AndreiBertescu/FPGA_Cosmic_Radiation_Sensor/Thesis latex project/Anexe/Prima pagina.docx

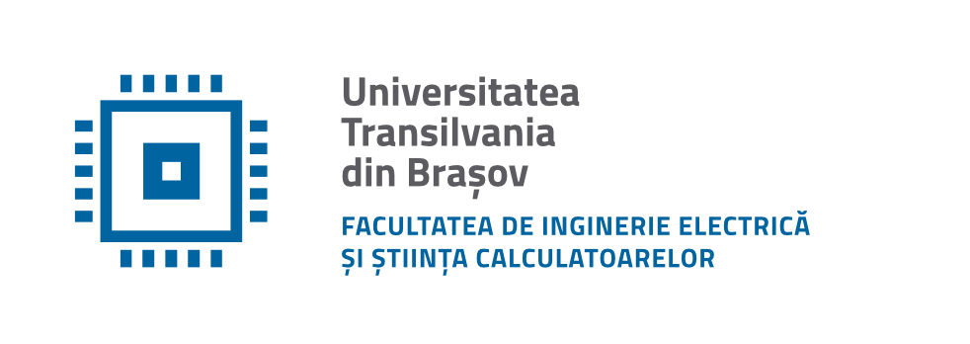
[picture p34: figure]

PROIECT DE DIPLOMĂ

Conducători științifici:

Prof. dr. ing. IVANOVICI Mihail Laurențiu

Șef lucr. dr. ing. POPA Ștefan

Absolvent:

BERTESCU Andrei

BRAȘOV, 2026

Departamentul: Electronică și Calculatoare

Programul de studii: Calculatoare

BERTESCU Andrei

Senzor inteligent de detecție a radiației cosmice, bazat pe FPGA, destinat nanosateliților

Conducători științifici:

Prof. dr. ing. IVANOVICI Mihail Laurențiu

Șef lucr. dr. ing. POPA Ștefan

Brașov, 2026
