AndreiBertescu/FPGA_Cosmic_Radiation_Sensor/Kicad PCB projects/Rev_3.2/PCB_photos/JLCPCB_photos/JLC_price.png

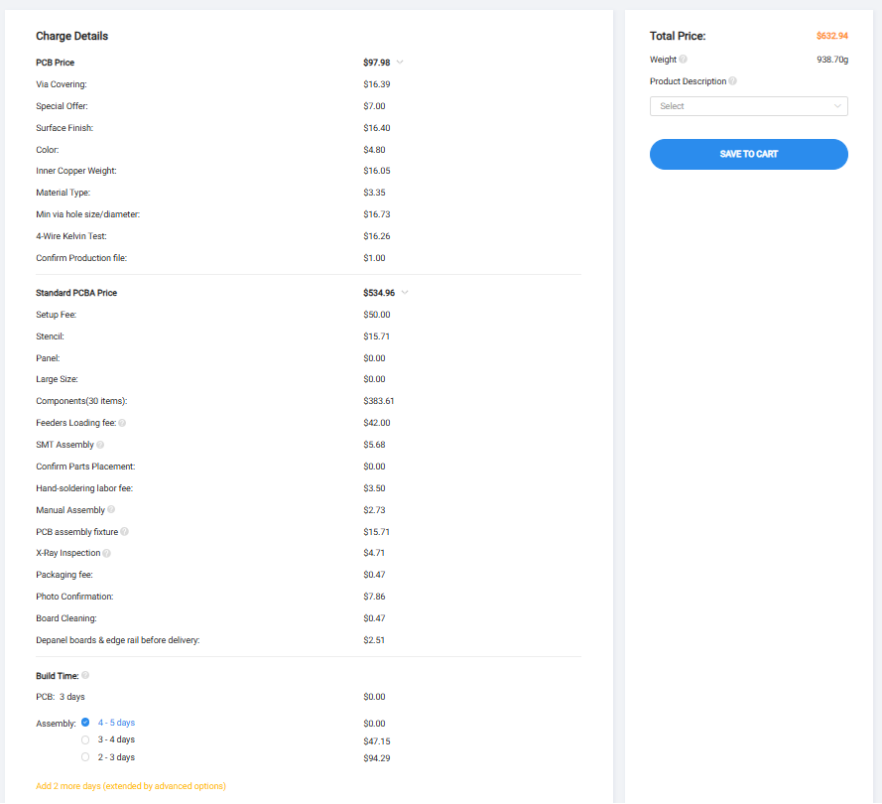
Kicad PCB projects/Rev_3.2/PCB_photos/JLCPCB_photos/JLC_price.png
