AndreiBertescu/FPGA_Cosmic_Radiation_Sensor/Kicad PCB projects/Rev_3.2/PCB_photos/JLCPCB_photos/Real_bottom.jpg

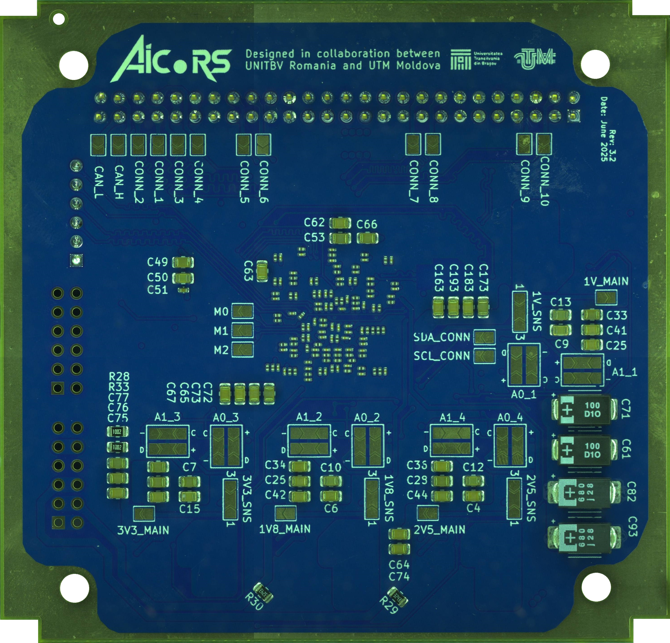
Kicad PCB projects/Rev_3.2/PCB_photos/JLCPCB_photos/Real_bottom.jpg
