AndreiBertescu/FPGA_Cosmic_Radiation_Sensor/Kicad PCB projects/Rev_3.2/PCB_photos/JLCPCB_photos/Render_bottom.png

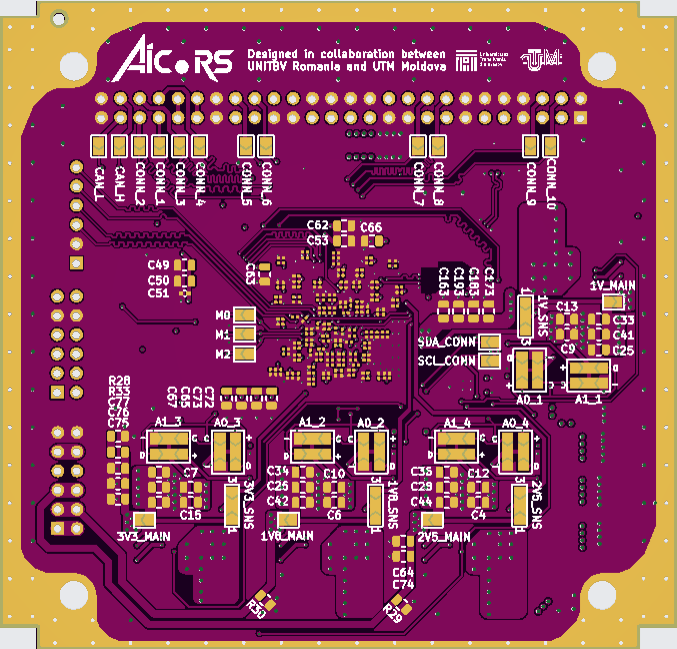
Kicad PCB projects/Rev_3.2/PCB_photos/JLCPCB_photos/Render_bottom.png
