AndreiBertescu/FPGA_Cosmic_Radiation_Sensor/Kicad PCB projects/Rev_3.2/PCB_photos/JLCPCB_photos/Render_top.png

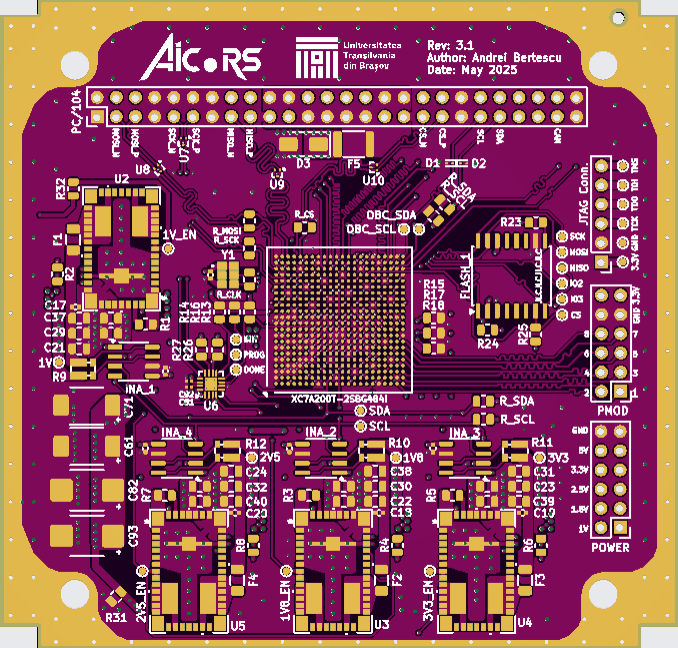
Kicad PCB projects/Rev_3.2/PCB_photos/JLCPCB_photos/Render_top.png
