AndreiBertescu/FPGA_Cosmic_Radiation_Sensor/Kicad PCB projects/Rev_3.2/PCB_photos/JLCPCB_photos/Xray_1.jpg

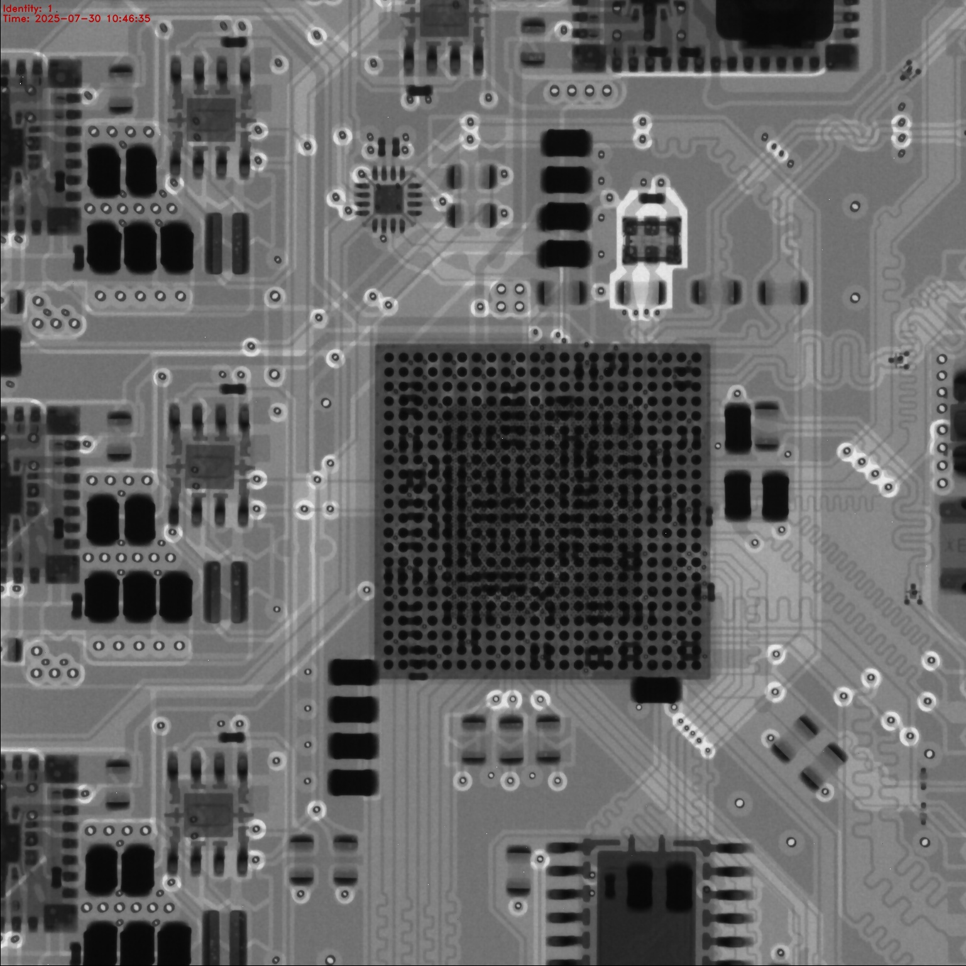
Kicad PCB projects/Rev_3.2/PCB_photos/JLCPCB_photos/Xray_1.jpg
