AndreiBertescu/FPGA_Cosmic_Radiation_Sensor/Kicad PCB projects/Rev_3.2/PCB_photos/KiCad_photos/3D_BOTTOM.png

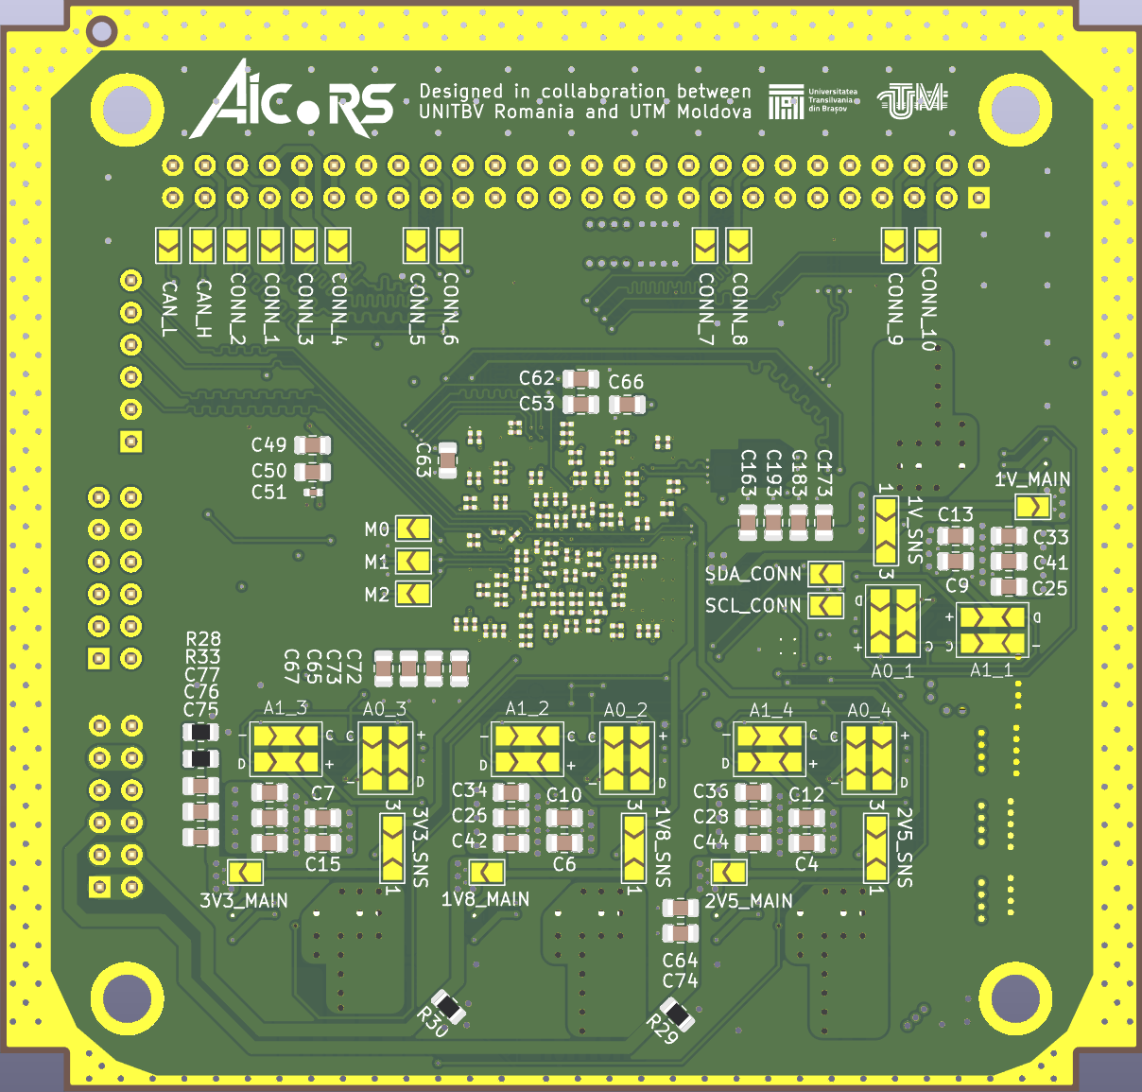
Kicad PCB projects/Rev_3.2/PCB_photos/KiCad_photos/3D_BOTTOM.png
