AndreiBertescu/FPGA_Cosmic_Radiation_Sensor/Kicad PCB projects/Rev_3.2/PCB_photos/KiCad_photos/hw_layout_bottom.png

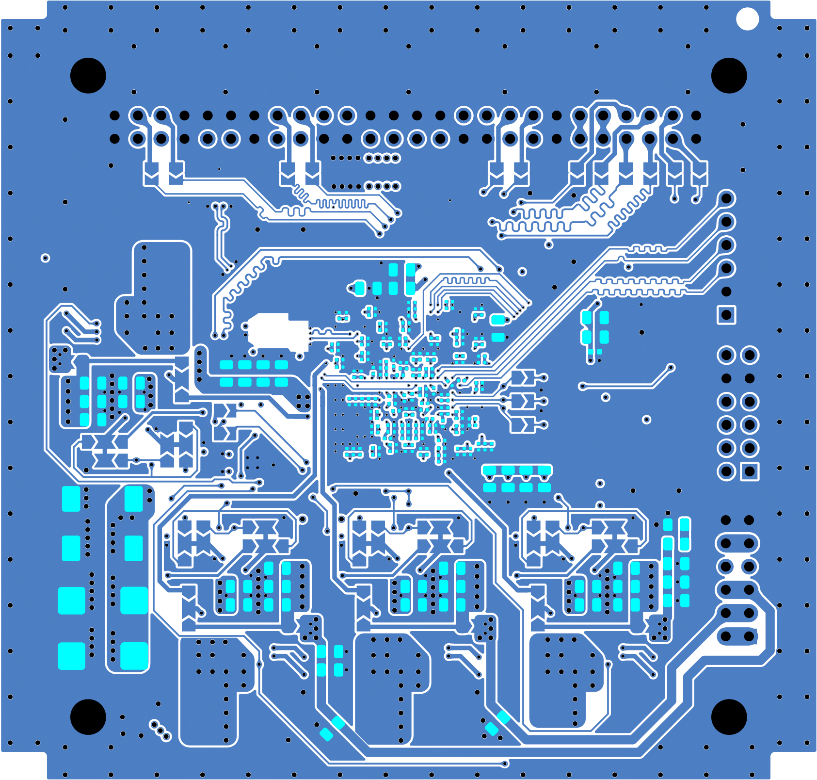
Kicad PCB projects/Rev_3.2/PCB_photos/KiCad_photos/hw_layout_bottom.png
