AndreiBertescu/FPGA_Cosmic_Radiation_Sensor/Kicad PCB projects/Rev_3.2/PCB_photos/KiCad_photos/hw_layout_top.png

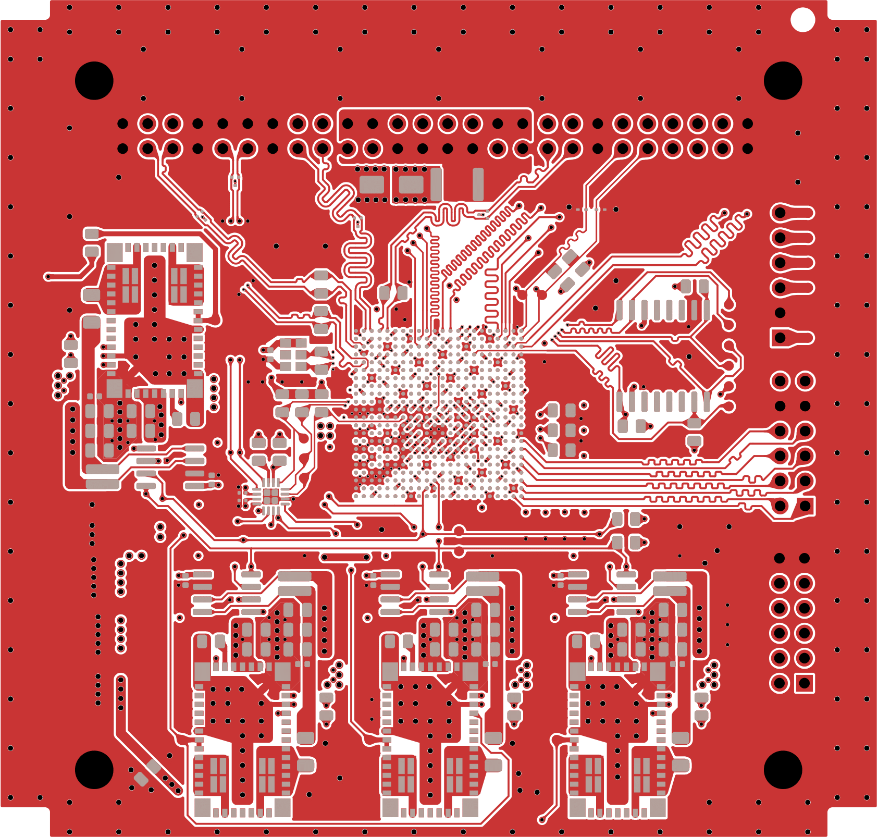
Kicad PCB projects/Rev_3.2/PCB_photos/KiCad_photos/hw_layout_top.png
