AndreiBertescu/FPGA_Cosmic_Radiation_Sensor/Thesis latex project/Images/eye_diagram.png

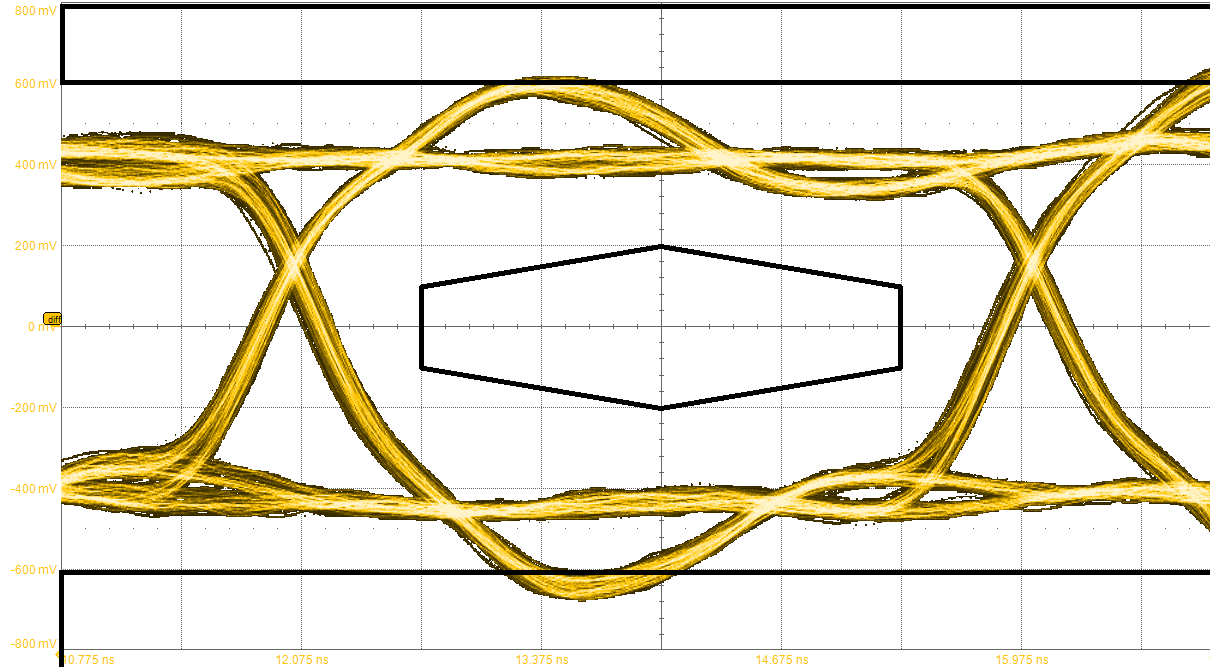
Thesis latex project/Images/eye_diagram.png
