AndreiBertescu/FPGA_Cosmic_Radiation_Sensor/Thesis latex project/Images/ferrite_bead_interference_3.png

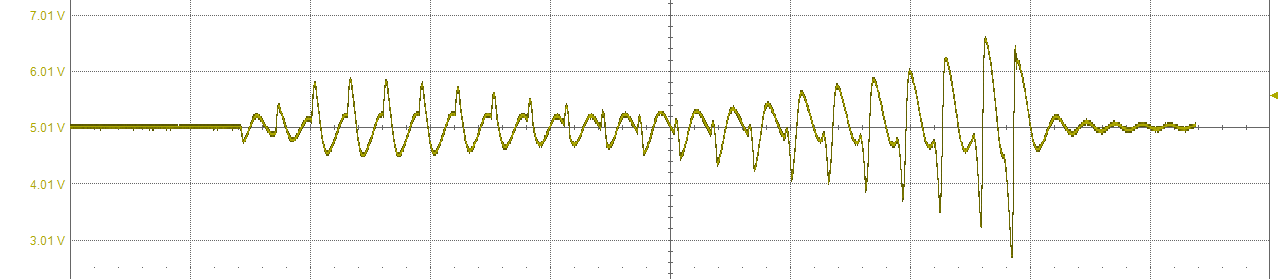
Thesis latex project/Images/ferrite_bead_interference_3.png
