AndreiBertescu/FPGA_Cosmic_Radiation_Sensor/Thesis latex project/Images/Main_sim.png

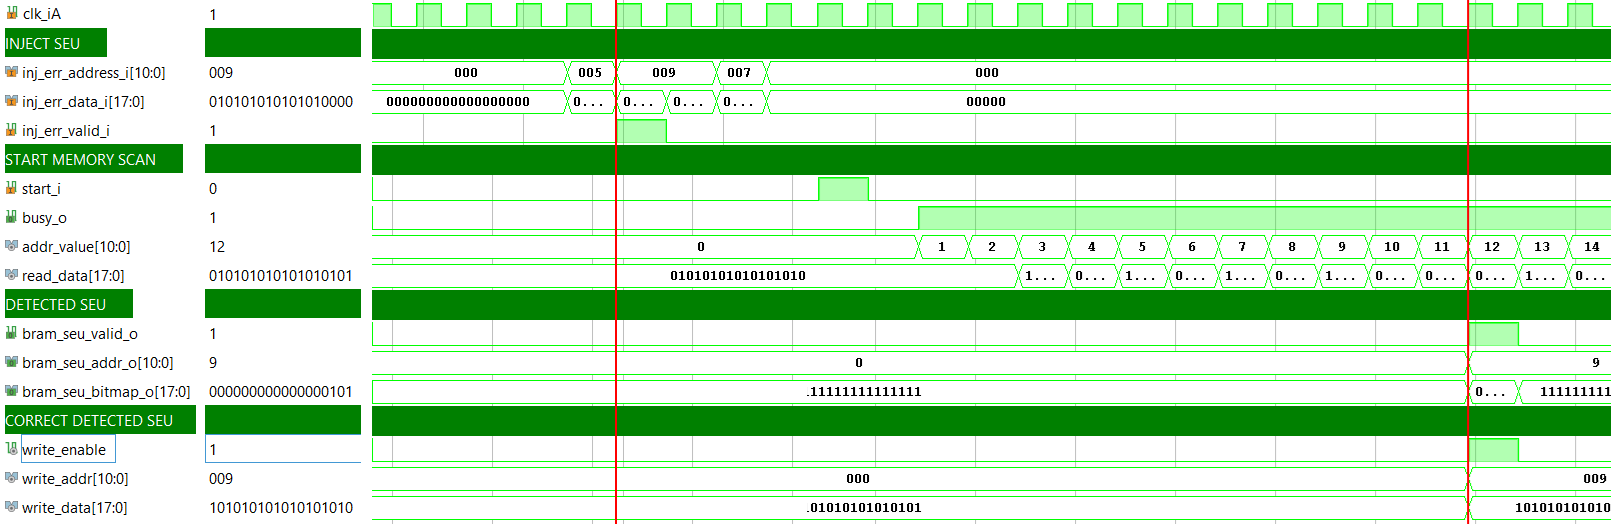
Thesis latex project/Images/Main_sim.png
