AndreiBertescu/FPGA_Cosmic_Radiation_Sensor/Thesis latex project/Images/power_spike.png

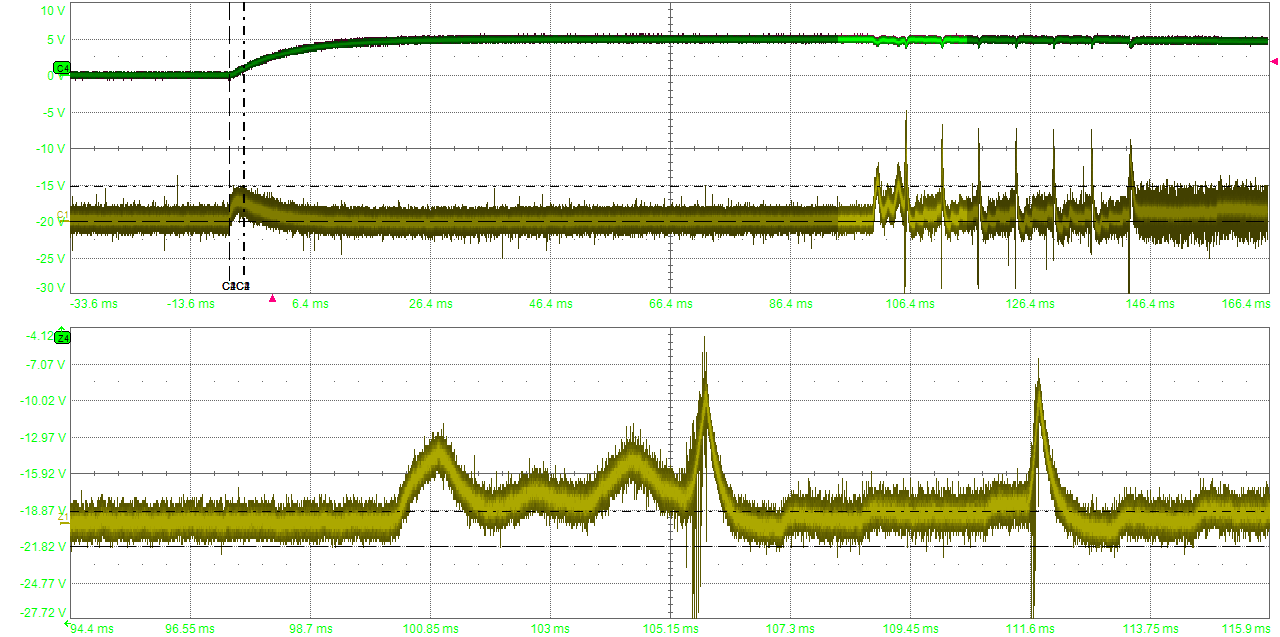
Thesis latex project/Images/power_spike.png
