AndreiBertescu/FPGA_Cosmic_Radiation_Sensor/Arduino Test projects/Arduino_SPI_slave/SPI_Frame_0.png

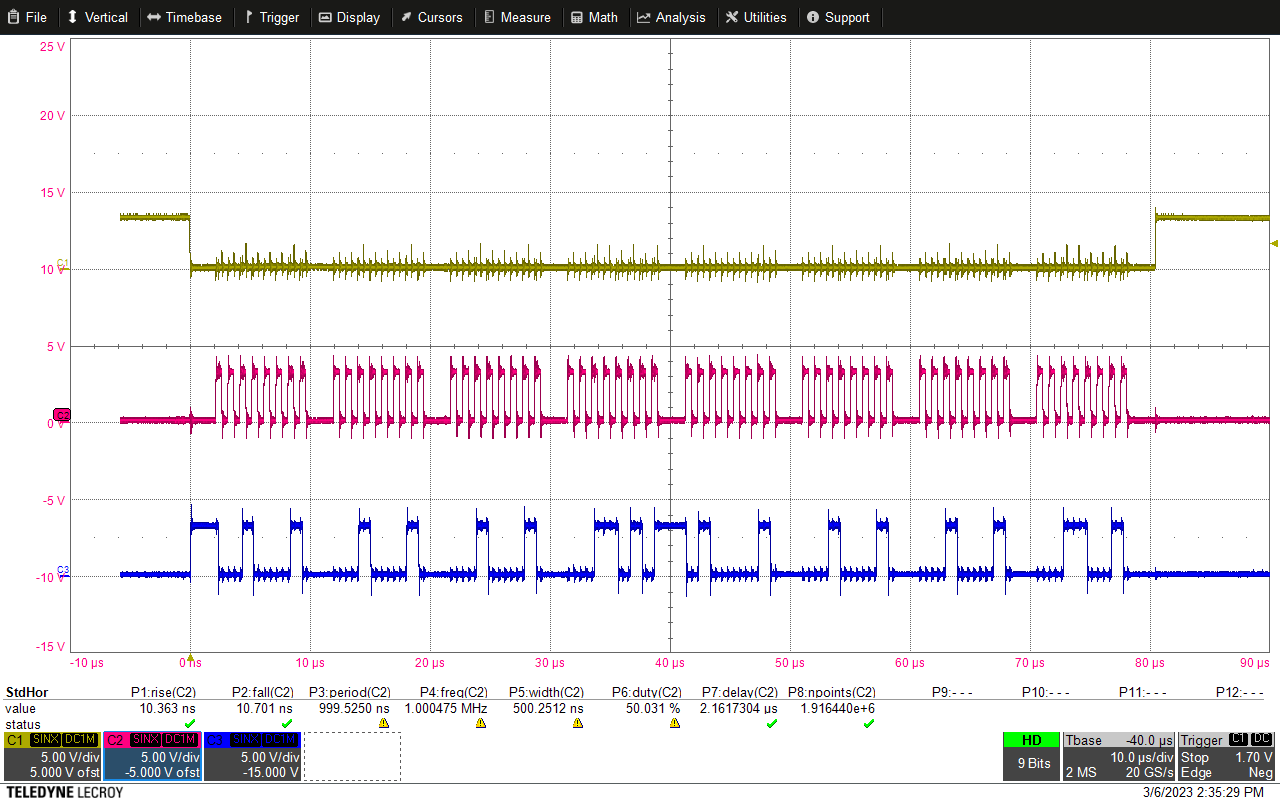
Arduino Test projects/Arduino_SPI_slave/SPI_Frame_0.png
