AndreiBertescu/FPGA_Cosmic_Radiation_Sensor/Kicad PCB projects/Test_photos/Rev_3/100MHz_clock_jitter_kit.png

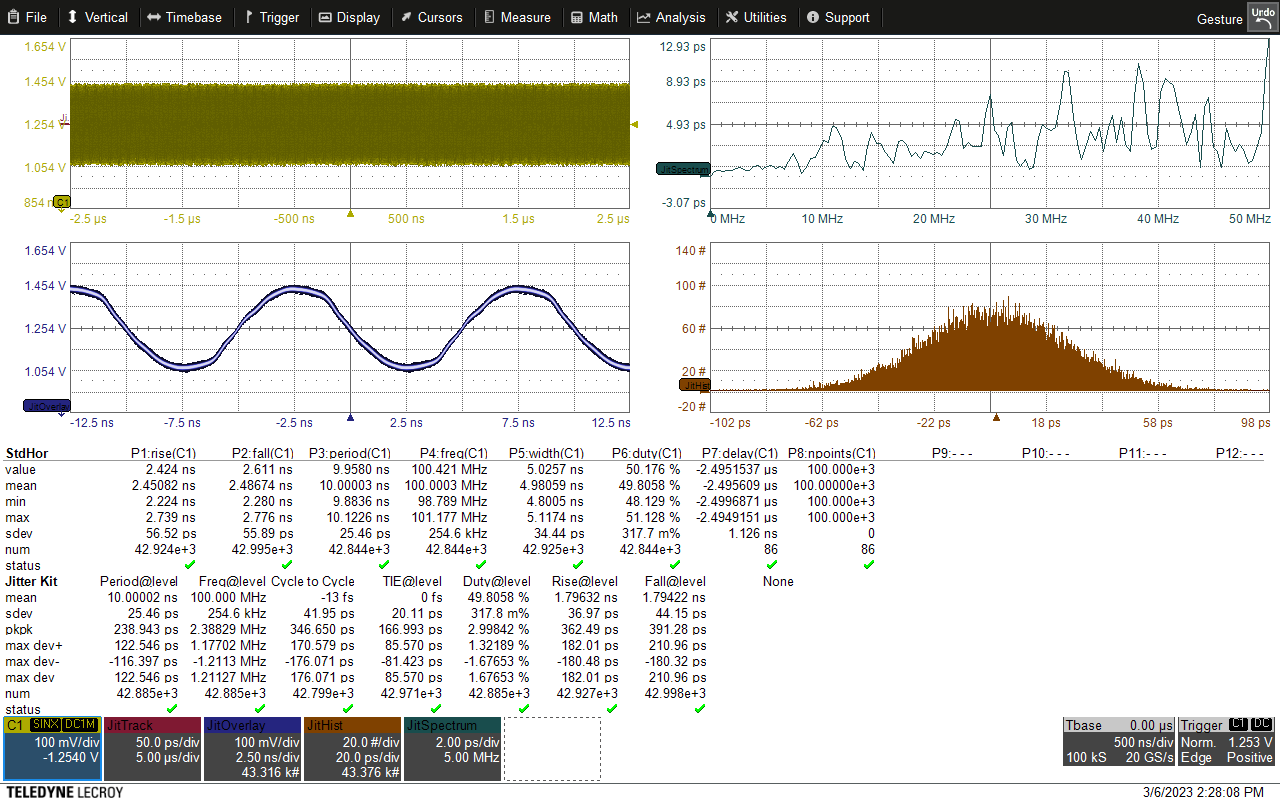
Kicad PCB projects/Test_photos/Rev_3/100MHz_clock_jitter_kit.png
