AndreiBertescu/FPGA_Cosmic_Radiation_Sensor/Kicad PCB projects/Test_photos/Rev_3/Eye_conn_10_250MHz.png

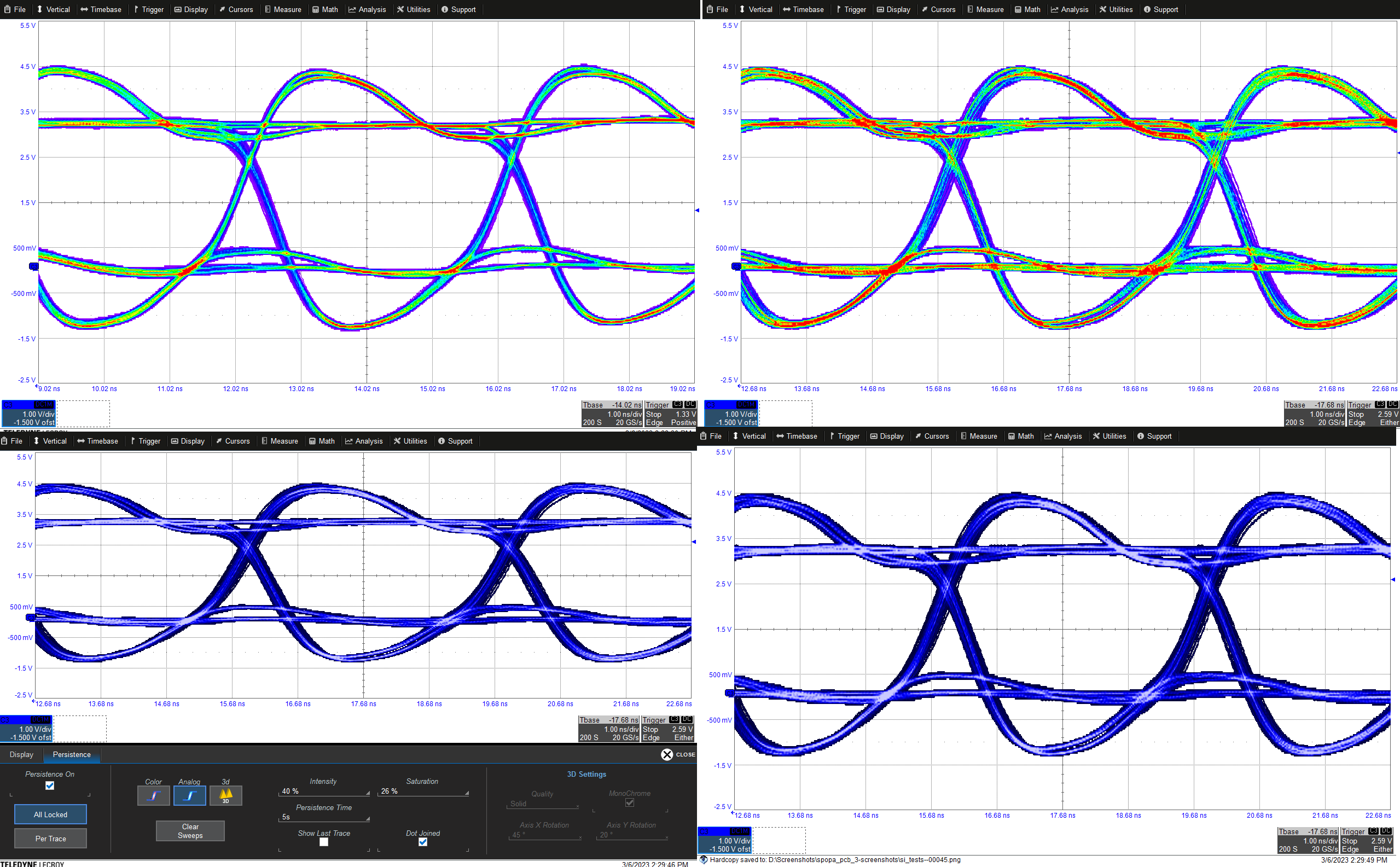
Kicad PCB projects/Test_photos/Rev_3/Eye_conn_10_250MHz.png
