AndreiBertescu/FPGA_Cosmic_Radiation_Sensor/Kicad PCB projects/Test_photos/Rev_3/Eye_sck_p_LVDS_sck_100MHz.png

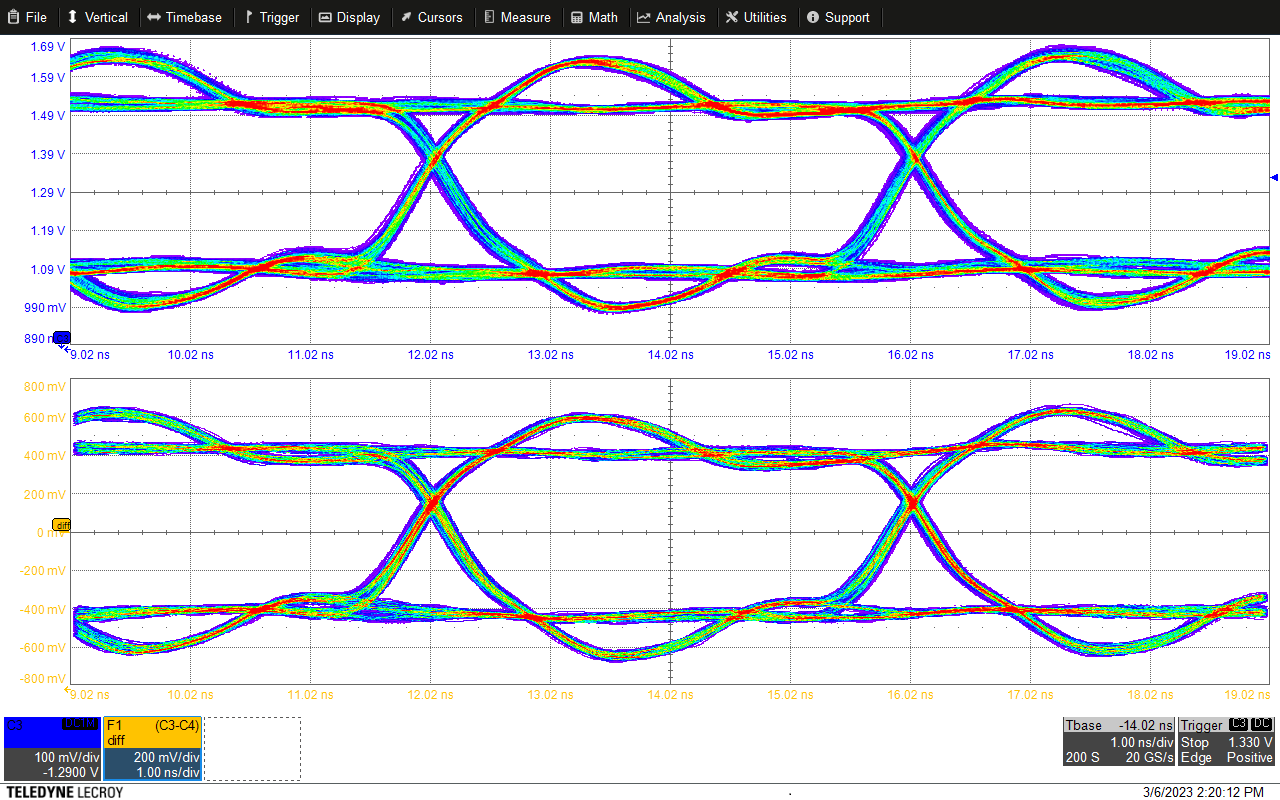
Kicad PCB projects/Test_photos/Rev_3/Eye_sck_p_LVDS_sck_100MHz.png
