AndreiBertescu/FPGA_Cosmic_Radiation_Sensor/Kicad PCB projects/Test_photos/Rev_3/JitterKit_clk_p_100MHz.png

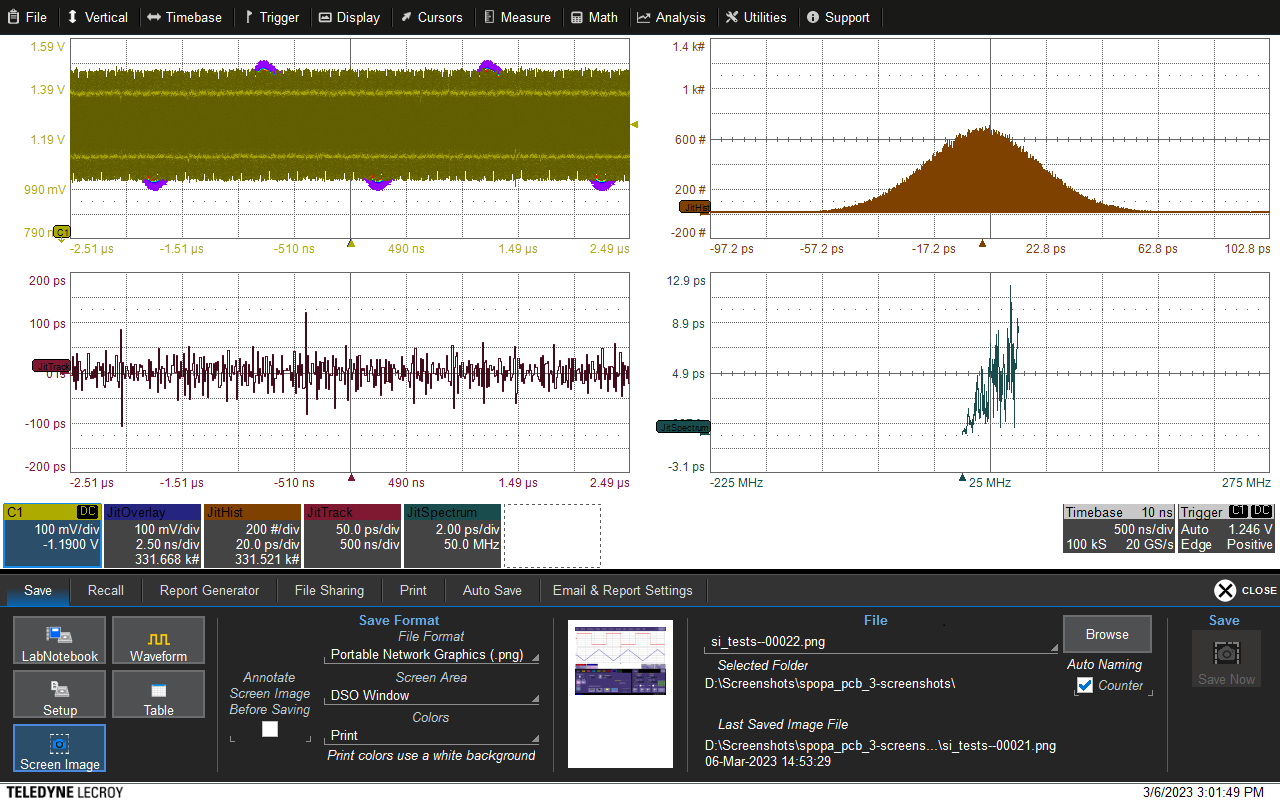
Kicad PCB projects/Test_photos/Rev_3/JitterKit_clk_p_100MHz.png
