AndreiBertescu/FPGA_Cosmic_Radiation_Sensor/Kicad PCB projects/Test_photos/Rev_3/JitterKit_sck_250MHz.png

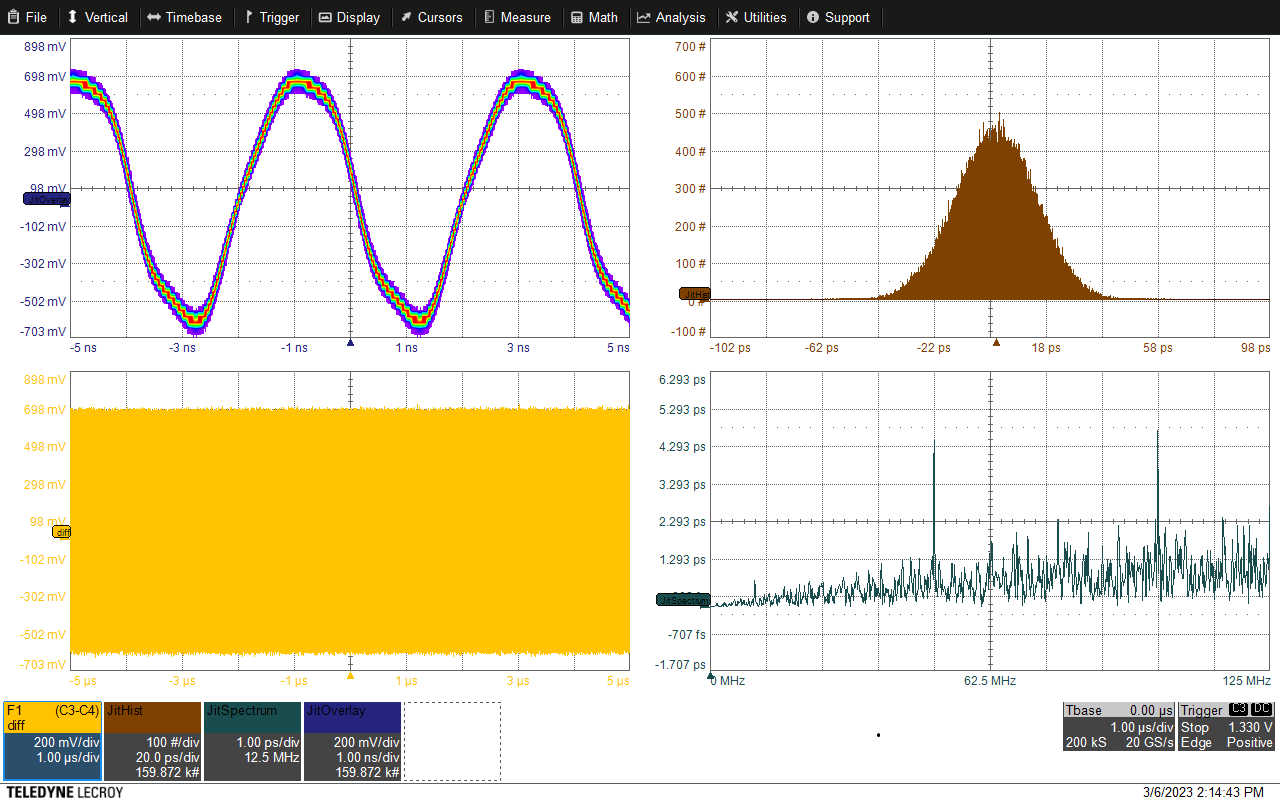
Kicad PCB projects/Test_photos/Rev_3/JitterKit_sck_250MHz.png
