AndreiBertescu/FPGA_Cosmic_Radiation_Sensor/Kicad PCB projects/Test_photos/Rev_3/Logic_analyzer_esp_spi.png

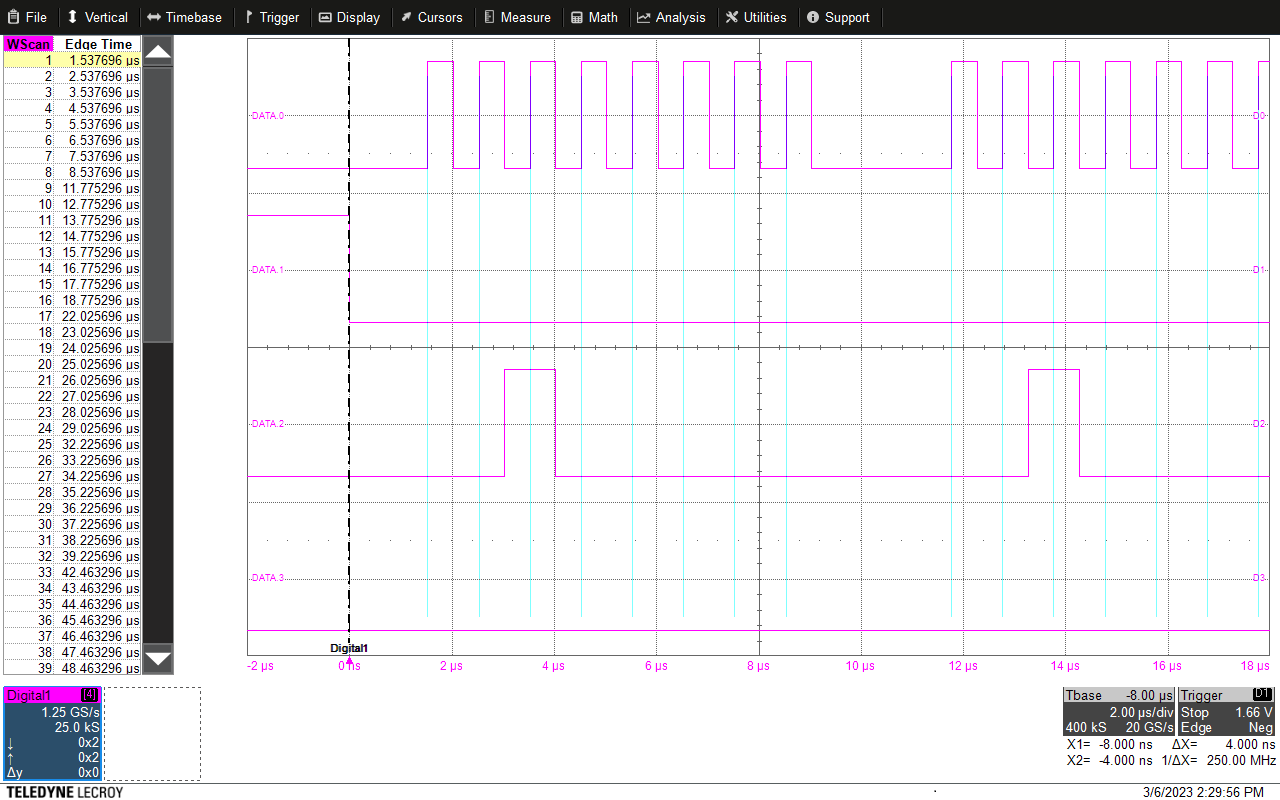
Kicad PCB projects/Test_photos/Rev_3/Logic_analyzer_esp_spi.png
