AndreiBertescu/FPGA_Cosmic_Radiation_Sensor/Kicad PCB projects/Test_photos/Rev_3/LVDS_sck_10MHz.png

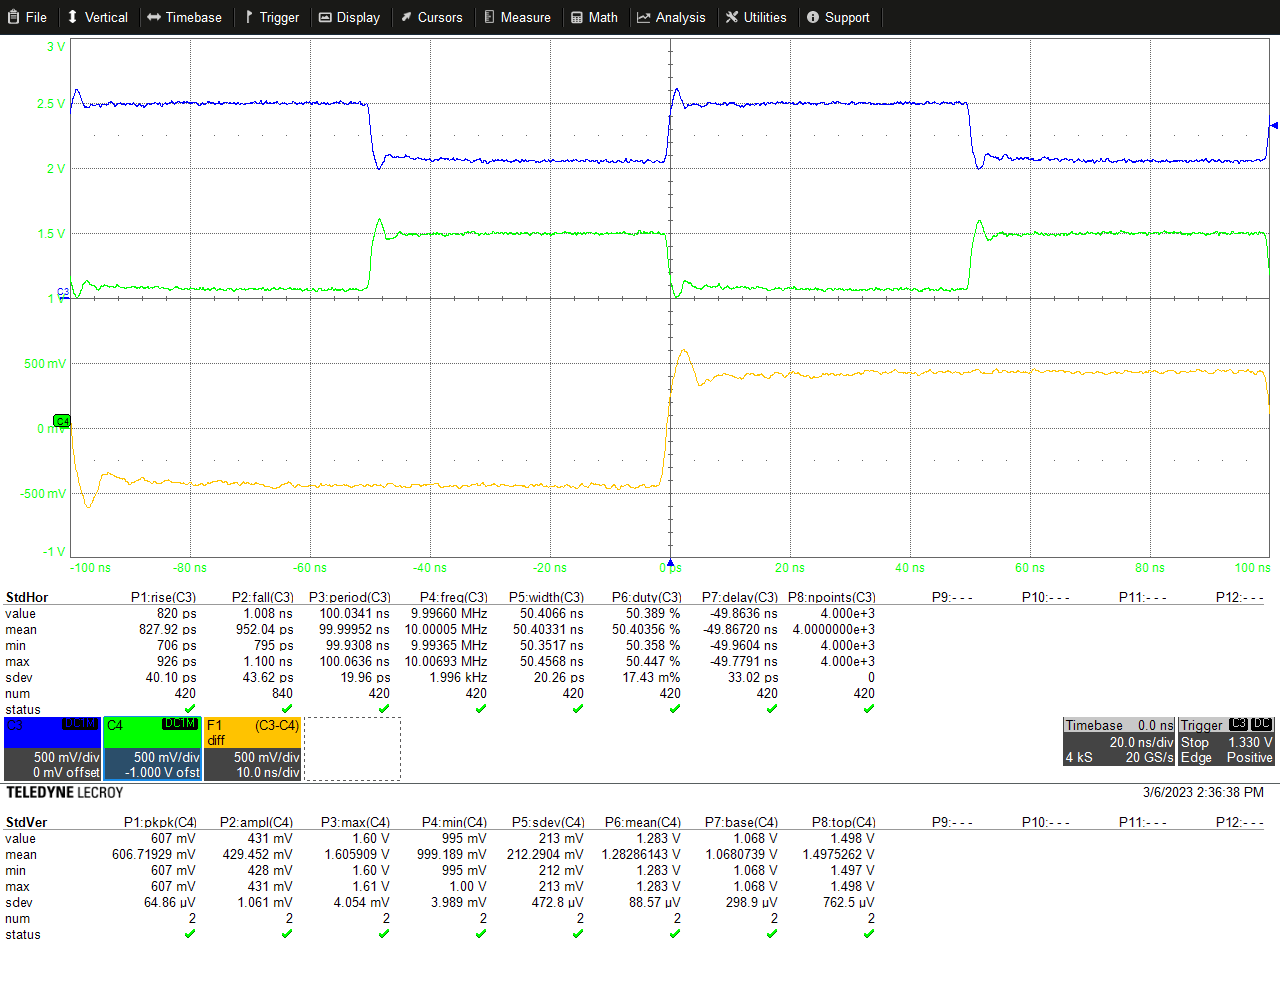
Kicad PCB projects/Test_photos/Rev_3/LVDS_sck_10MHz.png
