AndreiBertescu/FPGA_Cosmic_Radiation_Sensor/Kicad PCB projects/Test_photos/Rev_3/LVDS_sck_100MHz.png

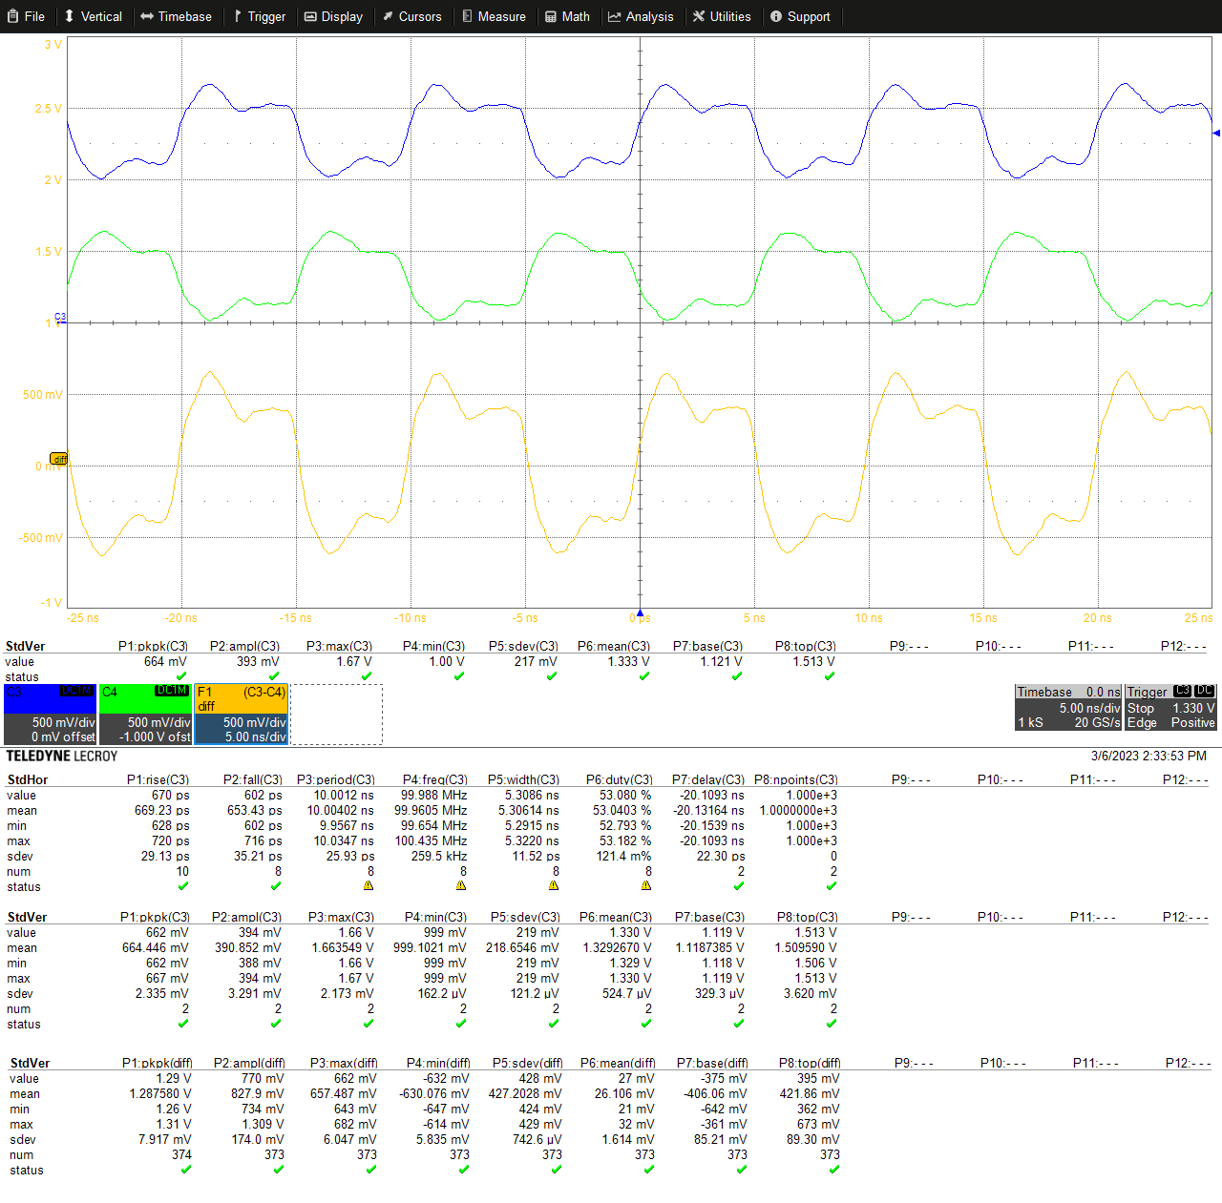
Kicad PCB projects/Test_photos/Rev_3/LVDS_sck_100MHz.png
