AndreiBertescu/FPGA_Cosmic_Radiation_Sensor/Kicad PCB projects/Test_photos/Rev_3/Overshoot_gpio_6_10MHz.png

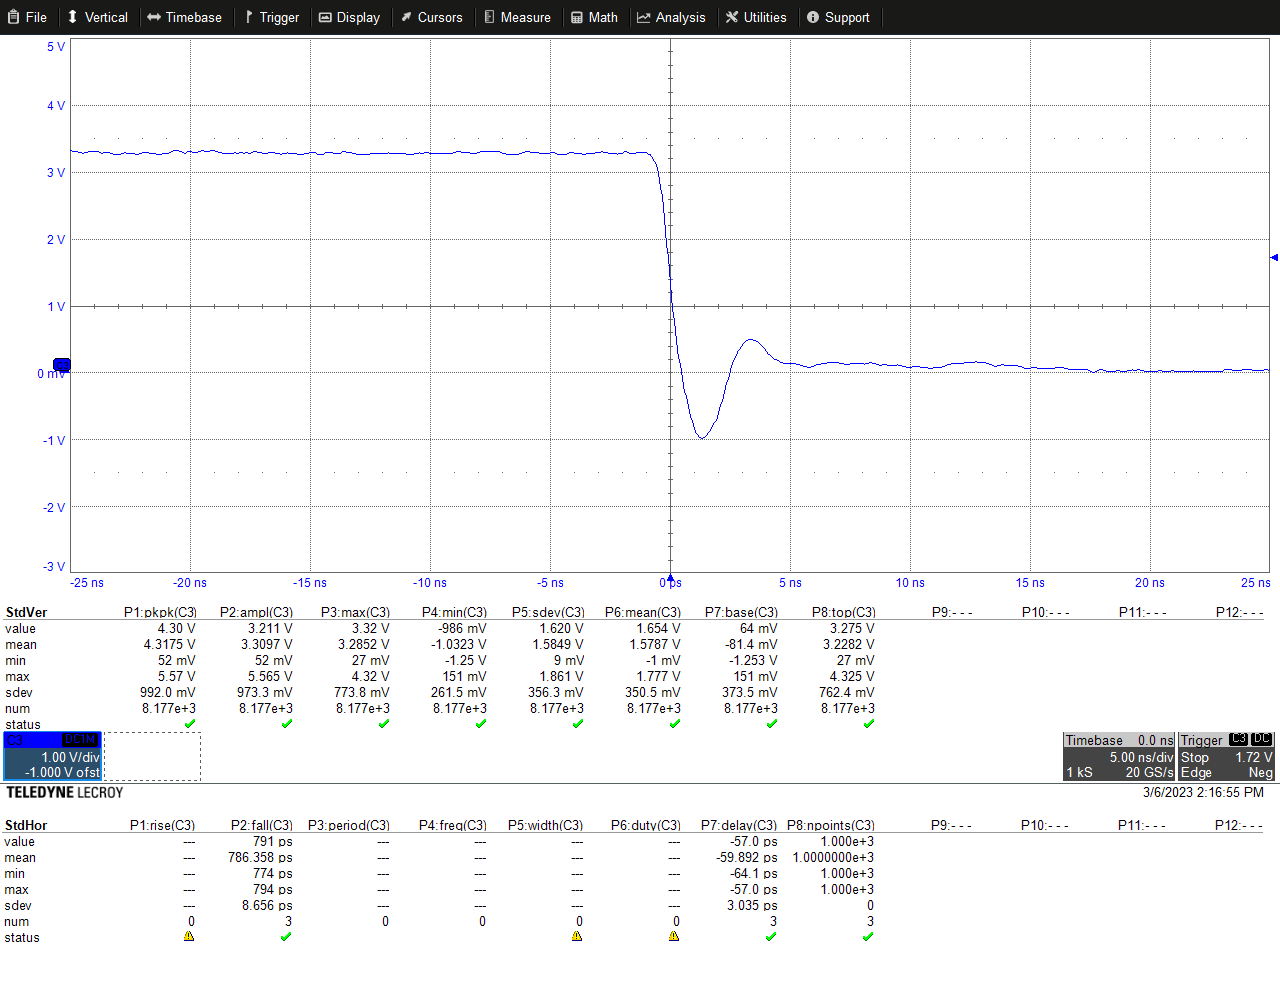
Kicad PCB projects/Test_photos/Rev_3/Overshoot_gpio_6_10MHz.png
