AndreiBertescu/FPGA_Cosmic_Radiation_Sensor/Kicad PCB projects/Test_photos/Rev_3/power_spike--00007.png

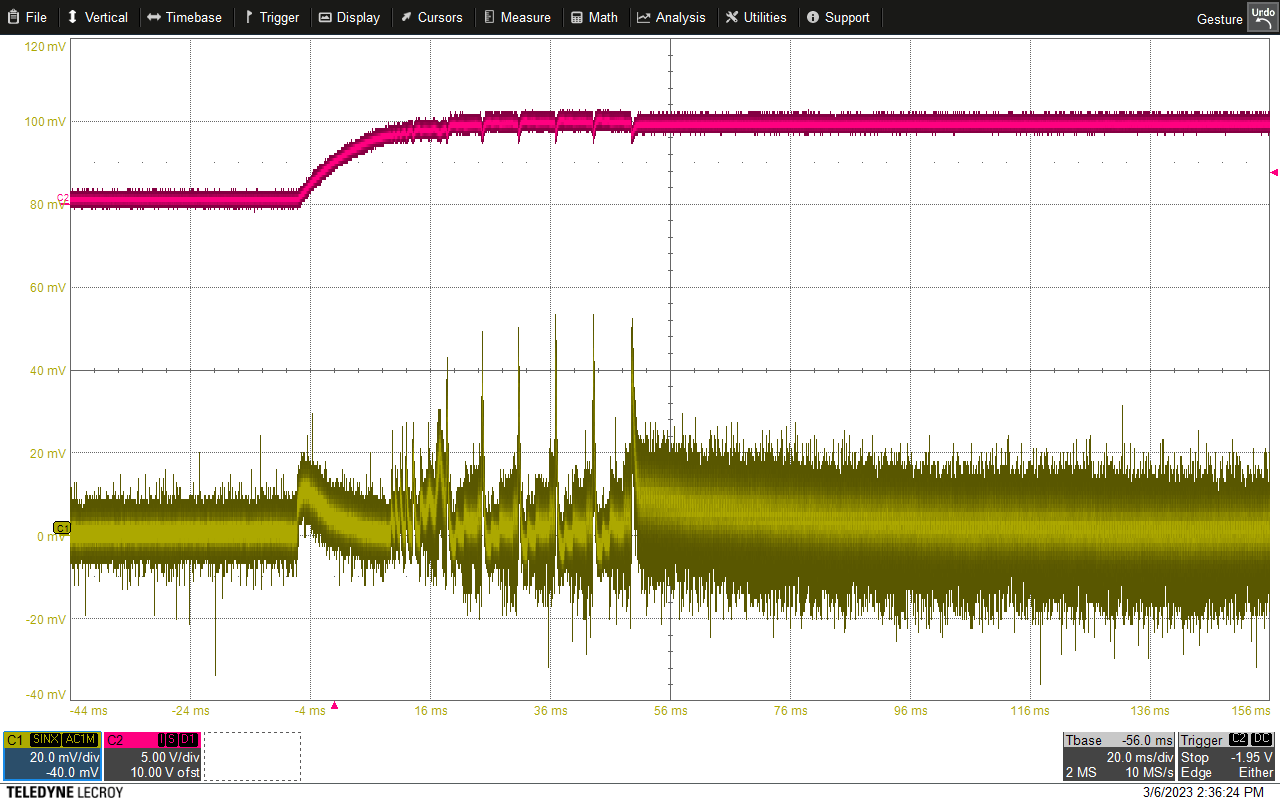
Kicad PCB projects/Test_photos/Rev_3/power_spike--00007.png
