AndreiBertescu/FPGA_Cosmic_Radiation_Sensor/Kicad PCB projects/Test_photos/Rev_3/power_spike--00012.png

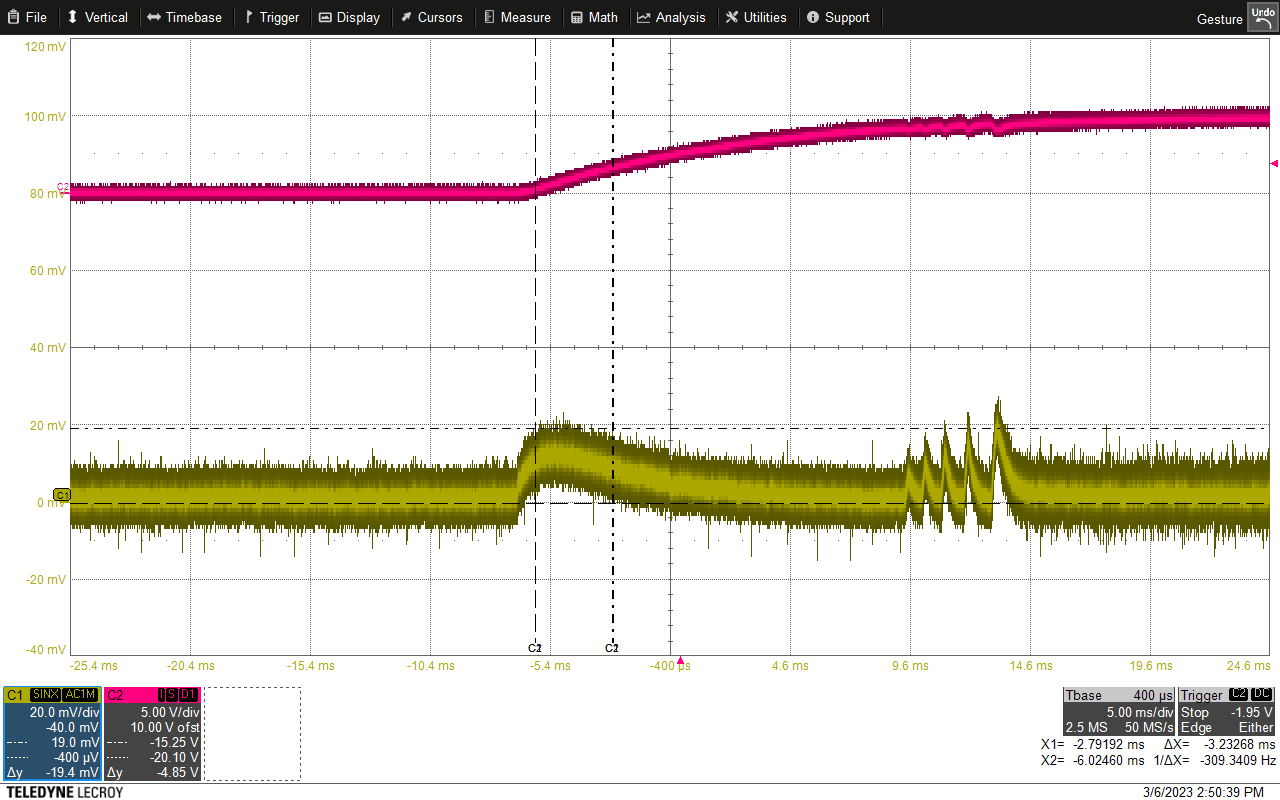
Kicad PCB projects/Test_photos/Rev_3/power_spike--00012.png
