AndreiBertescu/FPGA_Cosmic_Radiation_Sensor/Kicad PCB projects/Test_photos/Rev_3/power_spike--00016.png

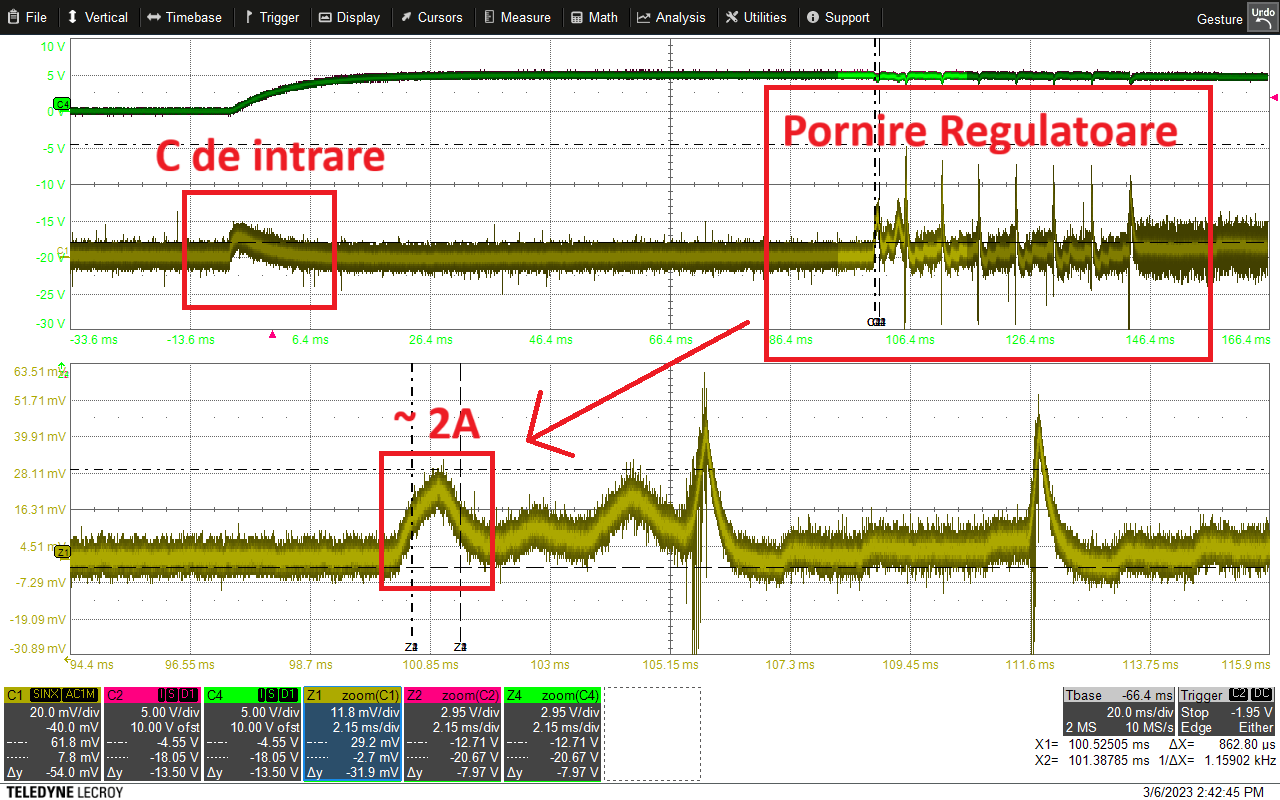
Kicad PCB projects/Test_photos/Rev_3/power_spike--00016.png
