AndreiBertescu/FPGA_Cosmic_Radiation_Sensor/Kicad PCB projects/Test_photos/Rev_3/PwrUp_Sequence.png

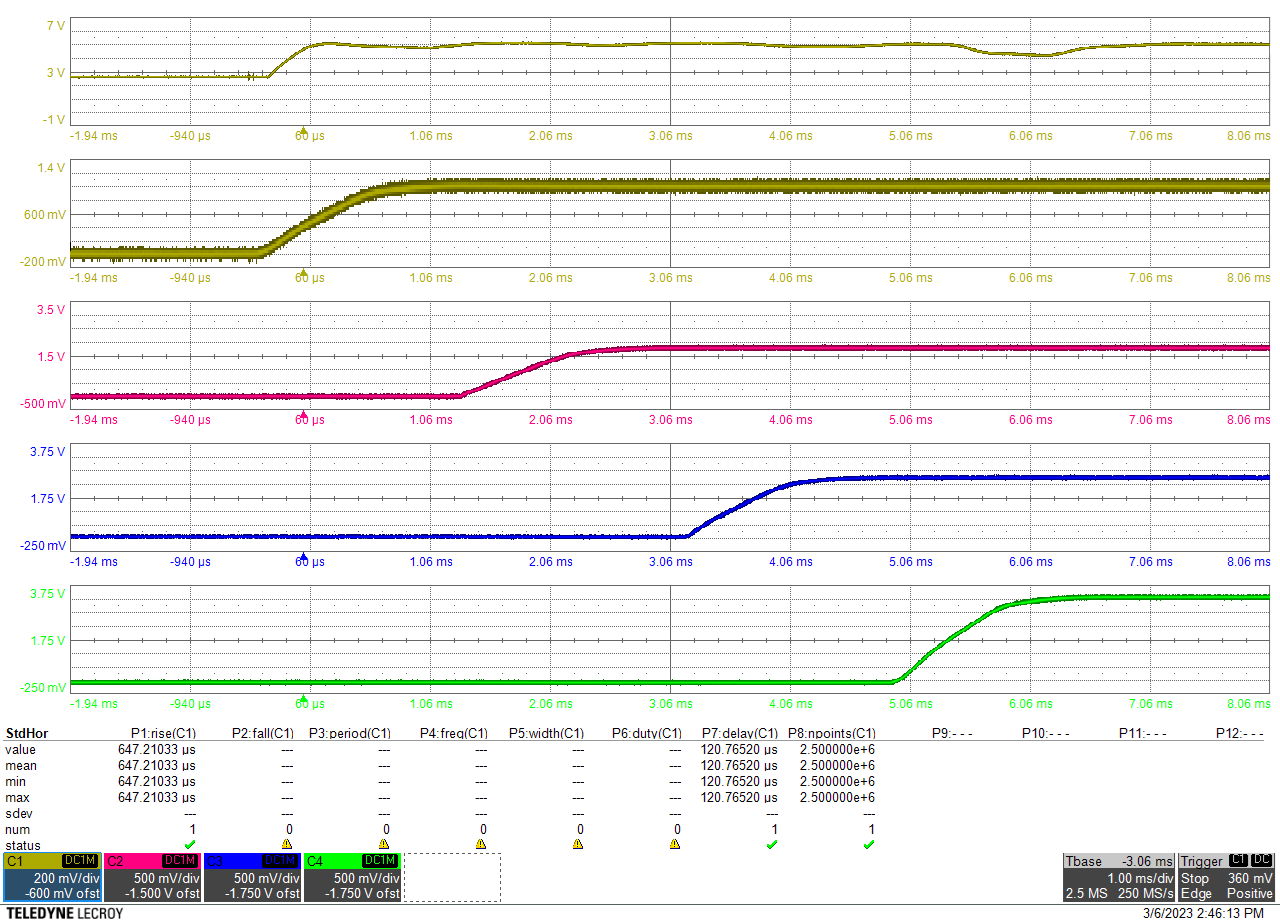
Kicad PCB projects/Test_photos/Rev_3/PwrUp_Sequence.png
