AndreiBertescu/FPGA_Cosmic_Radiation_Sensor/Kicad PCB projects/Test_photos/Rev_3/RiseTime_scl_1KHz.png

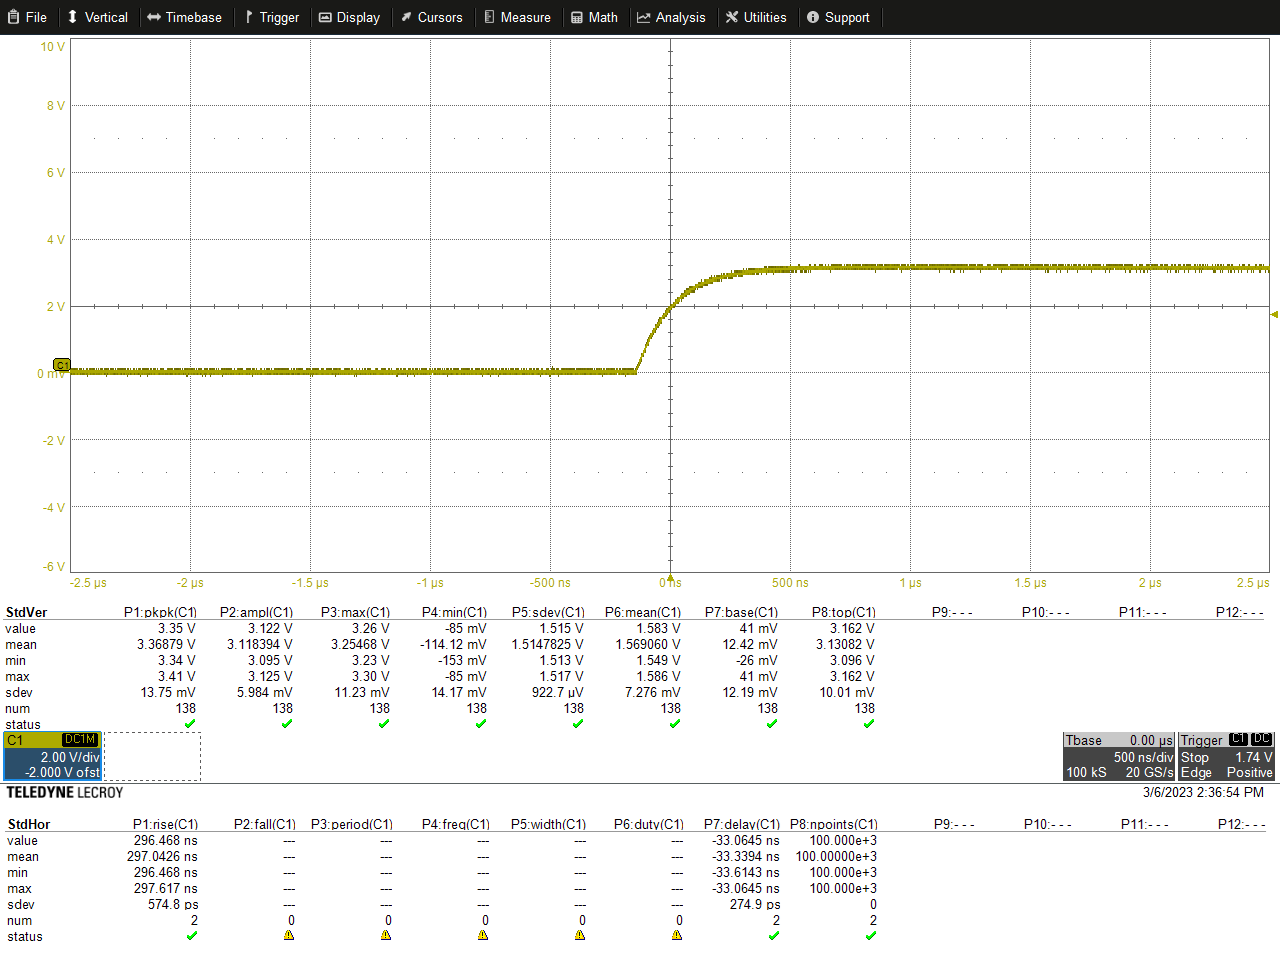
Kicad PCB projects/Test_photos/Rev_3/RiseTime_scl_1KHz.png
