AndreiBertescu/FPGA_Cosmic_Radiation_Sensor/Kicad PCB projects/Test_photos/Rev_3/Skew_conn_10_1_10MHz.png.png

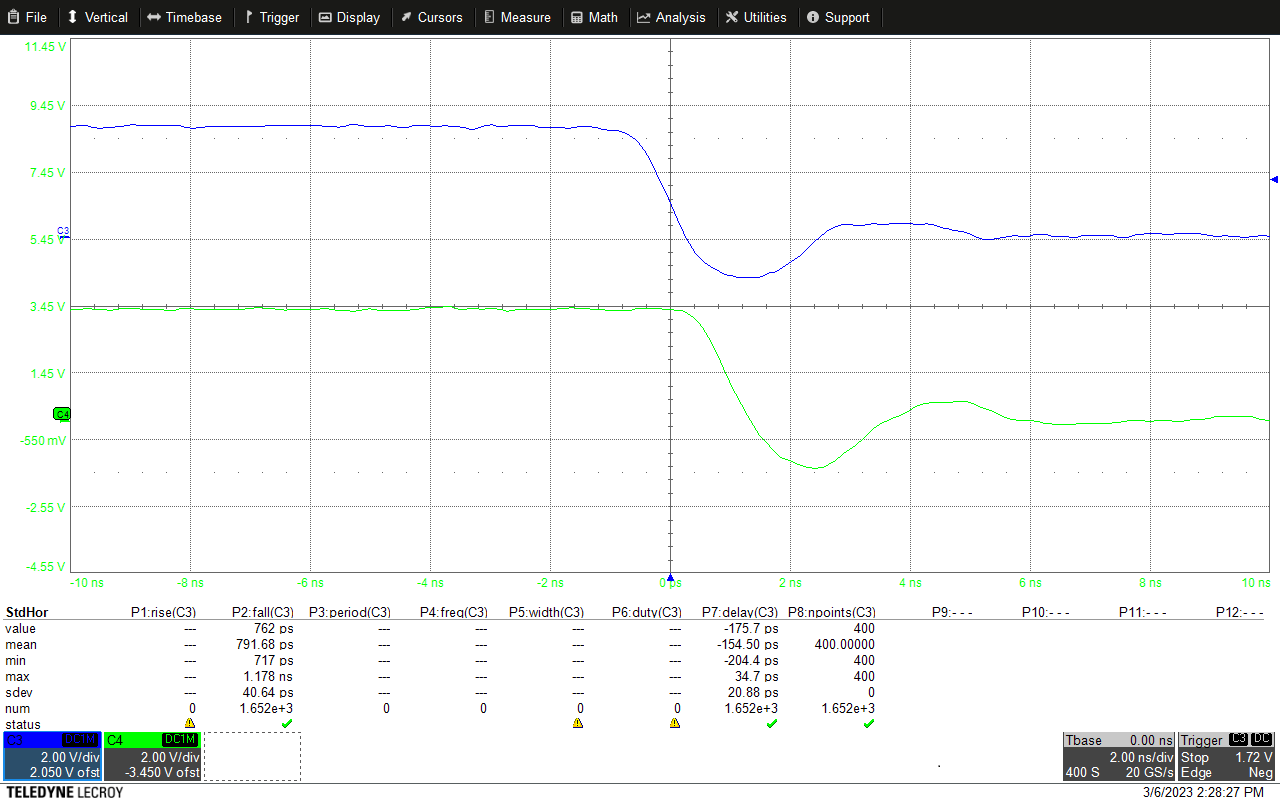
Kicad PCB projects/Test_photos/Rev_3/Skew_conn_10_1_10MHz.png.png
