AndreiBertescu/FPGA_Cosmic_Radiation_Sensor/Kicad PCB projects/Test_photos/Rev_3/Skew_conn_10_gpio_8_10MHz.png

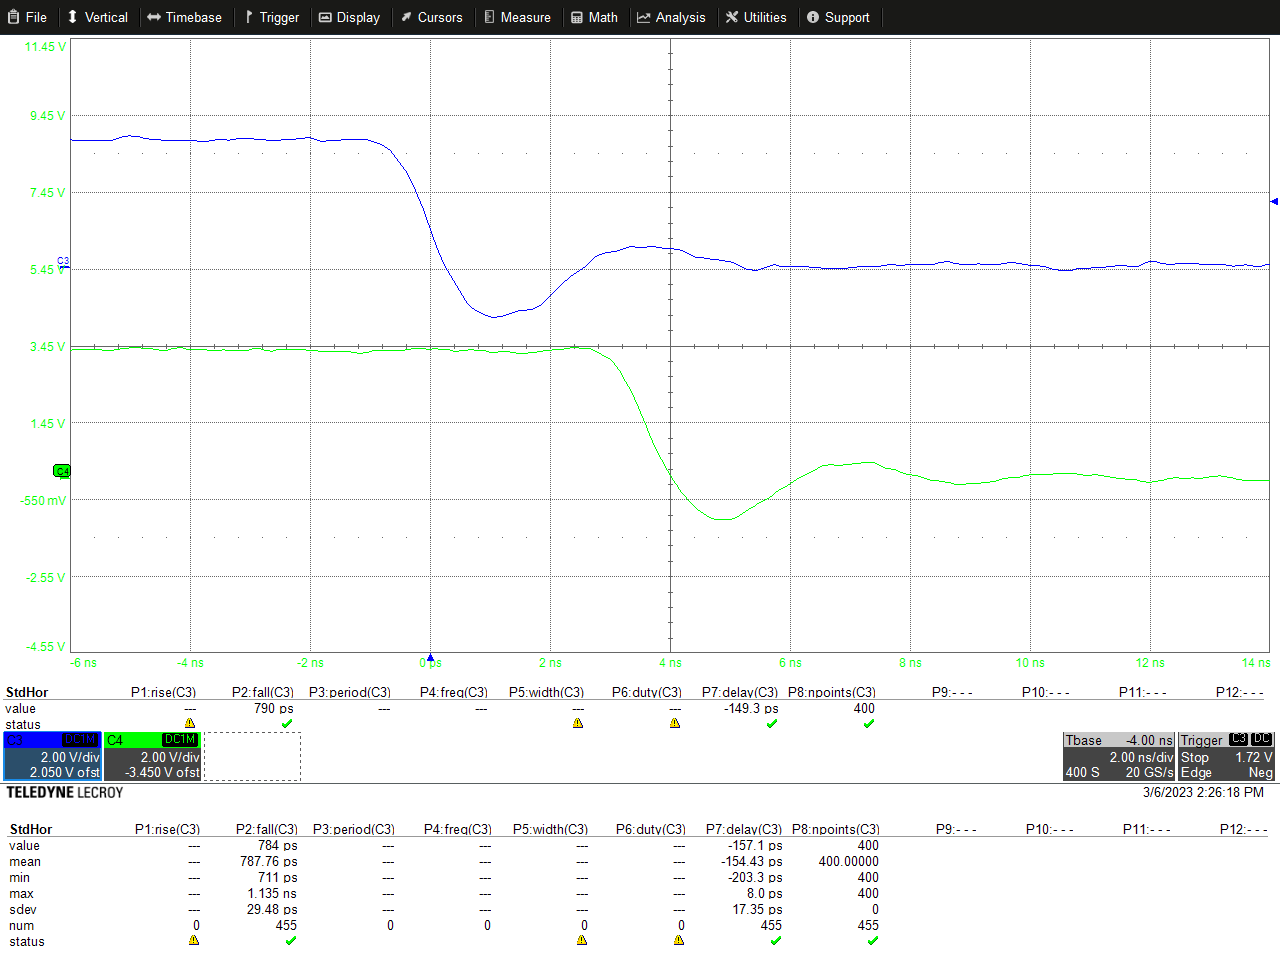
Kicad PCB projects/Test_photos/Rev_3/Skew_conn_10_gpio_8_10MHz.png
