AndreiBertescu/FPGA_Cosmic_Radiation_Sensor/Kicad PCB projects/Test_photos/Rev_3/SPI_Frame_0.png

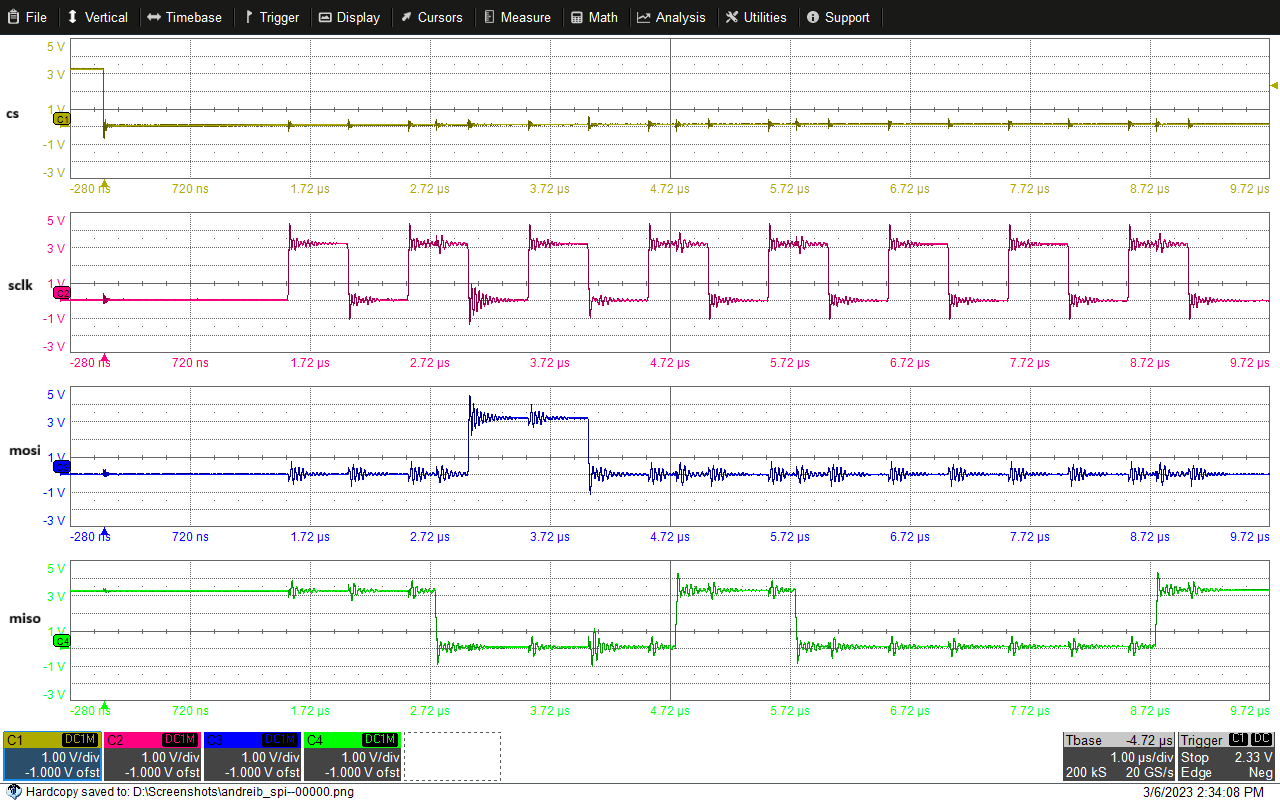
Kicad PCB projects/Test_photos/Rev_3/SPI_Frame_0.png
