AndreiBertescu/FPGA_Cosmic_Radiation_Sensor/Kicad PCB projects/Test_photos/Rev_3/Xtalk_conn10_9_1KHz.png

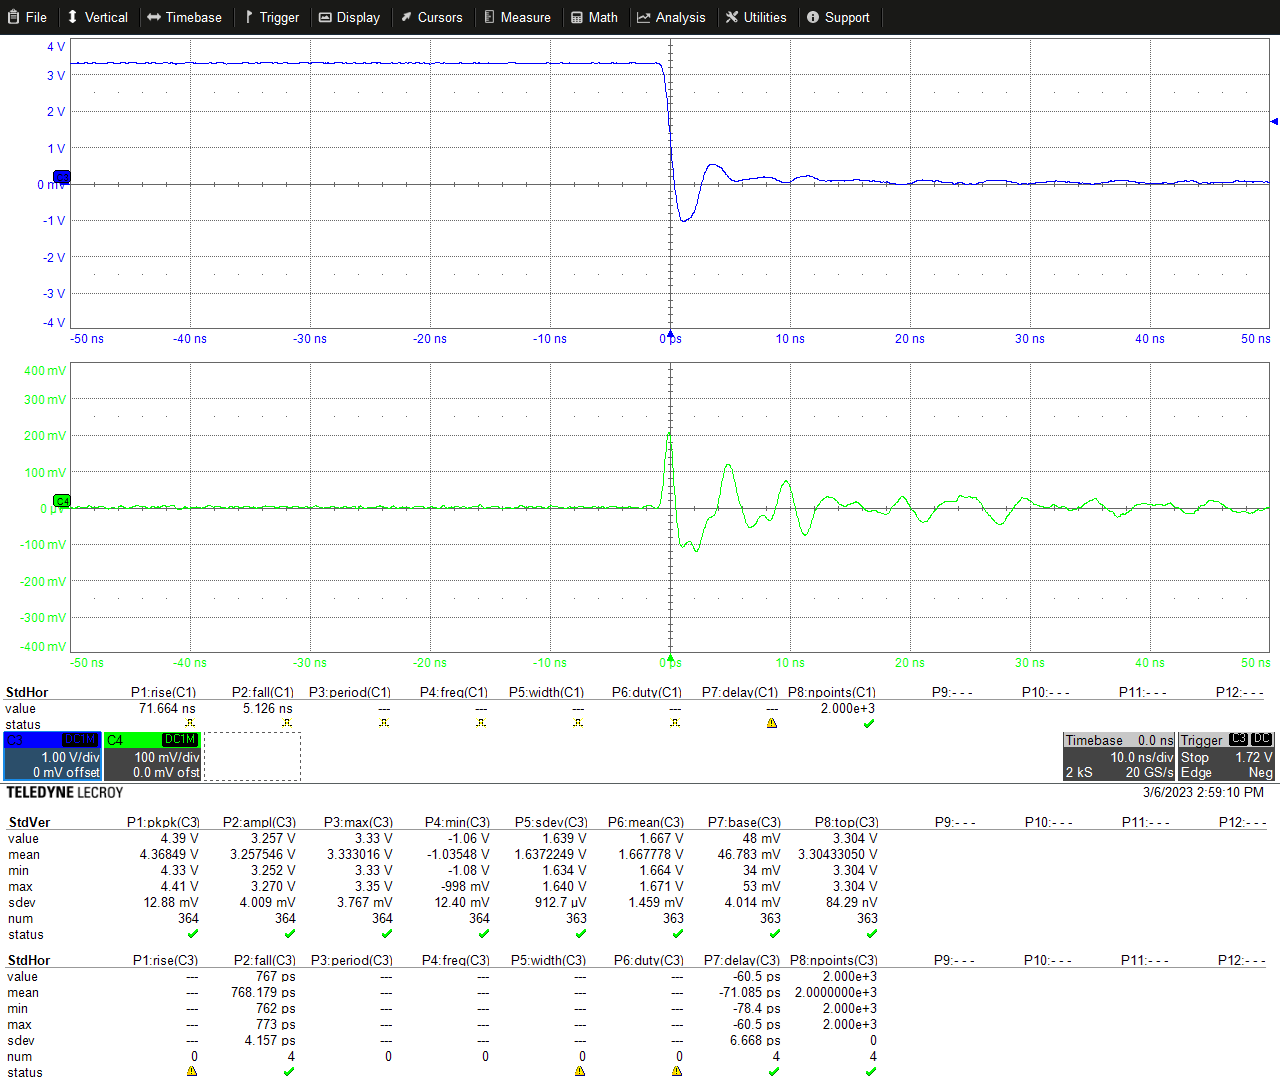
Kicad PCB projects/Test_photos/Rev_3/Xtalk_conn10_9_1KHz.png
