AndreiBertescu/FPGA_Cosmic_Radiation_Sensor/Kicad PCB projects/Test_photos/Rev_3/Xtalk_conn10_9_10MHz.png

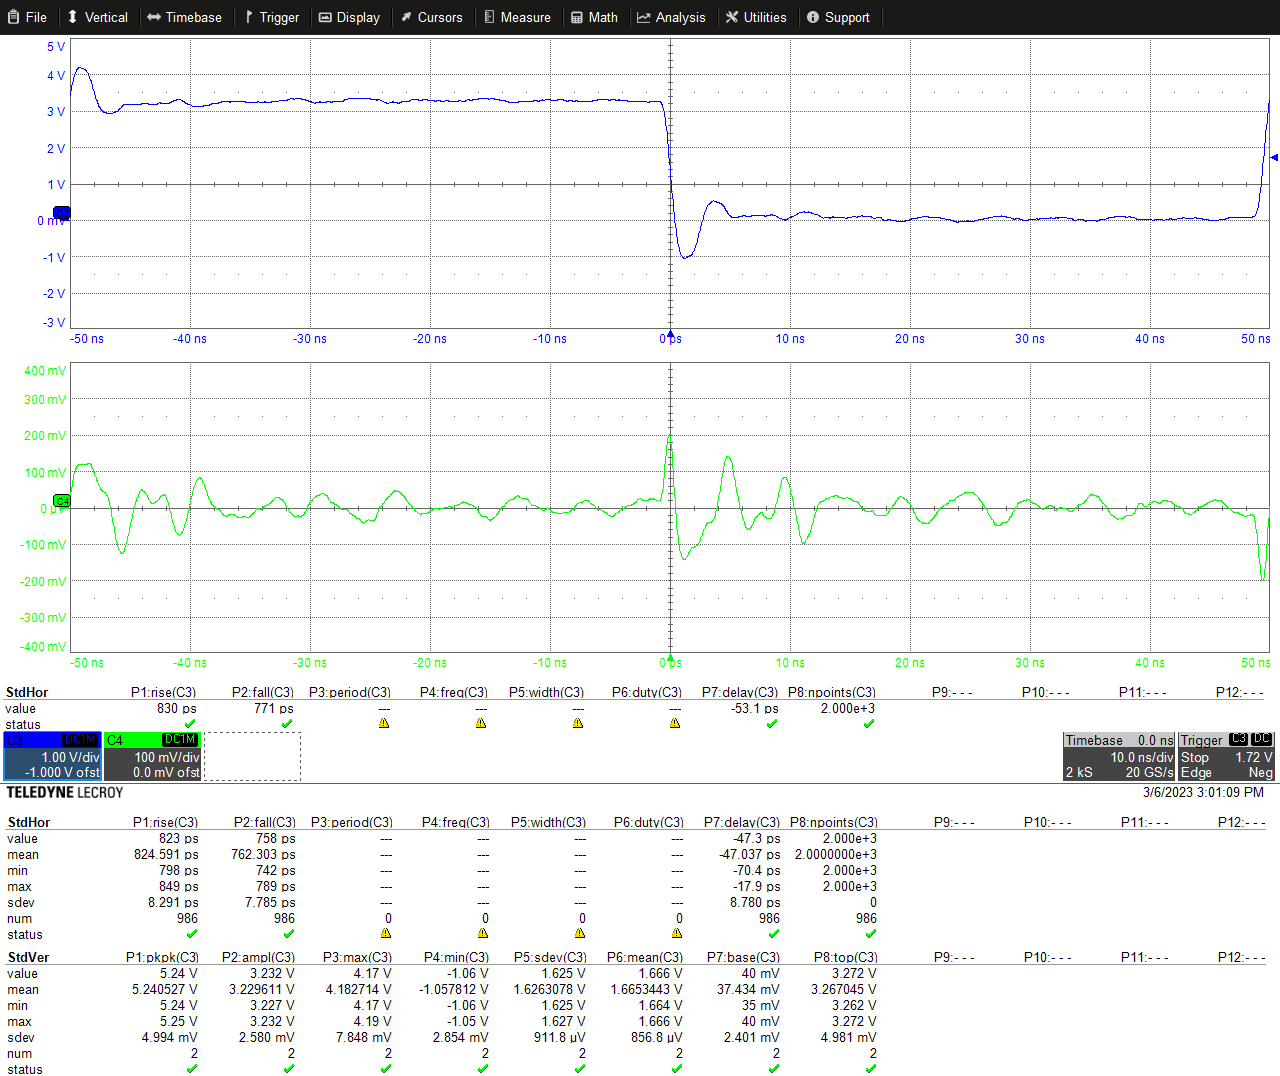
Kicad PCB projects/Test_photos/Rev_3/Xtalk_conn10_9_10MHz.png
