AndreiBertescu/FPGA_Cosmic_Radiation_Sensor/Kicad PCB projects/Rev_3.2/AICORS_PCB.kicad_sch

## KiCad design Kicad PCB projects/Rev_3.2/AICORS_PCB.kicad_sch (2026-03-10)

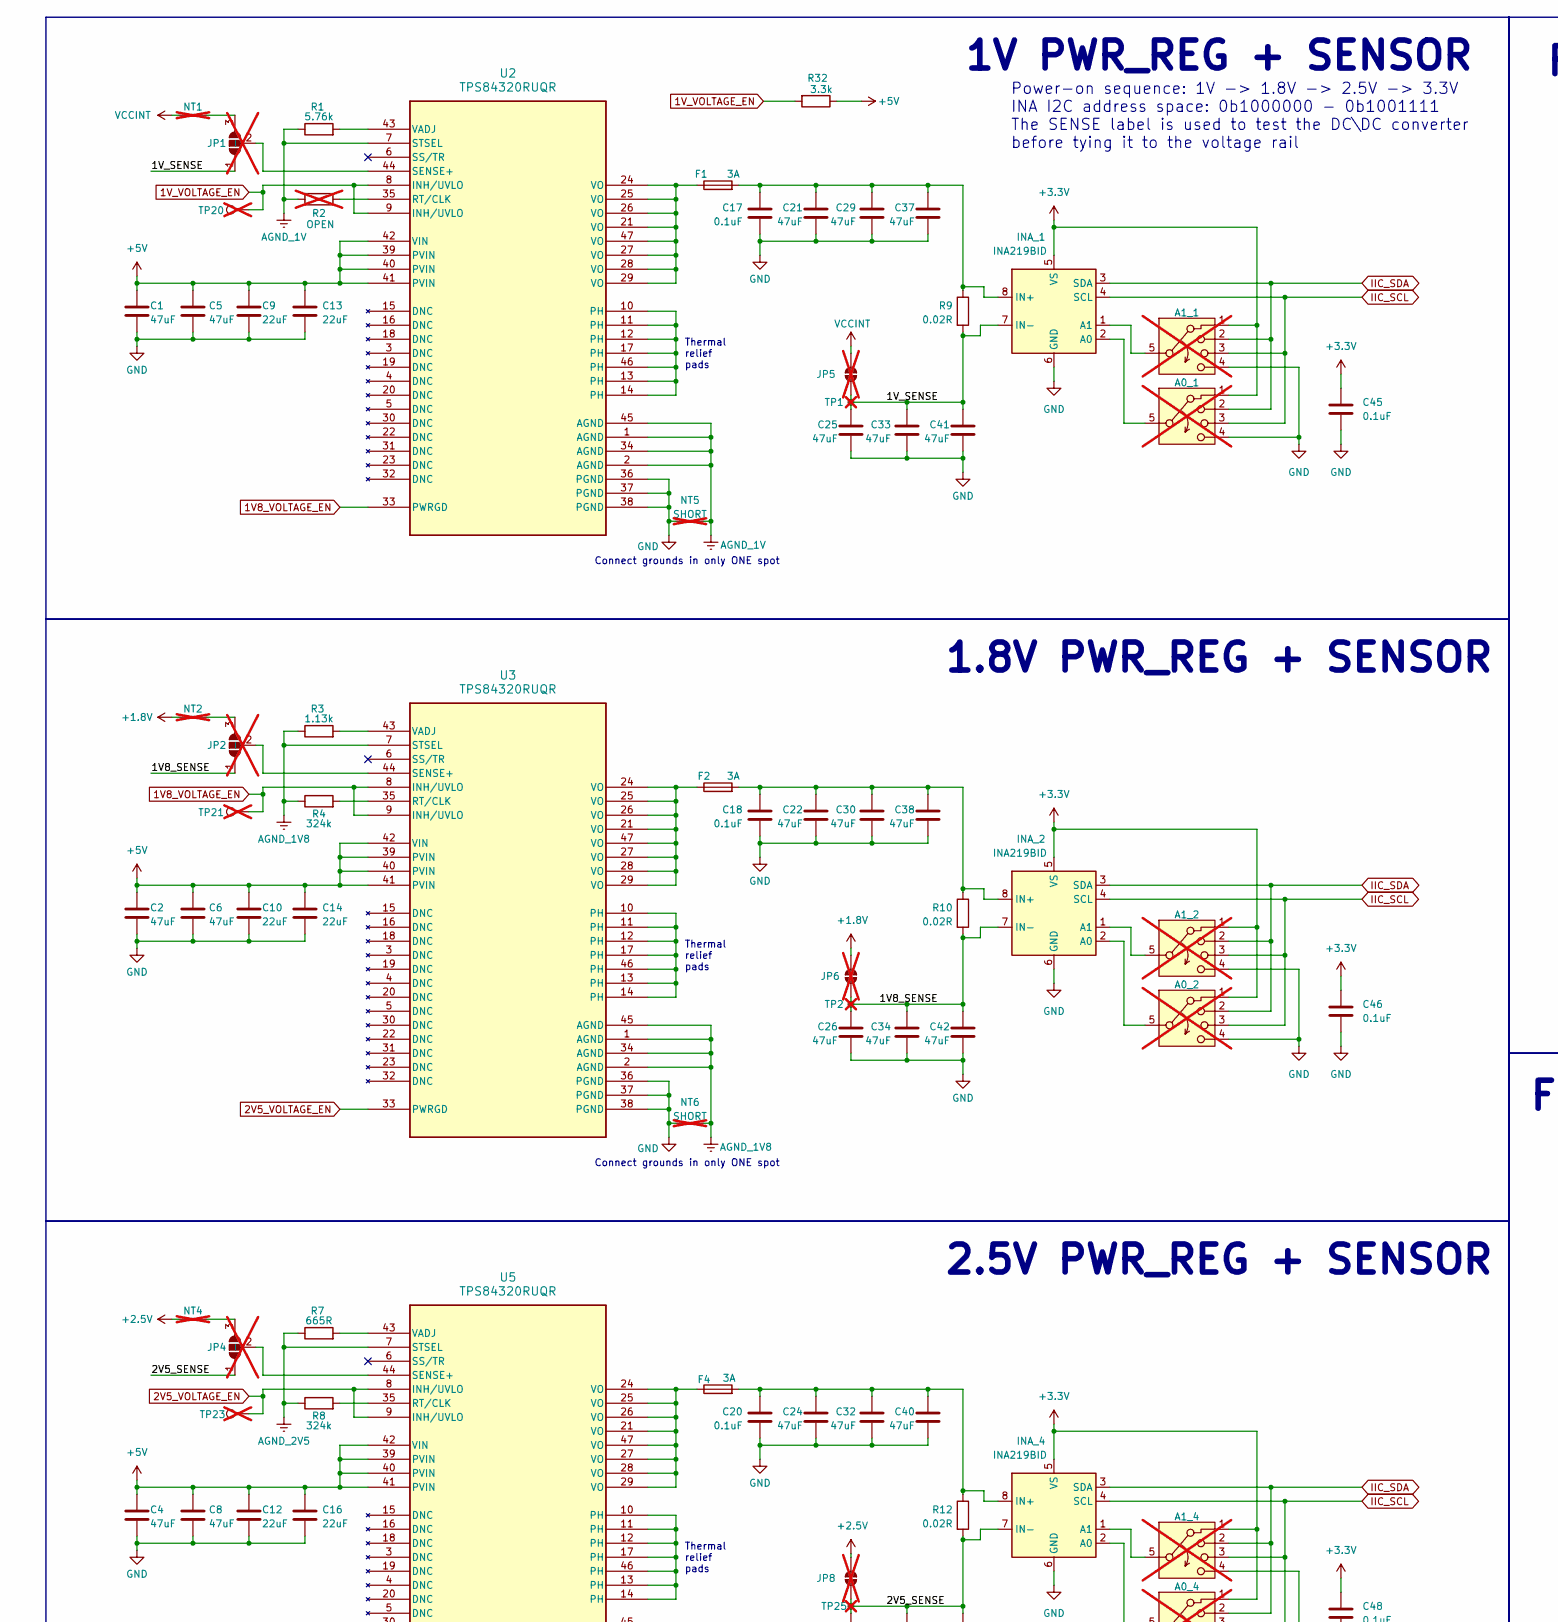
[picture p105: schematic AICORS_PCB.kicad_sch, part in row 1, column 1]

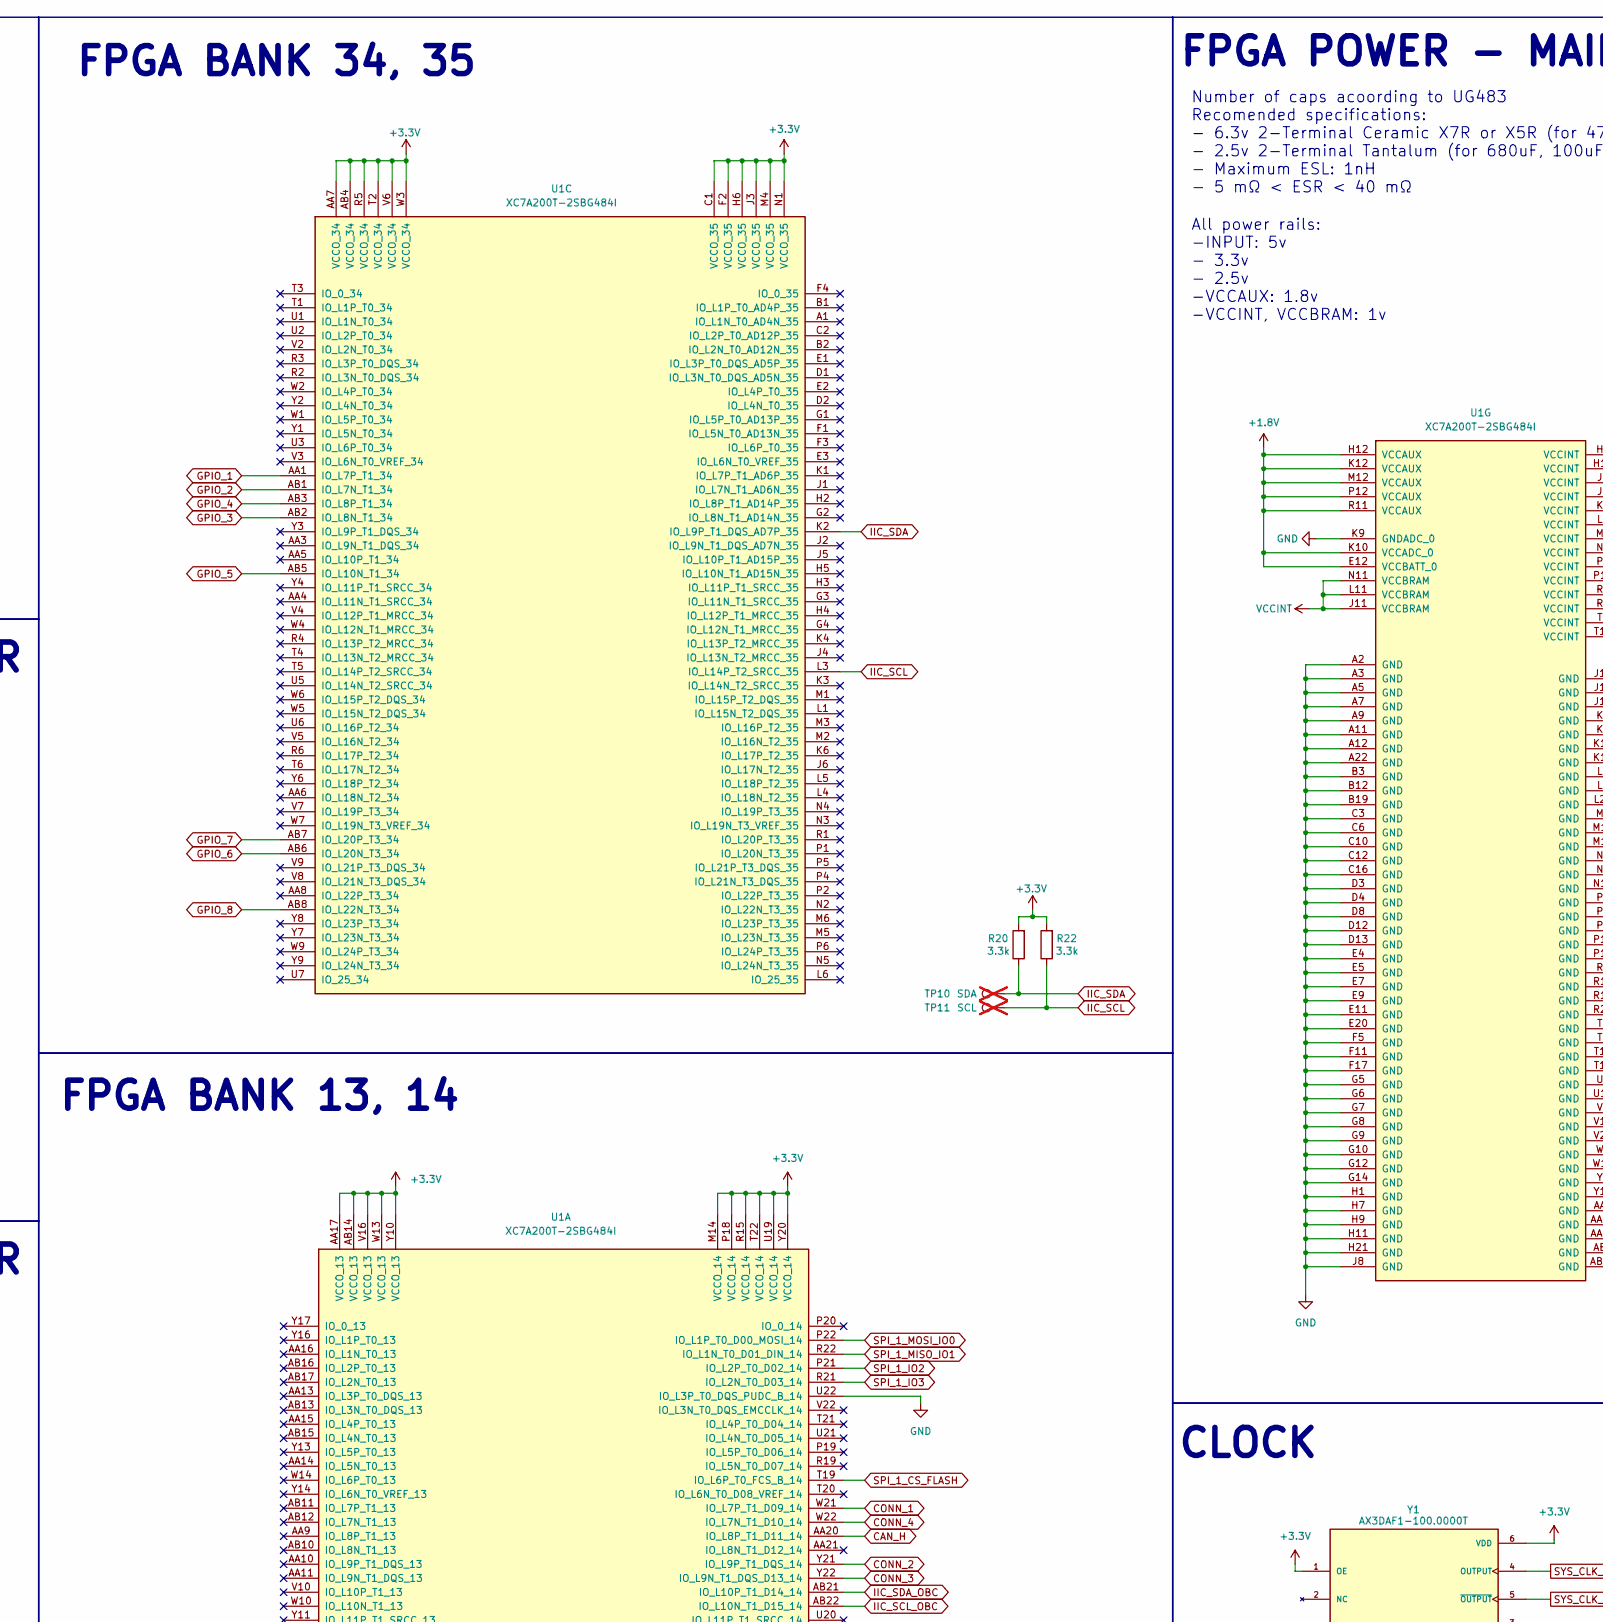
[picture p106: schematic AICORS_PCB.kicad_sch, part in row 1, column 2]

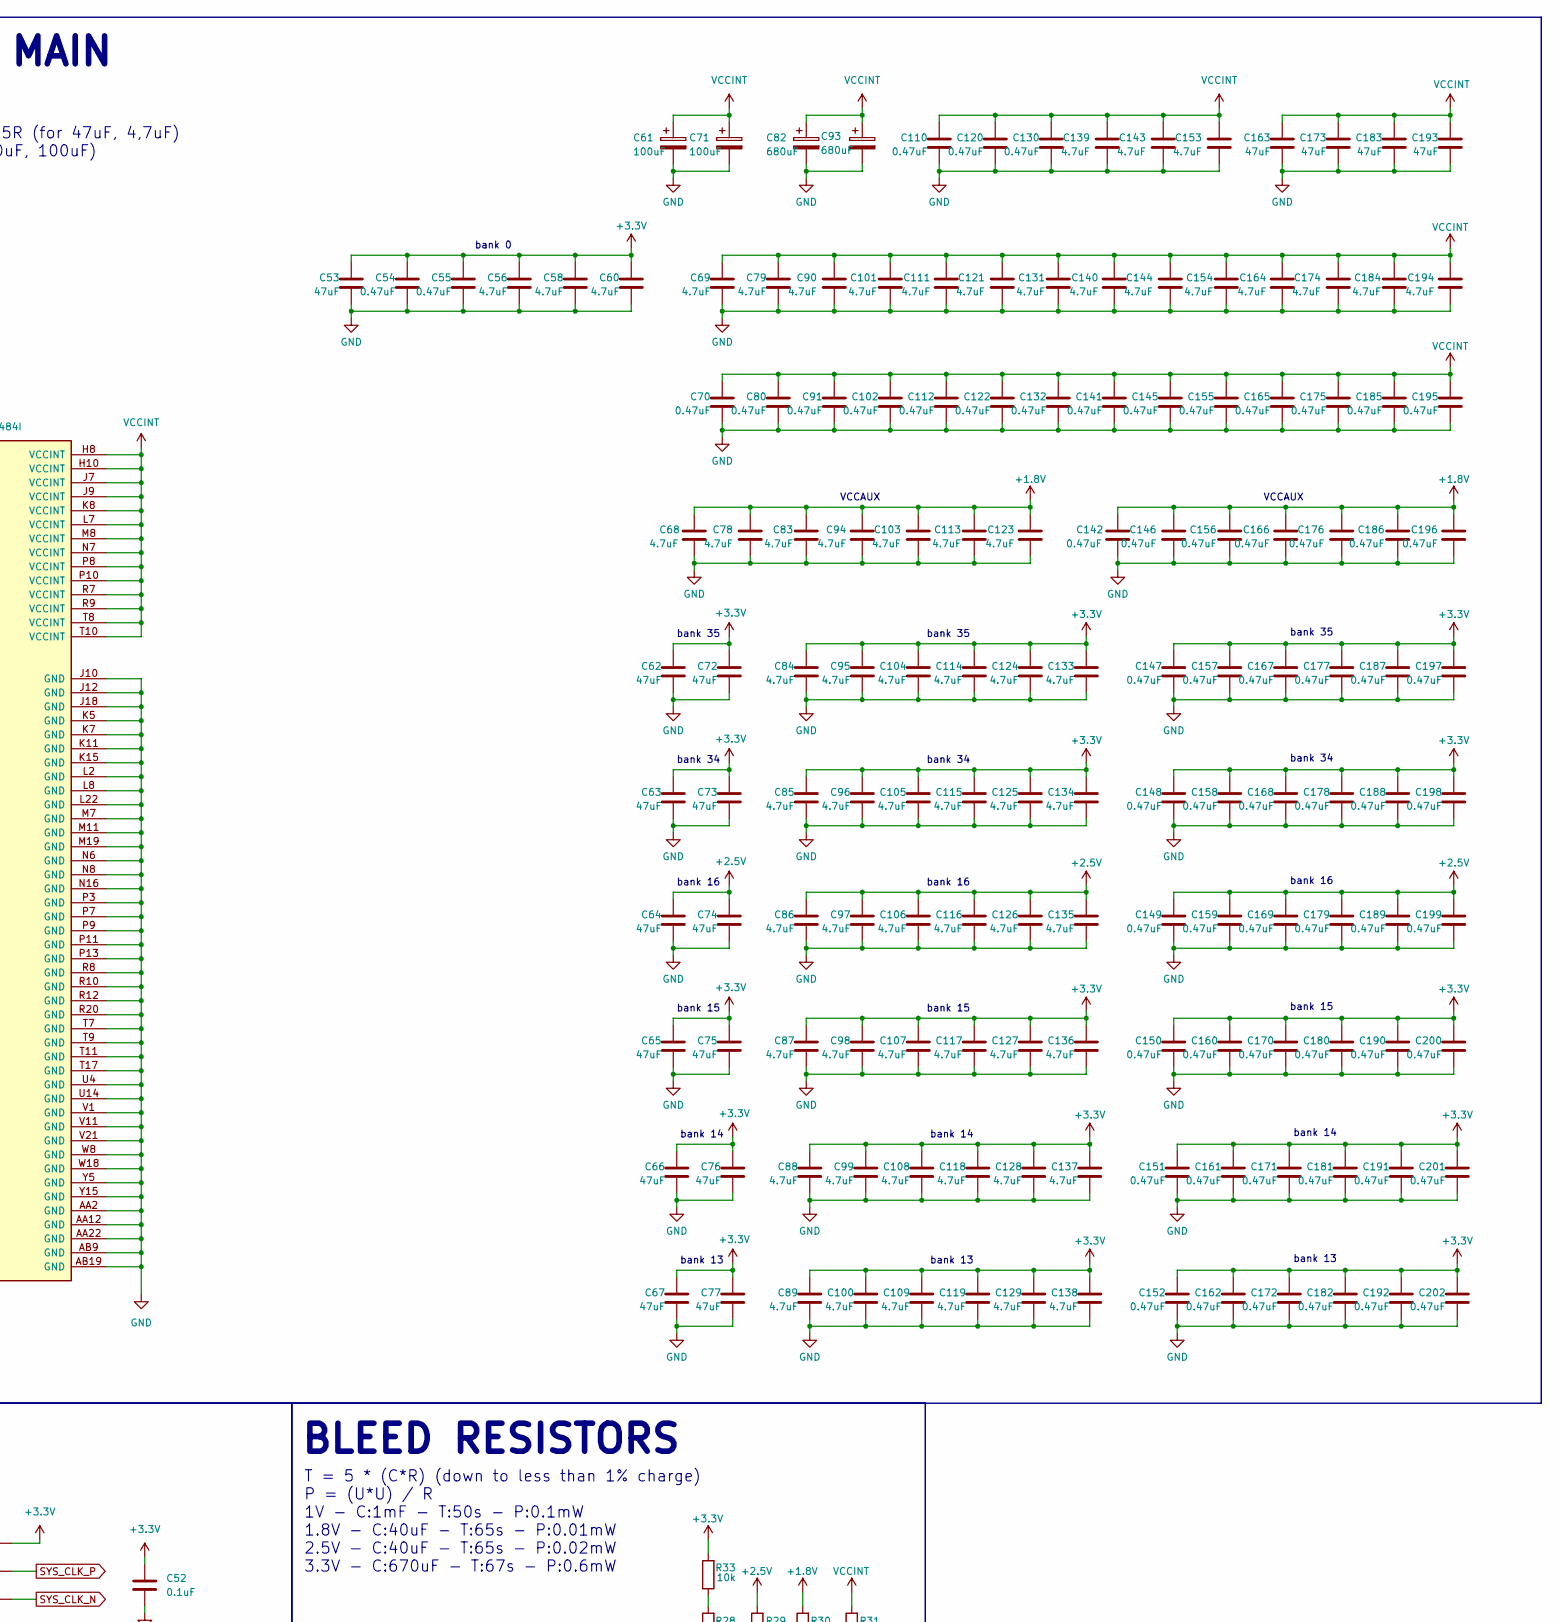
[picture p107: schematic AICORS_PCB.kicad_sch, part in row 1, column 3]

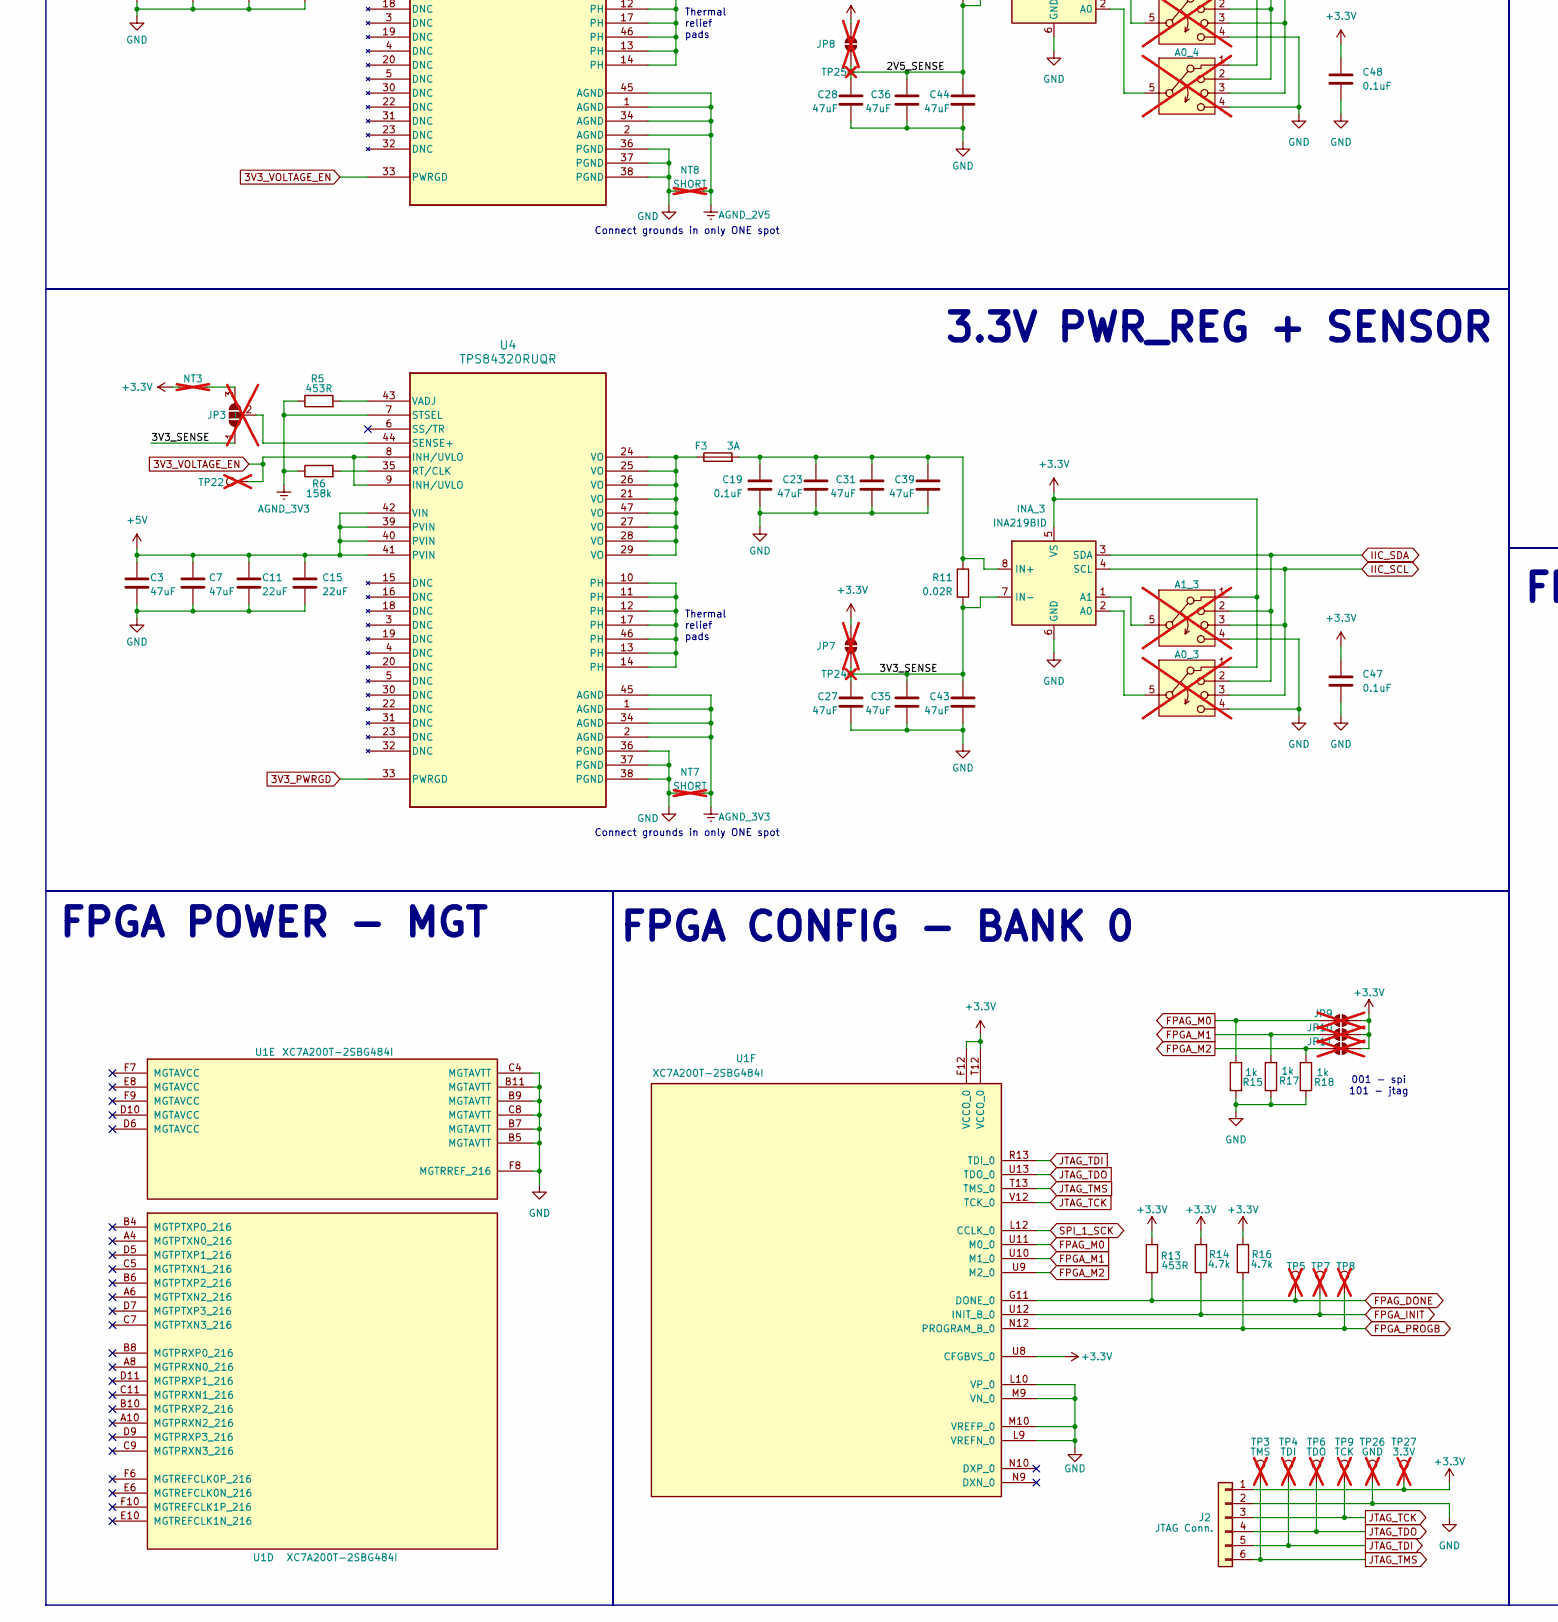
[picture p108: schematic AICORS_PCB.kicad_sch, part in row 2, column 1]

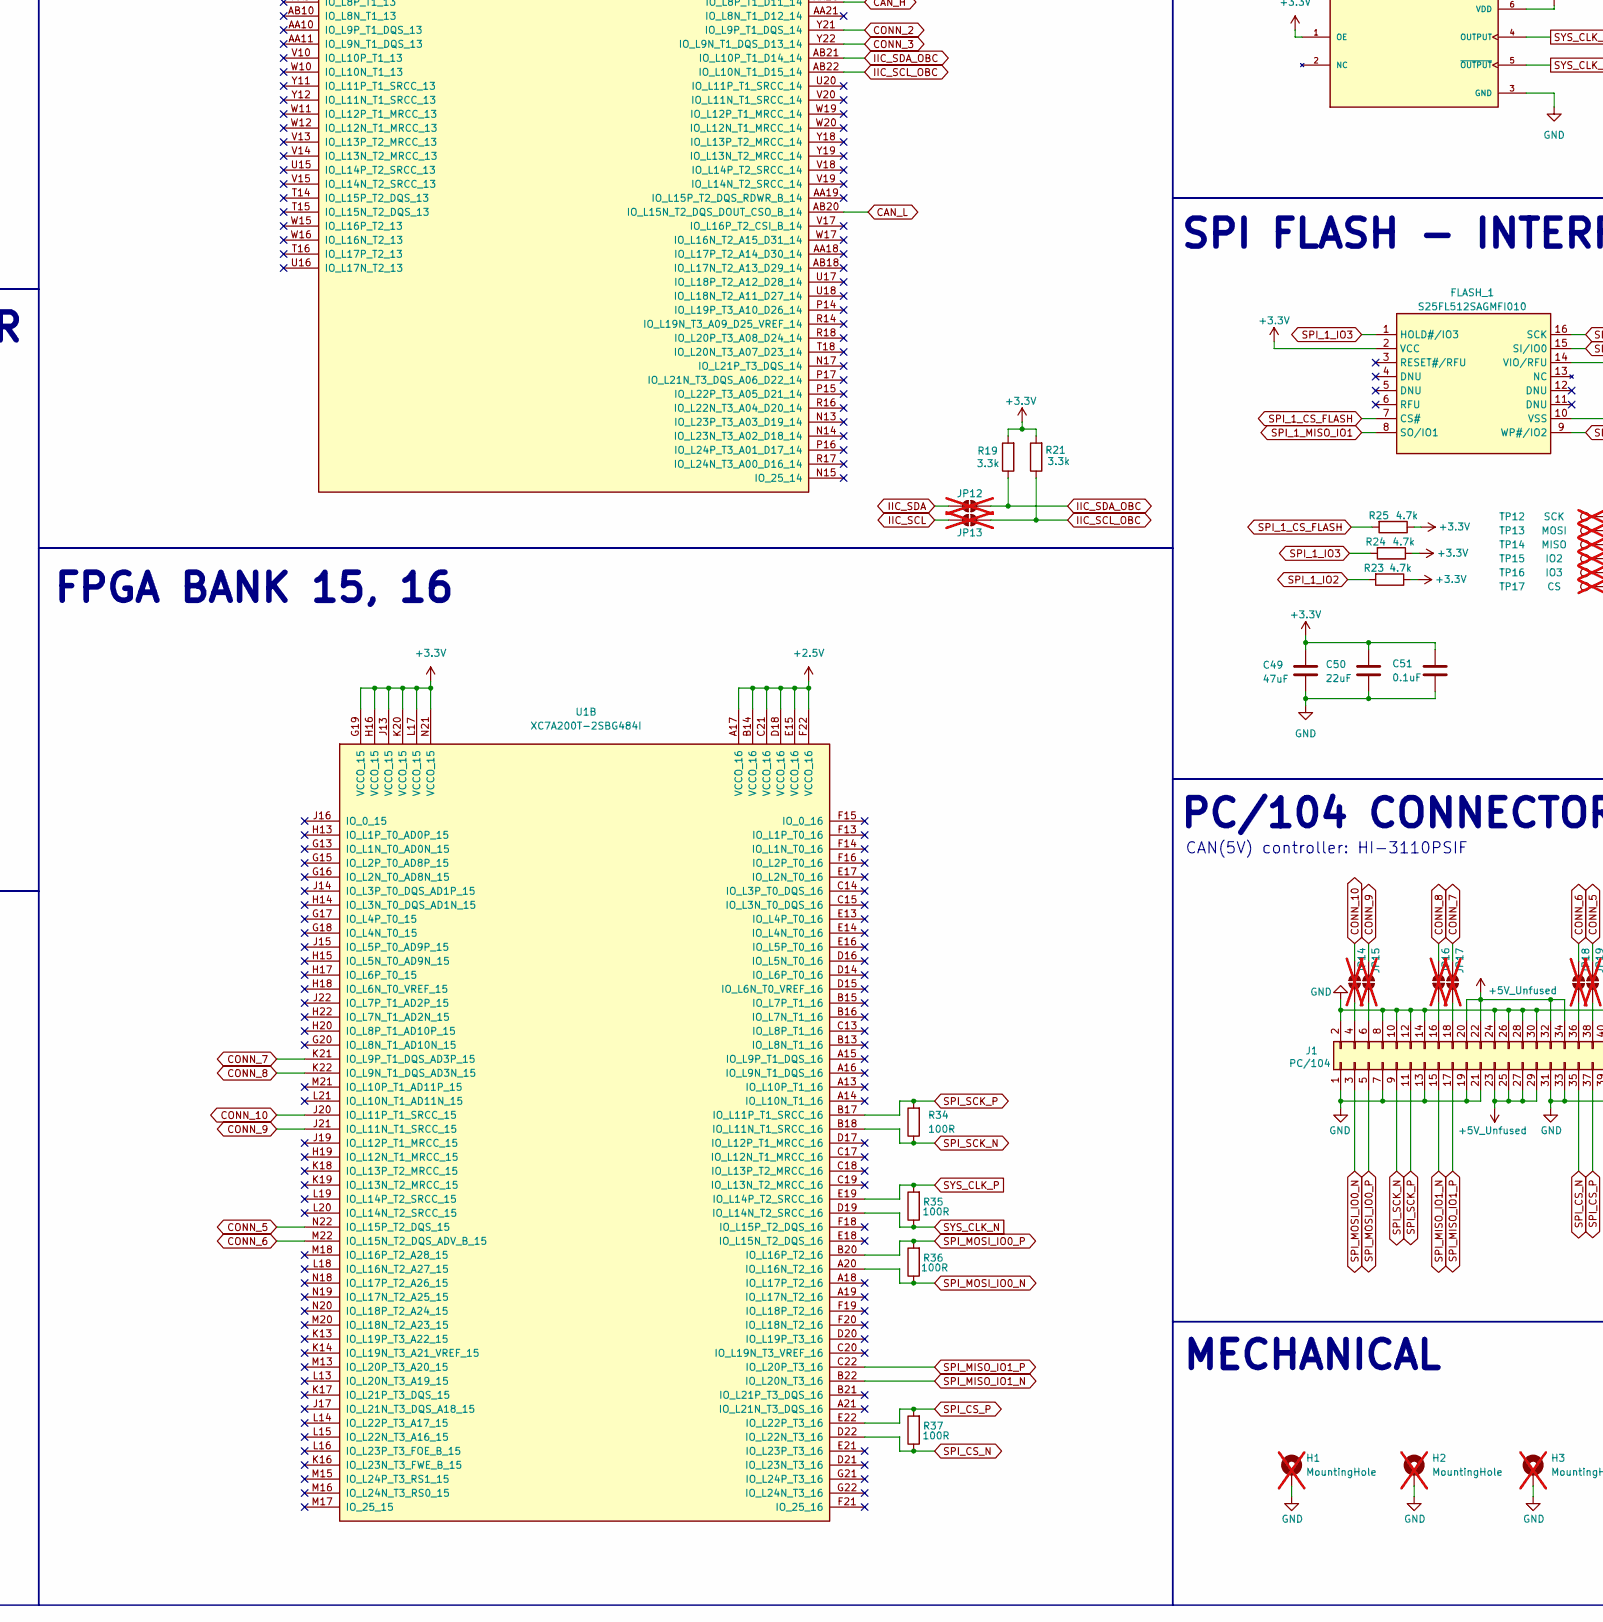
[picture p109: schematic AICORS_PCB.kicad_sch, part in row 2, column 2]

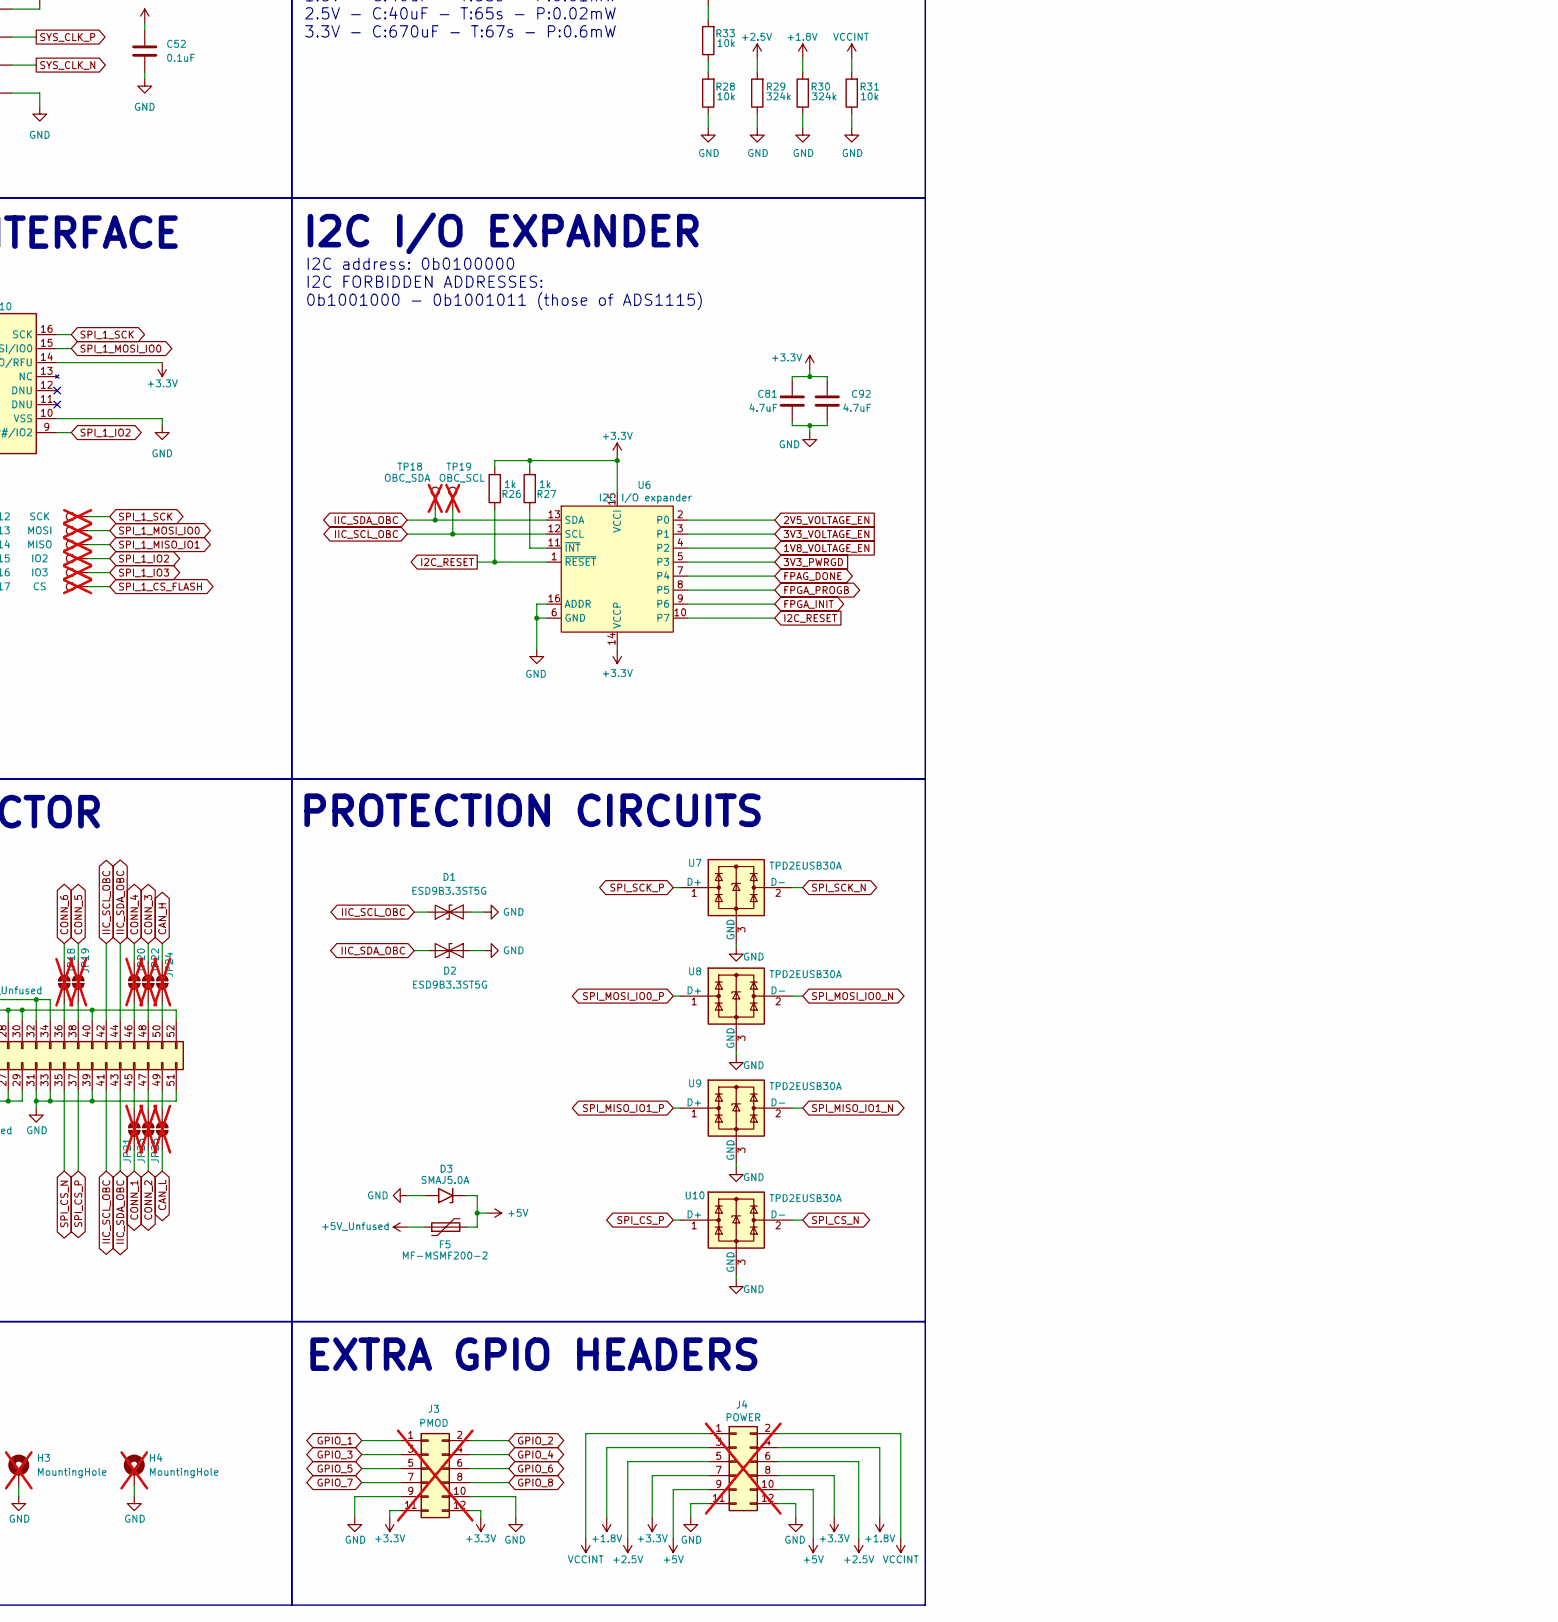
[picture p110: schematic AICORS_PCB.kicad_sch, part in row 2, column 3]

Parts:
A0_1, A0_2, A0_3, A0_4, A1_1, A1_2, A1_3, A1_4: SW_Rotary_1x4_MP; 4_Way_SolderJumper; not fitted
C1, C2, C3, C4, C5, C6, C7, C8, C21, C22, C23, C24, C25, C26, C27, C28, C29, C30, C31, C32, C33, C34, C35, C36, C37, C38, C39, C40, C41, C42, C43, C44, C49, C53, C62, C63, C64, C65, C66, C67, C72, C73, C74, C75, C76, C77, C163, C173, C183, C193: 47uF; C_0805_2012Metric; LCSC Part # C124129
C9, C10, C11, C12, C13, C14, C15, C16, C50: 22uF; C_0805_2012Metric; LCSC Part # C77074
C17, C18, C19, C20, C45, C46, C47, C48, C51, C52: 0.1uF; C_0402_1005Metric; LCSC Part # C71629
C54, C55, C70, C80, C91, C102, C110, C112, C120, C122, C130, C132, C141, C142, C145, C146, C147, C148, C149, C150, C151, C152, C155, C156, C157, C158, C159, C160, C161, C162, C165, C166, C167, C168, C169, C170, C171, C172, C175, C176, C177, C178, C179, C180, C181, C182, C185, C186, C187, C188, C189, C190, C191, C192, C195, C196, C197, C198, C199, C200, C201, C202: 0.47uF; C_0201_0603Metric; LCSC Part # C88915
C56, C58, C60, C68, C69, C78, C79, C81, C83, C84, C85, C86, C87, C88, C89, C90, C92, C94, C95, C96, C97, C98, C99, C100, C101, C103, C104, C105, C106, C107, C108, C109, C111, C113, C114, C115, C116, C117, C118, C119, C121, C123, C124, C125, C126, C127, C128, C129, C131, C133, C134, C135, C136, C137, C138, C139, C140, C143, C144, C153, C154, C164, C174, C184, C194: 4.7uF; C_0201_0603Metric; LCSC Part # C3863497
C61, C71: 100uF; Panasonic_D2 Tantalum Capacitor; LCSC Part # C139578
C82, C93: 680uF; Panasonic_D4 Tantalum Capacitor; LCSC Part # C79115
D1, D2: ESD9B3.3ST5G; D_SOD-923; LCSC Part # C96512
D3: SMAJ5.0A; D_SMA; LCSC Part # C83329
F1, F2, F3, F4: 3A; Fuse_1206_3216Metric; LCSC Part # C14165
F5: MF-MSMF200-2; Fuse_1812_4532Metric; LCSC Part # C210837
FLASH_1: S25FL512SAGMFI010; SOIC-16W_7.5x10.3mm_P1.27mm; LCSC Part # C269283
H1, H2, H3, H4: MountingHole; MountingHole_3.8mm_1mmPad; not fitted
INA_1, INA_2, INA_3, INA_4: INA219BID; SOIC-8_3.9x4.9mm_P1.27mm; LCSC Part # C2155799
J1: ESQ-126-39-G-D; 52-PinHeader_SlimDensity; LCSC Part # C7466599
J2: TSW-106-07-L-S; PinHeader_1x06_P2.54mm_Vertical; LCSC Part # C3328125
J3, J4: Conn_02x04_Odd_Even; PinHeader_2x06_P2.54mm_Vertical; not fitted
JP1: 1V_SNS; SolderJumper-3_P2.0mm_Open_TrianglePad1.0x1.5mm_NumberLabels; not fitted
JP2: 1V8_SNS; SolderJumper-3_P2.0mm_Open_TrianglePad1.0x1.5mm_NumberLabels; not fitted
JP3: 3V3_SNS; SolderJumper-3_P2.0mm_Open_TrianglePad1.0x1.5mm_NumberLabels; not fitted
JP4: 2V5_SNS; SolderJumper-3_P2.0mm_Open_TrianglePad1.0x1.5mm_NumberLabels; not fitted
JP5: 1V_MAIN; SolderJumper-2_P1.3mm_Open_TrianglePad1.0x1.5mm; not fitted
JP6: 1V8_MAIN; SolderJumper-2_P1.3mm_Open_TrianglePad1.0x1.5mm; not fitted
JP7: 3V3_MAIN; SolderJumper-2_P1.3mm_Open_TrianglePad1.0x1.5mm; not fitted
JP8: 2V5_MAIN; SolderJumper-2_P1.3mm_Open_TrianglePad1.0x1.5mm; not fitted
JP9: M0; SolderJumper-2_P1.3mm_Open_TrianglePad1.0x1.5mm; not fitted
JP10: M1; SolderJumper-2_P1.3mm_Open_TrianglePad1.0x1.5mm; not fitted
JP11: M2; SolderJumper-2_P1.3mm_Open_TrianglePad1.0x1.5mm; not fitted
JP12: SDA_CONN; SolderJumper-2_P1.3mm_Open_TrianglePad1.0x1.5mm; not fitted
JP13: SCL_CONN; SolderJumper-2_P1.3mm_Open_TrianglePad1.0x1.5mm; not fitted
JP14: CONN_10; SolderJumper-2_P1.3mm_Open_TrianglePad1.0x1.5mm; not fitted
JP15: CONN_9; SolderJumper-2_P1.3mm_Open_TrianglePad1.0x1.5mm; not fitted
JP16: CONN_8; SolderJumper-2_P1.3mm_Open_TrianglePad1.0x1.5mm; not fitted
JP17: CONN_7; SolderJumper-2_P1.3mm_Open_TrianglePad1.0x1.5mm; not fitted
JP18: CONN_6; SolderJumper-2_P1.3mm_Open_TrianglePad1.0x1.5mm; not fitted
JP19: CONN_5; SolderJumper-2_P1.3mm_Open_TrianglePad1.0x1.5mm; not fitted
JP20: CONN_4; SolderJumper-2_P1.3mm_Open_TrianglePad1.0x1.5mm; not fitted
JP21: CONN_1; SolderJumper-2_P1.3mm_Open_TrianglePad1.0x1.5mm; not fitted
JP22: CONN_3; SolderJumper-2_P1.3mm_Open_TrianglePad1.0x1.5mm; not fitted
JP23: CONN_2; SolderJumper-2_P1.3mm_Open_TrianglePad1.0x1.5mm; not fitted
JP24: CAN_H; SolderJumper-2_P1.3mm_Open_TrianglePad1.0x1.5mm; not fitted
JP25: CAN_L; SolderJumper-2_P1.3mm_Open_TrianglePad1.0x1.5mm; not fitted
NT1, NT2, NT3, NT4: SHORT; NetTie-2_SMD_Pad0.5mm; not fitted
NT5, NT6, NT7, NT8: SHORT; Net_tie_1mm; not fitted
R1: 5.76k; R_0805_2012Metric; LCSC Part # C204215
R2: OPEN; R_0805_2012Metric; not fitted
R3: 1.13k; R_0805_2012Metric; LCSC Part # C273876
R4, R8, R29, R30: 324k; R_0805_2012Metric; LCSC Part # C865403
R5, R13: 453R; R_0805_2012Metric; LCSC Part # C483161
R6: 158k; R_0805_2012Metric; LCSC Part # C203773
R7: 665R; R_0805_2012Metric; LCSC Part # C273828
R9, R10, R11, R12: 0.02R; R_0612_1632Metric; LCSC Part # C21261106
R14, R16, R23, R24, R25: 4.7k; R_0805_2012Metric; LCSC Part # C60816
R15, R17, R18, R26, R27: 1k; R_0805_2012Metric; LCSC Part # C95781
R19, R20, R21, R22, R32: 3.3k; R_0805_2012Metric; LCSC Part # C114531
R28, R31, R33: 10k; R_0805_2012Metric; LCSC Part # C84376
R34, R35, R36, R37: 100R; R_0805_2012Metric; LCSC Part # C105577
TP1: 1V; TestPoint_Pad_D1.0mm; not fitted
TP2: 1V8; TestPoint_Pad_D1.0mm; not fitted
TP3: TMS; TestPoint_Pad_D1.0mm; not fitted
TP4: TDI; TestPoint_Pad_D1.0mm; not fitted
TP5: DONE; TestPoint_Pad_D1.0mm; not fitted
TP6: TDO; TestPoint_Pad_D1.0mm; not fitted
TP7: INIT; TestPoint_Pad_D1.0mm; not fitted
TP8: PROG; TestPoint_Pad_D1.0mm; not fitted
TP9: TCK; TestPoint_Pad_D1.0mm; not fitted
TP10: SDA; TestPoint_Pad_D1.0mm; not fitted
TP11: SCL; TestPoint_Pad_D1.0mm; not fitted
TP12: SCK; TestPoint_Pad_D1.0mm; not fitted
TP13: MOSI; TestPoint_Pad_D1.0mm; not fitted
TP14: MISO; TestPoint_Pad_D1.0mm; not fitted
TP15: IO2; TestPoint_Pad_D1.0mm; not fitted
TP16: IO3; TestPoint_Pad_D1.0mm; not fitted
TP17: CS; TestPoint_Pad_D1.0mm; not fitted
TP18: OBC_SDA; TestPoint_Pad_D1.0mm; not fitted
TP19: OBC_SCL; TestPoint_Pad_D1.0mm; not fitted
TP20: 1V_EN; TestPoint_Pad_D1.0mm; not fitted
TP21: 1V8_EN; TestPoint_Pad_D1.0mm; not fitted
TP22: 3V3_EN; TestPoint_Pad_D1.0mm; not fitted
TP23: 2V5_EN; TestPoint_Pad_D1.0mm; not fitted
TP24: 3V3; TestPoint_Pad_D1.0mm; not fitted
TP25: 2V5; TestPoint_Pad_D1.0mm; not fitted
TP26: GND; TestPoint_Pad_D1.0mm; not fitted
TP27: 3.3V; TestPoint_Pad_D1.0mm; not fitted
U1: XC7A200T-2SBG484I; Xilinx_SBG484; LCSC Part # C1521826
U2, U3, U4, U5: TPS84320RUQR; TPS84320; LCSC Part # C181319
U6: TCA6408ARGTR; VQFN-16-1EP_3x3mm_P0.5mm_EP1.6x1.6mm_ThermalVias; LCSC Part # C181499
U7, U8, U9, U10: TPD2EUSB30A; Texas_DRT-3; LCSC Part # C94934
Y1: AX3DAF1-100.0000T; XTAL_AX3DAF1-100.0000T; PARTREV 02-08-22; LCSC Part # C2002827

Connections:
1V8_SENSE: C26.1, C34.1, C42.1, INA_2.7 (IN-), JP2.1 (A), JP6.1 (A), R10.2, TP2.1
1V8_VOLTAGE_EN: TP21.1, U2.33 (PWRGD), U3.8 (INH/UVLO), U3.9 (INH/UVLO), U6.4 (P2)
1V_SENSE: C25.1, C33.1, C41.1, INA_1.7 (IN-), JP1.1 (A), JP5.1 (A), R9.2, TP1.1
1V_VOLTAGE_EN: R32.2, TP20.1, U2.8 (INH/UVLO), U2.9 (INH/UVLO)
2V5_SENSE: C28.1, C36.1, C44.1, INA_4.7 (IN-), JP4.1 (A), JP8.1 (A), R12.2, TP25.1
2V5_VOLTAGE_EN: TP23.1, U3.33 (PWRGD), U5.8 (INH/UVLO), U5.9 (INH/UVLO), U6.2 (P0)
3V3_PWRGD: U4.33 (PWRGD), U6.5 (P3)
3V3_SENSE: C27.1, C35.1, C43.1, INA_3.7 (IN-), JP3.1 (A), JP7.1 (A), R11.2, TP24.1
3V3_VOLTAGE_EN: TP22.1, U4.8 (INH/UVLO), U4.9 (INH/UVLO), U5.33 (PWRGD), U6.3 (P1)
+1.8V: C68.1, C78.1, C83.1, C94.1, C103.1, C113.1, C123.1, C142.1, C146.1, C156.1, C166.1, C176.1, C186.1, C196.1, J4.3, J4.4, JP6.2 (B), NT2.2, R30.2, U1.E12 (VCCBATT_0), U1.H12 (VCCAUX), U1.K10 (VCCADC_0), U1.K12 (VCCAUX), U1.M12 (VCCAUX), U1.P12 (VCCAUX), U1.R11 (VCCAUX)
+2.5V: C64.1, C74.1, C86.1, C97.1, C106.1, C116.1, C126.1, C135.1, C149.1, C159.1, C169.1, C179.1, C189.1, C199.1, J4.5, J4.6, JP8.2 (B), NT4.2, R29.2, U1.A17 (VCCO_16), U1.B14 (VCCO_16), U1.C21 (VCCO_16), U1.D18 (VCCO_16), U1.E15 (VCCO_16), U1.F22 (VCCO_16)
+3.3V: A0_1.1, A0_2.1, A0_3.1, A0_4.1, A1_1.1, A1_2.1, A1_3.1, A1_4.1, C45.1, C46.1, C47.1, C48.1, C49.1, C50.1, C51.1, C52.1, C53.1, C54.1, C55.1, C56.1, C58.1, C60.1, C62.1, C63.1, C65.1, C66.1, C67.1, C72.1, C73.1, C75.1, C76.1, C77.1, C81.1, C84.1, C85.1, C87.1, C88.1, C89.1, C92.1, C95.1, C96.1, C98.1, C99.1, C100.1, C104.1, C105.1, C107.1, C108.1, C109.1, C114.1, C115.1, C117.1, C118.1, C119.1, C124.1, C125.1, C127.1, C128.1, C129.1, C133.1, C134.1, C136.1, C137.1, C138.1, C147.1, C148.1, C150.1, C151.1, C152.1, C157.1, C158.1, C160.1, C161.1, C162.1, C167.1, C168.1, C170.1, C171.1, C172.1, C177.1, C178.1, C180.1, C181.1, C182.1, C187.1, C188.1, C190.1, C191.1, C192.1, C197.1, C198.1, C200.1, C201.1, C202.1, FLASH_1.2 (VCC), FLASH_1.14 (VIO/RFU), INA_1.5 (VS), INA_2.5 (VS), INA_3.5 (VS), INA_4.5 (VS), J2.1, J3.11, J3.12, J4.7, J4.8, JP7.2 (B), JP9.2 (B), JP10.2 (B), JP11.2 (B), NT3.2, R13.1, R14.1, R16.1, R19.2, R20.2, R21.2, R22.2, R23.1, R24.1, R25.1, R26.2, R27.2, R33.2, TP27.1, U1.AA7 (VCCO_34), U1.AA17 (VCCO_13), U1.AB4 (VCCO_34), U1.AB14 (VCCO_13), U1.C1 (VCCO_35), U1.F2 (VCCO_35), U1.F12 (VCCO_0), U1.G19 (VCCO_15), U1.H6 (VCCO_35), U1.H16 (VCCO_15), U1.J3 (VCCO_35), U1.J13 (VCCO_15), U1.K20 (VCCO_15), U1.L17 (VCCO_15), U1.M4 (VCCO_35), U1.M14 (VCCO_14), U1.N1 (VCCO_35), U1.N21 (VCCO_15), U1.P18 (VCCO_14), U1.R5 (VCCO_34), U1.R15 (VCCO_14), U1.T2 (VCCO_34), U1.T12 (VCCO_0), U1.T22 (VCCO_14), U1.U8 (CFGBVS_0), U1.U19 (VCCO_14), U1.V6 (VCCO_34), U1.V16 (VCCO_13), U1.W3 (VCCO_34), U1.W13 (VCCO_13), U1.Y10 (VCCO_13), U1.Y20 (VCCO_14), U6.14 (VCCP), U6.15 (VCCI), Y1.1 (OE), Y1.6 (VDD)
+5V: C1.1, C2.1, C3.1, C4.1, C5.1, C6.1, C7.1, C8.1, C9.1, C10.1, C11.1, C12.1, C13.1, C14.1, C15.1, C16.1, D3.1 (A1), F5.2, J4.9, J4.10, R32.1, U2.39 (PVIN), U2.40 (PVIN), U2.41 (PVIN), U2.42 (VIN), U3.39 (PVIN), U3.40 (PVIN), U3.41 (PVIN), U3.42 (VIN), U4.39 (PVIN), U4.40 (PVIN), U4.41 (PVIN), U4.42 (VIN), U5.39 (PVIN), U5.40 (PVIN), U5.41 (PVIN), U5.42 (VIN)
+5V_Unfused: F5.1, J1.20, J1.22, J1.23, J1.25, J1.27, J1.29, J1.32, J1.34
AGND_1V: NT5.2, R1.1, R2.1, U2.1 (AGND), U2.2 (AGND), U2.7 (STSEL), U2.34 (AGND), U2.45 (AGND)
AGND_1V8: NT6.2, R3.1, R4.1, U3.1 (AGND), U3.2 (AGND), U3.7 (STSEL), U3.34 (AGND), U3.45 (AGND)
AGND_2V5: NT8.2, R7.1, R8.1, U5.1 (AGND), U5.2 (AGND), U5.7 (STSEL), U5.34 (AGND), U5.45 (AGND)
AGND_3V3: NT7.2, R5.1, R6.1, U4.1 (AGND), U4.2 (AGND), U4.7 (STSEL), U4.34 (AGND), U4.45 (AGND)
CAN_H: JP24.2 (B), U1.AA20 (IO_L8P_T1_D11_14)
CAN_L: JP25.2 (B), U1.AB20 (IO_L15N_T2_DQS_DOUT_CSO_B_14)
CONN_1: JP21.2 (B), U1.W21 (IO_L7P_T1_D09_14)
CONN_2: JP23.2 (B), U1.Y21 (IO_L9P_T1_DQS_14)
CONN_3: JP22.2 (B), U1.Y22 (IO_L9N_T1_DQS_D13_14)
CONN_4: JP20.2 (B), U1.W22 (IO_L7N_T1_D10_14)
CONN_5: JP19.2 (B), U1.N22 (IO_L15P_T2_DQS_15)
CONN_6: JP18.2 (B), U1.M22 (IO_L15N_T2_DQS_ADV_B_15)
CONN_7: JP17.2 (B), U1.K21 (IO_L9P_T1_DQS_AD3P_15)
CONN_8: JP16.2 (B), U1.K22 (IO_L9N_T1_DQS_AD3N_15)
CONN_9: JP15.2 (B), U1.J21 (IO_L11N_T1_SRCC_15)
CONN_10: JP14.2 (B), U1.J20 (IO_L11P_T1_SRCC_15)
FPAG_DONE: R13.2, TP5.1, U1.G11 (DONE_0), U6.7 (P4)
FPAG_M0: JP9.1 (A), R15.2, U1.U11 (M0_0)
FPGA_INIT: R14.2, TP7.1, U1.U12 (INIT_B_0), U6.9 (P6)
FPGA_M1: JP10.1 (A), R17.2, U1.U10 (M1_0)
FPGA_M2: JP11.1 (A), R18.2, U1.U9 (M2_0)
FPGA_PROGB: R16.2, TP8.1, U1.N12 (PROGRAM_B_0), U6.8 (P5)
GND: A0_1.4, A0_2.4, A0_3.4, A0_4.4, A1_1.4, A1_2.4, A1_3.4, A1_4.4, C1.2, C2.2, C3.2, C4.2, C5.2, C6.2, C7.2, C8.2, C9.2, C10.2, C11.2, C12.2, C13.2, C14.2, C15.2, C16.2, C17.2, C18.2, C19.2, C20.2, C21.2, C22.2, C23.2, C24.2, C25.2, C26.2, C27.2, C28.2, C29.2, C30.2, C31.2, C32.2, C33.2, C34.2, C35.2, C36.2, C37.2, C38.2, C39.2, C40.2, C41.2, C42.2, C43.2, C44.2, C45.2, C46.2, C47.2, C48.2, C49.2, C50.2, C51.2, C52.2, C53.2, C54.2, C55.2, C56.2, C58.2, C60.2, C61.2, C62.2, C63.2, C64.2, C65.2, C66.2, C67.2, C68.2, C69.2, C70.2, C71.2, C72.2, C73.2, C74.2, C75.2, C76.2, C77.2, C78.2, C79.2, C80.2, C81.2, C82.2, C83.2, C84.2, C85.2, C86.2, C87.2, C88.2, C89.2, C90.2, C91.2, C92.2, C93.2, C94.2, C95.2, C96.2, C97.2, C98.2, C99.2, C100.2, C101.2, C102.2, C103.2, C104.2, C105.2, C106.2, C107.2, C108.2, C109.2, C110.2, C111.2, C112.2, C113.2, C114.2, C115.2, C116.2, C117.2, C118.2, C119.2, C120.2, C121.2, C122.2, C123.2, C124.2, C125.2, C126.2, C127.2, C128.2, C129.2, C130.2, C131.2, C132.2, C133.2, C134.2, C135.2, C136.2, C137.2, C138.2, C139.2, C140.2, C141.2, C142.2, C143.2, C144.2, C145.2, C146.2, C147.2, C148.2, C149.2, C150.2, C151.2, C152.2, C153.2, C154.2, C155.2, C156.2, C157.2, C158.2, C159.2, C160.2, C161.2, C162.2, C163.2, C164.2, C165.2, C166.2, C167.2, C168.2, C169.2, C170.2, C171.2, C172.2, C173.2, C174.2, C175.2, C176.2, C177.2, C178.2, C179.2, C180.2, C181.2, C182.2, C183.2, C184.2, C185.2, C186.2, C187.2, C188.2, C189.2, C190.2, C191.2, C192.2, C193.2, C194.2, C195.2, C196.2, C197.2, C198.2, C199.2, C200.2, C201.2, C202.2, D1.2 (A2), D2.2 (A2), D3.2 (A2), FLASH_1.10 (VSS), H1.1, H2.1, H3.1, H4.1, INA_1.6 (GND), INA_2.6 (GND), INA_3.6 (GND), INA_4.6 (GND), J1.1, J1.2, J1.7, J1.8, J1.10, J1.12, J1.13, J1.14, J1.19, J1.21, J1.24, J1.26, J1.28, J1.30, J1.31, J1.33, J1.39, J1.40, J1.51, J1.52, J2.2, J3.9, J3.10, J4.11, J4.12, NT5.1, NT6.1, NT7.1, NT8.1, R15.1, R17.1, R18.1, R28.1, R29.1, R30.1, R31.1, TP26.1, U1.A2 (GND), U1.A3 (GND), U1.A5 (GND), U1.A7 (GND), U1.A9 (GND), U1.A11 (GND), U1.A12 (GND), U1.A22 (GND), U1.AA2 (GND), U1.AA12 (GND), U1.AA22 (GND), U1.AB9 (GND), U1.AB19 (GND), U1.B3 (GND), U1.B5 (MGTAVTT), U1.B7 (MGTAVTT), U1.B9 (MGTAVTT), U1.B11 (MGTAVTT), U1.B12 (GND), U1.B19 (GND), U1.C3 (GND), U1.C4 (MGTAVTT), U1.C6 (GND), U1.C8 (MGTAVTT), U1.C10 (GND), U1.C12 (GND), U1.C16 (GND), U1.D3 (GND), U1.D4 (GND), U1.D8 (GND), U1.D12 (GND), U1.D13 (GND), U1.E4 (GND), U1.E5 (GND), U1.E7 (GND), U1.E9 (GND), U1.E11 (GND), U1.E20 (GND), U1.F5 (GND), U1.F8 (MGTRREF_216), U1.F11 (GND), U1.F17 (GND), U1.G5 (GND), U1.G6 (GND), U1.G7 (GND), U1.G8 (GND), U1.G9 (GND), U1.G10 (GND), U1.G12 (GND), U1.G14 (GND), U1.H1 (GND), U1.H7 (GND), U1.H9 (GND), U1.H11 (GND), U1.H21 (GND), U1.J8 (GND), U1.J10 (GND), U1.J12 (GND), U1.J18 (GND), U1.K5 (GND), U1.K7 (GND), U1.K9 (GNDADC_0), U1.K11 (GND), U1.K15 (GND), U1.L2 (GND), U1.L8 (GND), U1.L9 (VREFN_0), U1.L10 (VP_0), U1.L22 (GND), U1.M7 (GND), U1.M9 (VN_0), U1.M10 (VREFP_0), U1.M11 (GND), U1.M19 (GND), U1.N6 (GND), U1.N8 (GND), U1.N16 (GND), U1.P3 (GND), U1.P7 (GND), U1.P9 (GND), U1.P11 (GND), U1.P13 (GND), U1.R8 (GND), U1.R10 (GND), U1.R12 (GND), U1.R20 (GND), U1.T7 (GND), U1.T9 (GND), U1.T11 (GND), U1.T17 (GND), U1.U4 (GND), U1.U14 (GND), U1.U22 (IO_L3P_T0_DQS_PUDC_B_14), U1.V1 (GND), U1.V11 (GND), U1.V21 (GND), U1.W8 (GND), U1.W18 (GND), U1.Y5 (GND), U1.Y15 (GND), U2.36 (PGND), U2.37 (PGND), U2.38 (PGND), U3.36 (PGND), U3.37 (PGND), U3.38 (PGND), U4.36 (PGND), U4.37 (PGND), U4.38 (PGND), U5.36 (PGND), U5.37 (PGND), U5.38 (PGND), U6.6 (GND), U6.16 (ADDR), U6.17 (GND), U7.3 (GND), U8.3 (GND), U9.3 (GND), U10.3 (GND), Y1.3 (GND)
GPIO_1: J3.1, U1.AA1 (IO_L7P_T1_34)
GPIO_2: J3.2, U1.AB1 (IO_L7N_T1_34)
GPIO_3: J3.3, U1.AB2 (IO_L8N_T1_34)
GPIO_4: J3.4, U1.AB3 (IO_L8P_T1_34)
GPIO_5: J3.5, U1.AB5 (IO_L10N_T1_34)
GPIO_6: J3.6, U1.AB6 (IO_L20N_T3_34)
GPIO_7: J3.7, U1.AB7 (IO_L20P_T3_34)
GPIO_8: J3.8, U1.AB8 (IO_L22N_T3_34)
I2C_RESET: R26.1, U6.1 (~RESET), U6.10 (P7)
IIC_SCL: A0_1.3, A0_2.3, A0_3.3, A0_4.3, A1_1.3, A1_2.3, A1_3.3, A1_4.3, INA_1.4 (SCL), INA_2.4 (SCL), INA_3.4 (SCL), INA_4.4 (SCL), JP13.2 (B), R22.1, TP11.1, U1.L3 (IO_L14P_T2_SRCC_35)
IIC_SCL_OBC: D1.1 (A1), J1.41, J1.42, JP13.1 (A), R21.1, TP19.1, U1.AB22 (IO_L10N_T1_D15_14), U6.12 (SCL)
IIC_SDA: A0_1.2, A0_2.2, A0_3.2, A0_4.2, A1_1.2, A1_2.2, A1_3.2, A1_4.2, INA_1.3 (SDA), INA_2.3 (SDA), INA_3.3 (SDA), INA_4.3 (SDA), JP12.2 (B), R20.1, TP10.1, U1.K2 (IO_L9P_T1_DQS_AD7P_35)
IIC_SDA_OBC: D2.1 (A1), J1.43, J1.44, JP12.1 (A), R19.1, TP18.1, U1.AB21 (IO_L10P_T1_D14_14), U6.13 (SDA)
JTAG_TCK: J2.3, TP9.1, U1.V12 (TCK_0)
JTAG_TDI: J2.5, TP4.1, U1.R13 (TDI_0)
JTAG_TDO: J2.4, TP6.1, U1.U13 (TDO_0)
JTAG_TMS: J2.6, TP3.1, U1.T13 (TMS_0)
unnamed: A0_1.5, INA_1.2 (A0)
unnamed: A0_2.5, INA_2.2 (A0)
unnamed: A0_3.5, INA_3.2 (A0)
unnamed: A0_4.5, INA_4.2 (A0)
unnamed: A1_1.5, INA_1.1 (A1)
unnamed: A1_2.5, INA_2.1 (A1)
unnamed: A1_3.5, INA_3.1 (A1)
unnamed: A1_4.5, INA_4.1 (A1)
unnamed: C17.1, C21.1, C29.1, C37.1, F1.2, INA_1.8 (IN+), R9.1
unnamed: C18.1, C22.1, C30.1, C38.1, F2.2, INA_2.8 (IN+), R10.1
unnamed: C19.1, C23.1, C31.1, C39.1, F3.2, INA_3.8 (IN+), R11.1
unnamed: C20.1, C24.1, C32.1, C40.1, F4.2, INA_4.8 (IN+), R12.1
unnamed: F1.1, U2.21 (VO), U2.24 (VO), U2.25 (VO), U2.26 (VO), U2.27 (VO), U2.28 (VO), U2.29 (VO), U2.47 (VO)
unnamed: F2.1, U3.21 (VO), U3.24 (VO), U3.25 (VO), U3.26 (VO), U3.27 (VO), U3.28 (VO), U3.29 (VO), U3.47 (VO)
unnamed: F3.1, U4.21 (VO), U4.24 (VO), U4.25 (VO), U4.26 (VO), U4.27 (VO), U4.28 (VO), U4.29 (VO), U4.47 (VO)
unnamed: F4.1, U5.21 (VO), U5.24 (VO), U5.25 (VO), U5.26 (VO), U5.27 (VO), U5.28 (VO), U5.29 (VO), U5.47 (VO)
unnamed: J1.4, JP14.1 (A)
unnamed: J1.6, JP15.1 (A)
unnamed: J1.16, JP16.1 (A)
unnamed: J1.18, JP17.1 (A)
unnamed: J1.36, JP18.1 (A)
unnamed: J1.38, JP19.1 (A)
unnamed: J1.45, JP21.1 (A)
unnamed: J1.46, JP20.1 (A)
unnamed: J1.47, JP23.1 (A)
unnamed: J1.48, JP22.1 (A)
unnamed: J1.49, JP25.1 (A)
unnamed: J1.50, JP24.1 (A)
unnamed: JP1.2 (C), U2.44 (SENSE+)
unnamed: JP1.3 (B), NT1.1
unnamed: JP2.2 (C), U3.44 (SENSE+)
unnamed: JP2.3 (B), NT2.1
unnamed: JP3.2 (C), U4.44 (SENSE+)
unnamed: JP3.3 (B), NT3.1
unnamed: JP4.2 (C), U5.44 (SENSE+)
unnamed: JP4.3 (B), NT4.1
unnamed: R1.2, U2.43 (VADJ)
unnamed: R2.2, U2.35 (RT/CLK)
unnamed: R3.2, U3.43 (VADJ)
unnamed: R4.2, U3.35 (RT/CLK)
unnamed: R5.2, U4.43 (VADJ)
unnamed: R6.2, U4.35 (RT/CLK)
unnamed: R7.2, U5.43 (VADJ)
unnamed: R8.2, U5.35 (RT/CLK)
unnamed: R27.1, U6.11 (~INT)
unnamed: R28.2, R33.1
unnamed: U2.10 (PH), U2.11 (PH), U2.12 (PH), U2.13 (PH), U2.14 (PH), U2.17 (PH), U2.46 (PH)
unnamed: U3.10 (PH), U3.11 (PH), U3.12 (PH), U3.13 (PH), U3.14 (PH), U3.17 (PH), U3.46 (PH)
unnamed: U4.10 (PH), U4.11 (PH), U4.12 (PH), U4.13 (PH), U4.14 (PH), U4.17 (PH), U4.46 (PH)
unnamed: U5.10 (PH), U5.11 (PH), U5.12 (PH), U5.13 (PH), U5.14 (PH), U5.17 (PH), U5.46 (PH)
SPI_1_CS_FLASH: FLASH_1.7 (CS#), R25.2, TP17.1, U1.T19 (IO_L6P_T0_FCS_B_14)
SPI_1_IO2: FLASH_1.9 (WP#/IO2), R23.2, TP15.1, U1.P21 (IO_L2P_T0_D02_14)
SPI_1_IO3: FLASH_1.1 (HOLD#/IO3), R24.2, TP16.1, U1.R21 (IO_L2N_T0_D03_14)
SPI_1_MISO_IO1: FLASH_1.8 (SO/IO1), TP14.1, U1.R22 (IO_L1N_T0_D01_DIN_14)
SPI_1_MOSI_IO0: FLASH_1.15 (SI/IO0), TP13.1, U1.P22 (IO_L1P_T0_D00_MOSI_14)
SPI_1_SCK: FLASH_1.16 (SCK), TP12.1, U1.L12 (CCLK_0)
SPI_CS_N: J1.35, R37.1, U1.D22 (IO_L22N_T3_16), U10.2 (D-)
SPI_CS_P: J1.37, R37.2, U1.E22 (IO_L22P_T3_16), U10.1 (D+)
SPI_MISO_IO1_N: J1.15, U1.B22 (IO_L20N_T3_16), U9.2 (D-)
SPI_MISO_IO1_P: J1.17, U1.C22 (IO_L20P_T3_16), U9.1 (D+)
SPI_MOSI_IO0_N: J1.3, R36.1, U1.A20 (IO_L16N_T2_16), U8.2 (D-)
SPI_MOSI_IO0_P: J1.5, R36.2, U1.B20 (IO_L16P_T2_16), U8.1 (D+)
SPI_SCK_N: J1.9, R34.1, U1.B18 (IO_L11N_T1_SRCC_16), U7.2 (D-)
SPI_SCK_P: J1.11, R34.2, U1.B17 (IO_L11P_T1_SRCC_16), U7.1 (D+)
SYS_CLK_N: R35.1, U1.D19 (IO_L14N_T2_SRCC_16), Y1.5 (~OUTPUT)
SYS_CLK_P: R35.2, U1.E19 (IO_L14P_T2_SRCC_16), Y1.4 (OUTPUT)
VCCINT: C61.1, C69.1, C70.1, C71.1, C79.1, C80.1, C82.1, C90.1, C91.1, C93.1, C101.1, C102.1, C110.1, C111.1, C112.1, C120.1, C121.1, C122.1, C130.1, C131.1, C132.1, C139.1, C140.1, C141.1, C143.1, C144.1, C145.1, C153.1, C154.1, C155.1, C163.1, C164.1, C165.1, C173.1, C174.1, C175.1, C183.1, C184.1, C185.1, C193.1, C194.1, C195.1, J4.1, J4.2, JP5.2 (B), NT1.2, R31.2, U1.H8 (VCCINT), U1.H10 (VCCINT), U1.J7 (VCCINT), U1.J9 (VCCINT), U1.J11 (VCCBRAM), U1.K8 (VCCINT), U1.L7 (VCCINT), U1.L11 (VCCBRAM), U1.M8 (VCCINT), U1.N7 (VCCINT), U1.N11 (VCCBRAM), U1.P8 (VCCINT), U1.P10 (VCCINT), U1.R7 (VCCINT), U1.R9 (VCCINT), U1.T8 (VCCINT), U1.T10 (VCCINT)

Notes on the sheet:
All power rails: -INPUT: 5v - 3.3v - 2.5v -VCCAUX: 1.8v -VCCINT, VCCBRAM: 1v
FPGA POWER - MAIN
bank 16
Thermal relief pads
bank 13
FPGA POWER - MGT
bank 14
FPGA CONFIG - BANK 0
PROTECTION CIRCUITS
2.5V PWR_REG + SENSOR
CAN(5V) controller: HI-3110PSIF
T = 5 * (C*R) (down to less than 1% charge) P = (U*U) / R 1V - C:1mF - T:50s - P:0.1mW 1.8V - C:40uF - T:65s - P:0.01mW 2.5V - C:40uF - T:65s - P:0.02mW 3.3V - C:670uF - T:67s - P:0.6mW
FPGA BANK 15, 16
1V PWR_REG + SENSOR
Connect grounds in only ONE spot
bank 15
Number of caps acoording to UG483 Recomended specifications: - 6.3v 2-Terminal Ceramic X7R or X5R (for 47uF, 4,7uF) - 2.5v 2-Terminal Tantalum (for 680uF, 100uF) - Maximum ESL: 1nH - 5 mΩ < ESR < 40 mΩ
FPGA BANK 13, 14
bank 0
VCCAUX
bank 35
MECHANICAL
bank 34
BLEED RESISTORS
SPI FLASH - INTERFACE
PC/104 CONNECTOR
CLOCK
I2C I/O EXPANDER
EXTRA GPIO HEADERS
1.8V PWR_REG + SENSOR
Power-on sequence: 1V -> 1.8V -> 2.5V -> 3.3V INA I2C address space: 0b1000000 - 0b1001111 The SENSE label is used to test the DC\DC converter before tying it to the voltage rail
FPGA BANK 34, 35
3.3V PWR_REG + SENSOR
001 - spi 101 - jtag
I2C address: 0b0100000 I2C FORBIDDEN ADDRESSES: 0b1001000 - 0b1001011 (those of ADS1115)
