AndreiBertescu/FPGA_Cosmic_Radiation_Sensor/Verilog parts test projects/Interface_XADC/xadc_wiz_0_ex.gen/sources_1/ip/vio_0/synth/vio_0.v

// (c) Copyright 2023 Advanced Micro Devices, Inc. All rights reserved.
//
// This file contains confidential and proprietary information
// of AMD, Inc. and is protected under U.S. and
// international copyright and other intellectual property
// laws.
//
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
// CRITICAL APPLICATIONS
// AMD products are not designed or intended to be fail-
// safe, or for use in any application requiring fail-safe
// performance, such as life-support or safety devices or
// systems, Class III medical devices, nuclear facilities,
// applications related to the deployment of airbags, or any
// other applications that could lead to death, personal
// injury, or severe property or environmental damage
// (individually and collectively, "Critical
// Applications"). Customer assumes the sole risk and
// liability of any use of AMD products in Critical
// Applications, subject only to applicable laws and
// regulations governing limitations on product liability.
//
// THIS COPYRIGHT NOTICE AND DISCLAIMER MUST BE RETAINED AS
// PART OF THIS FILE AT ALL TIMES.
//
// DO NOT MODIFY THIS FILE.

(* X_CORE_INFO = "vio,Vivado 2024.1" *)
(* CHECK_LICENSE_TYPE = "vio_0,vio,{}" *)
(* CORE_GENERATION_INFO = "vio_0,vio,{x_ipProduct=Vivado 2024.1,x_ipVendor=xilinx.com,x_ipLibrary=ip,x_ipName=vio,x_ipVersion=3.0,x_ipLanguage=VERILOG,C_XLNX_HW_PROBE_INFO=DEFAULT,C_XDEVICEFAMILY=artix7,C_CORE_TYPE=2,C_CORE_INFO1=0,C_CORE_INFO2=0,C_NUM_PROBE_IN=8,C_NUM_PROBE_OUT=0,C_EN_PROBE_IN_ACTIVITY=1,C_MAJOR_VERSION=2013,C_MINOR_VERSION=1,C_BUILD_REVISION=0,C_CORE_MAJOR_VER=2,C_CORE_MINOR_VER=0,C_CORE_MINOR_ALPHA_VER=97,C_XSDB_SLAVE_TYPE=33,C_NEXT_SLAVE=0,C_CSE_DRV_VER=1,C_USE_TEST_REG=1,C_PIPE_IFACE=0,C_PROBE_IN0_WIDTH=12,C_PROBE_IN1_WIDTH=12,C_PROBE_IN2_WIDTH=12,C_PROBE_IN3_WIDTH=12,C_PROBE_IN4_WIDTH=1,C_PROBE_IN5_WIDTH=1,C_PROBE_IN6_WIDTH=1,C_PROBE_IN7_WIDTH=1,C_PROBE_IN8_WIDTH=1,C_PROBE_IN9_WIDTH=1,C_PROBE_IN10_WIDTH=1,C_PROBE_IN11_WIDTH=1,C_PROBE_IN12_WIDTH=1,C_PROBE_IN13_WIDTH=1,C_PROBE_IN14_WIDTH=1,C_PROBE_IN15_WIDTH=1,C_PROBE_IN16_WIDTH=1,C_PROBE_IN17_WIDTH=1,C_PROBE_IN18_WIDTH=1,C_PROBE_IN19_WIDTH=1,C_PROBE_IN20_WIDTH=1,C_PROBE_IN21_WIDTH=1,C_PROBE_IN22_WIDTH=1,C_PROBE_IN23_WIDTH=1,C_PROBE_IN24_WIDTH=1,C_PROBE_IN25_WIDTH=1,C_PROBE_IN26_WIDTH=1,C_PROBE_IN27_WIDTH=1,C_PROBE_IN28_WIDTH=1,C_PROBE_IN29_WIDTH=1,C_PROBE_IN30_WIDTH=1,C_PROBE_IN31_WIDTH=1,C_PROBE_IN32_WIDTH=1,C_PROBE_IN33_WIDTH=1,C_PROBE_IN34_WIDTH=1,C_PROBE_IN35_WIDTH=1,C_PROBE_IN36_WIDTH=1,C_PROBE_IN37_WIDTH=1,C_PROBE_IN38_WIDTH=1,C_PROBE_IN39_WIDTH=1,C_PROBE_IN40_WIDTH=1,C_PROBE_IN41_WIDTH=1,C_PROBE_IN42_WIDTH=1,C_PROBE_IN43_WIDTH=1,C_PROBE_IN44_WIDTH=1,C_PROBE_IN45_WIDTH=1,C_PROBE_IN46_WIDTH=1,C_PROBE_IN47_WIDTH=1,C_PROBE_IN48_WIDTH=1,C_PROBE_IN49_WIDTH=1,C_PROBE_IN50_WIDTH=1,C_PROBE_IN51_WIDTH=1,C_PROBE_IN52_WIDTH=1,C_PROBE_IN53_WIDTH=1,C_PROBE_IN54_WIDTH=1,C_PROBE_IN55_WIDTH=1,C_PROBE_IN56_WIDTH=1,C_PROBE_IN57_WIDTH=1,C_PROBE_IN58_WIDTH=1,C_PROBE_IN59_WIDTH=1,C_PROBE_IN60_WIDTH=1,C_PROBE_IN61_WIDTH=1,C_PROBE_IN62_WIDTH=1,C_PROBE_IN63_WIDTH=1,C_PROBE_IN64_WIDTH=1,C_PROBE_IN65_WIDTH=1,C_PROBE_IN66_WIDTH=1,C_PROBE_IN67_WIDTH=1,C_PROBE_IN68_WIDTH=1,C_PROBE_IN69_WIDTH=1,C_PROBE_IN70_WIDTH=1,C_PROBE_IN71_WIDTH=1,C_PROBE_IN72_WIDTH=1,\
C_PROBE_IN73_WIDTH=1,C_PROBE_IN74_WIDTH=1,C_PROBE_IN75_WIDTH=1,C_PROBE_IN76_WIDTH=1,C_PROBE_IN77_WIDTH=1,C_PROBE_IN78_WIDTH=1,C_PROBE_IN79_WIDTH=1,C_PROBE_IN80_WIDTH=1,C_PROBE_IN81_WIDTH=1,C_PROBE_IN82_WIDTH=1,C_PROBE_IN83_WIDTH=1,C_PROBE_IN84_WIDTH=1,C_PROBE_IN85_WIDTH=1,C_PROBE_IN86_WIDTH=1,C_PROBE_IN87_WIDTH=1,C_PROBE_IN88_WIDTH=1,C_PROBE_IN89_WIDTH=1,C_PROBE_IN90_WIDTH=1,C_PROBE_IN91_WIDTH=1,C_PROBE_IN92_WIDTH=1,C_PROBE_IN93_WIDTH=1,C_PROBE_IN94_WIDTH=1,C_PROBE_IN95_WIDTH=1,C_PROBE_IN96_WIDTH=1,C_PROBE_IN97_WIDTH=1,C_PROBE_IN98_WIDTH=1,C_PROBE_IN99_WIDTH=1,C_PROBE_IN100_WIDTH=1,C_PROBE_IN101_WIDTH=1,C_PROBE_IN102_WIDTH=1,C_PROBE_IN103_WIDTH=1,C_PROBE_IN104_WIDTH=1,C_PROBE_IN105_WIDTH=1,C_PROBE_IN106_WIDTH=1,C_PROBE_IN107_WIDTH=1,C_PROBE_IN108_WIDTH=1,C_PROBE_IN109_WIDTH=1,C_PROBE_IN110_WIDTH=1,C_PROBE_IN111_WIDTH=1,C_PROBE_IN112_WIDTH=1,C_PROBE_IN113_WIDTH=1,C_PROBE_IN114_WIDTH=1,C_PROBE_IN115_WIDTH=1,C_PROBE_IN116_WIDTH=1,C_PROBE_IN117_WIDTH=1,C_PROBE_IN118_WIDTH=1,C_PROBE_IN119_WIDTH=1,C_PROBE_IN120_WIDTH=1,C_PROBE_IN121_WIDTH=1,C_PROBE_IN122_WIDTH=1,C_PROBE_IN123_WIDTH=1,C_PROBE_IN124_WIDTH=1,C_PROBE_IN125_WIDTH=1,C_PROBE_IN126_WIDTH=1,C_PROBE_IN127_WIDTH=1,C_PROBE_IN128_WIDTH=1,C_PROBE_IN129_WIDTH=1,C_PROBE_IN130_WIDTH=1,C_PROBE_IN131_WIDTH=1,C_PROBE_IN132_WIDTH=1,C_PROBE_IN133_WIDTH=1,C_PROBE_IN134_WIDTH=1,C_PROBE_IN135_WIDTH=1,C_PROBE_IN136_WIDTH=1,C_PROBE_IN137_WIDTH=1,C_PROBE_IN138_WIDTH=1,C_PROBE_IN139_WIDTH=1,C_PROBE_IN140_WIDTH=1,C_PROBE_IN141_WIDTH=1,C_PROBE_IN142_WIDTH=1,C_PROBE_IN143_WIDTH=1,C_PROBE_IN144_WIDTH=1,C_PROBE_IN145_WIDTH=1,C_PROBE_IN146_WIDTH=1,C_PROBE_IN147_WIDTH=1,C_PROBE_IN148_WIDTH=1,C_PROBE_IN149_WIDTH=1,C_PROBE_IN150_WIDTH=1,C_PROBE_IN151_WIDTH=1,C_PROBE_IN152_WIDTH=1,C_PROBE_IN153_WIDTH=1,C_PROBE_IN154_WIDTH=1,C_PROBE_IN155_WIDTH=1,C_PROBE_IN156_WIDTH=1,C_PROBE_IN157_WIDTH=1,C_PROBE_IN158_WIDTH=1,C_PROBE_IN159_WIDTH=1,C_PROBE_IN160_WIDTH=1,C_PROBE_IN161_WIDTH=1,C_PROBE_IN162_WIDTH=1,C_PROBE_IN163_WIDTH=1,C_PROBE_IN164_WIDTH=1,C_PROBE_IN165_WIDTH=1,C_PROBE_IN166_WIDTH=1,C_PROBE_IN167_WIDTH=1,C_PROBE_IN168_WIDTH=1,C_PROBE_IN169_WIDTH=1,C_PROBE_IN170_WIDTH=1,C_PROBE_IN171_WIDTH=1,C_PROBE_IN172_WIDTH=1,\
C_PROBE_IN173_WIDTH=1,C_PROBE_IN174_WIDTH=1,C_PROBE_IN175_WIDTH=1,C_PROBE_IN176_WIDTH=1,C_PROBE_IN177_WIDTH=1,C_PROBE_IN178_WIDTH=1,C_PROBE_IN179_WIDTH=1,C_PROBE_IN180_WIDTH=1,C_PROBE_IN181_WIDTH=1,C_PROBE_IN182_WIDTH=1,C_PROBE_IN183_WIDTH=1,C_PROBE_IN184_WIDTH=1,C_PROBE_IN185_WIDTH=1,C_PROBE_IN186_WIDTH=1,C_PROBE_IN187_WIDTH=1,C_PROBE_IN188_WIDTH=1,C_PROBE_IN189_WIDTH=1,C_PROBE_IN190_WIDTH=1,C_PROBE_IN191_WIDTH=1,C_PROBE_IN192_WIDTH=1,C_PROBE_IN193_WIDTH=1,C_PROBE_IN194_WIDTH=1,C_PROBE_IN195_WIDTH=1,C_PROBE_IN196_WIDTH=1,C_PROBE_IN197_WIDTH=1,C_PROBE_IN198_WIDTH=1,C_PROBE_IN199_WIDTH=1,C_PROBE_IN200_WIDTH=1,C_PROBE_IN201_WIDTH=1,C_PROBE_IN202_WIDTH=1,C_PROBE_IN203_WIDTH=1,C_PROBE_IN204_WIDTH=1,C_PROBE_IN205_WIDTH=1,C_PROBE_IN206_WIDTH=1,C_PROBE_IN207_WIDTH=1,C_PROBE_IN208_WIDTH=1,C_PROBE_IN209_WIDTH=1,C_PROBE_IN210_WIDTH=1,C_PROBE_IN211_WIDTH=1,C_PROBE_IN212_WIDTH=1,C_PROBE_IN213_WIDTH=1,C_PROBE_IN214_WIDTH=1,C_PROBE_IN215_WIDTH=1,C_PROBE_IN216_WIDTH=1,C_PROBE_IN217_WIDTH=1,C_PROBE_IN218_WIDTH=1,C_PROBE_IN219_WIDTH=1,C_PROBE_IN220_WIDTH=1,C_PROBE_IN221_WIDTH=1,C_PROBE_IN222_WIDTH=1,C_PROBE_IN223_WIDTH=1,C_PROBE_IN224_WIDTH=1,C_PROBE_IN225_WIDTH=1,C_PROBE_IN226_WIDTH=1,C_PROBE_IN227_WIDTH=1,C_PROBE_IN228_WIDTH=1,C_PROBE_IN229_WIDTH=1,C_PROBE_IN230_WIDTH=1,C_PROBE_IN231_WIDTH=1,C_PROBE_IN232_WIDTH=1,C_PROBE_IN233_WIDTH=1,C_PROBE_IN234_WIDTH=1,C_PROBE_IN235_WIDTH=1,C_PROBE_IN236_WIDTH=1,C_PROBE_IN237_WIDTH=1,C_PROBE_IN238_WIDTH=1,C_PROBE_IN239_WIDTH=1,C_PROBE_IN240_WIDTH=1,C_PROBE_IN241_WIDTH=1,C_PROBE_IN242_WIDTH=1,C_PROBE_IN243_WIDTH=1,C_PROBE_IN244_WIDTH=1,C_PROBE_IN245_WIDTH=1,C_PROBE_IN246_WIDTH=1,C_PROBE_IN247_WIDTH=1,C_PROBE_IN248_WIDTH=1,C_PROBE_IN249_WIDTH=1,C_PROBE_IN250_WIDTH=1,C_PROBE_IN251_WIDTH=1,C_PROBE_IN252_WIDTH=1,C_PROBE_IN253_WIDTH=1,C_PROBE_IN254_WIDTH=1,C_PROBE_IN255_WIDTH=1,C_PROBE_OUT0_WIDTH=1,C_PROBE_OUT1_WIDTH=1,C_PROBE_OUT2_WIDTH=1,C_PROBE_OUT3_WIDTH=1,C_PROBE_OUT4_WIDTH=1,C_PROBE_OUT5_WIDTH=1,C_PROBE_OUT6_WIDTH=1,C_PROBE_OUT7_WIDTH=1,C_PROBE_OUT8_WIDTH=1,C_PROBE_OUT9_WIDTH=1,C_PROBE_OUT10_WIDTH=1,C_PROBE_OUT11_WIDTH=1,C_PROBE_OUT12_WIDTH=1,C_PROBE_OUT13_WIDTH=1,C_PROBE_OUT14_WIDTH=1,C_PROBE_OUT15_WIDTH=1,C_PROBE_OUT16_WIDTH=1,\
C_PROBE_OUT17_WIDTH=1,C_PROBE_OUT18_WIDTH=1,C_PROBE_OUT19_WIDTH=1,C_PROBE_OUT20_WIDTH=1,C_PROBE_OUT21_WIDTH=1,C_PROBE_OUT22_WIDTH=1,C_PROBE_OUT23_WIDTH=1,C_PROBE_OUT24_WIDTH=1,C_PROBE_OUT25_WIDTH=1,C_PROBE_OUT26_WIDTH=1,C_PROBE_OUT27_WIDTH=1,C_PROBE_OUT28_WIDTH=1,C_PROBE_OUT29_WIDTH=1,C_PROBE_OUT30_WIDTH=1,C_PROBE_OUT31_WIDTH=1,C_PROBE_OUT32_WIDTH=1,C_PROBE_OUT33_WIDTH=1,C_PROBE_OUT34_WIDTH=1,C_PROBE_OUT35_WIDTH=1,C_PROBE_OUT36_WIDTH=1,C_PROBE_OUT37_WIDTH=1,C_PROBE_OUT38_WIDTH=1,C_PROBE_OUT39_WIDTH=1,C_PROBE_OUT40_WIDTH=1,C_PROBE_OUT41_WIDTH=1,C_PROBE_OUT42_WIDTH=1,C_PROBE_OUT43_WIDTH=1,C_PROBE_OUT44_WIDTH=1,C_PROBE_OUT45_WIDTH=1,C_PROBE_OUT46_WIDTH=1,C_PROBE_OUT47_WIDTH=1,C_PROBE_OUT48_WIDTH=1,C_PROBE_OUT49_WIDTH=1,C_PROBE_OUT50_WIDTH=1,C_PROBE_OUT51_WIDTH=1,C_PROBE_OUT52_WIDTH=1,C_PROBE_OUT53_WIDTH=1,C_PROBE_OUT54_WIDTH=1,C_PROBE_OUT55_WIDTH=1,C_PROBE_OUT56_WIDTH=1,C_PROBE_OUT57_WIDTH=1,C_PROBE_OUT58_WIDTH=1,C_PROBE_OUT59_WIDTH=1,C_PROBE_OUT60_WIDTH=1,C_PROBE_OUT61_WIDTH=1,C_PROBE_OUT62_WIDTH=1,C_PROBE_OUT63_WIDTH=1,C_PROBE_OUT64_WIDTH=1,C_PROBE_OUT65_WIDTH=1,C_PROBE_OUT66_WIDTH=1,C_PROBE_OUT67_WIDTH=1,C_PROBE_OUT68_WIDTH=1,C_PROBE_OUT69_WIDTH=1,C_PROBE_OUT70_WIDTH=1,C_PROBE_OUT71_WIDTH=1,C_PROBE_OUT72_WIDTH=1,C_PROBE_OUT73_WIDTH=1,C_PROBE_OUT74_WIDTH=1,C_PROBE_OUT75_WIDTH=1,C_PROBE_OUT76_WIDTH=1,C_PROBE_OUT77_WIDTH=1,C_PROBE_OUT78_WIDTH=1,C_PROBE_OUT79_WIDTH=1,C_PROBE_OUT80_WIDTH=1,C_PROBE_OUT81_WIDTH=1,C_PROBE_OUT82_WIDTH=1,C_PROBE_OUT83_WIDTH=1,C_PROBE_OUT84_WIDTH=1,C_PROBE_OUT85_WIDTH=1,C_PROBE_OUT86_WIDTH=1,C_PROBE_OUT87_WIDTH=1,C_PROBE_OUT88_WIDTH=1,C_PROBE_OUT89_WIDTH=1,C_PROBE_OUT90_WIDTH=1,C_PROBE_OUT91_WIDTH=1,C_PROBE_OUT92_WIDTH=1,C_PROBE_OUT93_WIDTH=1,C_PROBE_OUT94_WIDTH=1,C_PROBE_OUT95_WIDTH=1,C_PROBE_OUT96_WIDTH=1,C_PROBE_OUT97_WIDTH=1,C_PROBE_OUT98_WIDTH=1,C_PROBE_OUT99_WIDTH=1,C_PROBE_OUT100_WIDTH=1,C_PROBE_OUT101_WIDTH=1,C_PROBE_OUT102_WIDTH=1,C_PROBE_OUT103_WIDTH=1,C_PROBE_OUT104_WIDTH=1,C_PROBE_OUT105_WIDTH=1,C_PROBE_OUT106_WIDTH=1,C_PROBE_OUT107_WIDTH=1,C_PROBE_OUT108_WIDTH=1,C_PROBE_OUT109_WIDTH=1,C_PROBE_OUT110_WIDTH=1,C_PROBE_OUT111_WIDTH=1,C_PROBE_OUT112_WIDTH=1,C_PROBE_OUT113_WIDTH=1,C_PROBE_OUT114_WIDTH=1,C_PROBE_OUT115_WIDTH=1,C_PROBE_OUT116_WIDTH=1,\
C_PROBE_OUT117_WIDTH=1,C_PROBE_OUT118_WIDTH=1,C_PROBE_OUT119_WIDTH=1,C_PROBE_OUT120_WIDTH=1,C_PROBE_OUT121_WIDTH=1,C_PROBE_OUT122_WIDTH=1,C_PROBE_OUT123_WIDTH=1,C_PROBE_OUT124_WIDTH=1,C_PROBE_OUT125_WIDTH=1,C_PROBE_OUT126_WIDTH=1,C_PROBE_OUT127_WIDTH=1,C_PROBE_OUT128_WIDTH=1,C_PROBE_OUT129_WIDTH=1,C_PROBE_OUT130_WIDTH=1,C_PROBE_OUT131_WIDTH=1,C_PROBE_OUT132_WIDTH=1,C_PROBE_OUT133_WIDTH=1,C_PROBE_OUT134_WIDTH=1,C_PROBE_OUT135_WIDTH=1,C_PROBE_OUT136_WIDTH=1,C_PROBE_OUT137_WIDTH=1,C_PROBE_OUT138_WIDTH=1,C_PROBE_OUT139_WIDTH=1,C_PROBE_OUT140_WIDTH=1,C_PROBE_OUT141_WIDTH=1,C_PROBE_OUT142_WIDTH=1,C_PROBE_OUT143_WIDTH=1,C_PROBE_OUT144_WIDTH=1,C_PROBE_OUT145_WIDTH=1,C_PROBE_OUT146_WIDTH=1,C_PROBE_OUT147_WIDTH=1,C_PROBE_OUT148_WIDTH=1,C_PROBE_OUT149_WIDTH=1,C_PROBE_OUT150_WIDTH=1,C_PROBE_OUT151_WIDTH=1,C_PROBE_OUT152_WIDTH=1,C_PROBE_OUT153_WIDTH=1,C_PROBE_OUT154_WIDTH=1,C_PROBE_OUT155_WIDTH=1,C_PROBE_OUT156_WIDTH=1,C_PROBE_OUT157_WIDTH=1,C_PROBE_OUT158_WIDTH=1,C_PROBE_OUT159_WIDTH=1,C_PROBE_OUT160_WIDTH=1,C_PROBE_OUT161_WIDTH=1,C_PROBE_OUT162_WIDTH=1,C_PROBE_OUT163_WIDTH=1,C_PROBE_OUT164_WIDTH=1,C_PROBE_OUT165_WIDTH=1,C_PROBE_OUT166_WIDTH=1,C_PROBE_OUT167_WIDTH=1,C_PROBE_OUT168_WIDTH=1,C_PROBE_OUT169_WIDTH=1,C_PROBE_OUT170_WIDTH=1,C_PROBE_OUT171_WIDTH=1,C_PROBE_OUT172_WIDTH=1,C_PROBE_OUT173_WIDTH=1,C_PROBE_OUT174_WIDTH=1,C_PROBE_OUT175_WIDTH=1,C_PROBE_OUT176_WIDTH=1,C_PROBE_OUT177_WIDTH=1,C_PROBE_OUT178_WIDTH=1,C_PROBE_OUT179_WIDTH=1,C_PROBE_OUT180_WIDTH=1,C_PROBE_OUT181_WIDTH=1,C_PRO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
C_PROBE_OUT61_INIT_VAL=0,C_PROBE_OUT62_INIT_VAL=0,C_PROBE_OUT63_INIT_VAL=0,C_PROBE_OUT64_INIT_VAL=0,C_PROBE_OUT65_INIT_VAL=0,C_PROBE_OUT66_INIT_VAL=0,C_PROBE_OUT67_INIT_VAL=0,C_PROBE_OUT68_INIT_VAL=0,C_PROBE_OUT69_INIT_VAL=0,C_PROBE_OUT70_INIT_VAL=0,C_PROBE_OUT71_INIT_VAL=0,C_PROBE_OUT72_INIT_VAL=0,C_PROBE_OUT73_INIT_VAL=0,C_PROBE_OUT74_INIT_VAL=0,C_PROBE_OUT75_INIT_VAL=0,C_PROBE_OUT76_INIT_VAL=0,C_PROBE_OUT77_INIT_VAL=0,C_PROBE_OUT78_INIT_VAL=0,C_PROBE_OUT79_INIT_VAL=0,C_PROBE_OUT80_INIT_VAL=0,C_PROBE_OUT81_INIT_VAL=0,C_PROBE_OUT82_INIT_VAL=0,C_PROBE_OUT83_INIT_VAL=0,C_PROBE_OUT84_INIT_VAL=0,C_PROBE_OUT85_INIT_VAL=0,C_PROBE_OUT86_INIT_VAL=0,C_PROBE_OUT87_INIT_VAL=0,C_PROBE_OUT88_INIT_VAL=0,C_PROBE_OUT89_INIT_VAL=0,C_PROBE_OUT90_INIT_VAL=0,C_PROBE_OUT91_INIT_VAL=0,C_PROBE_OUT92_INIT_VAL=0,C_PROBE_OUT93_INIT_VAL=0,C_PROBE_OUT94_INIT_VAL=0,C_PROBE_OUT95_INIT_VAL=0,C_PROBE_OUT96_INIT_VAL=0,C_PROBE_OUT97_INIT_VAL=0,C_PROBE_OUT98_INIT_VAL=0,C_PROBE_OUT99_INIT_VAL=0,C_PROBE_OUT100_INIT_VAL=0,C_PROBE_OUT101_INIT_VAL=0,C_PROBE_OUT102_INIT_VAL=0,C_PROBE_OUT103_INIT_VAL=0,C_PROBE_OUT104_INIT_VAL=0,C_PROBE_OUT105_INIT_VAL=0,C_PROBE_OUT106_INIT_VAL=0,C_PROBE_OUT107_INIT_VAL=0,C_PROBE_OUT108_INIT_VAL=0,C_PROBE_OUT109_INIT_VAL=0,C_PROBE_OUT110_INIT_VAL=0,C_PROBE_OUT111_INIT_VAL=0,C_PROBE_OUT112_INIT_VAL=0,C_PROBE_OUT113_INIT_VAL=0,C_PROBE_OUT114_INIT_VAL=0,C_PROBE_OUT115_INIT_VAL=0,C_PROBE_OUT116_INIT_VAL=0,C_PROBE_OUT117_INIT_VAL=0,C_PROBE_OUT118_INIT_VAL=0,C_PROBE_OUT119_INIT_VAL=0,C_PROBE_OUT120_INIT_VAL=0,C_PROBE_OUT121_INIT_VAL=0,C_PROBE_OUT122_INIT_VAL=0,C_PROBE_OUT123_INIT_VAL=0,C_PROBE_OUT124_INIT_VAL=0,C_PROBE_OUT125_INIT_VAL=0,C_PROBE_OUT126_INIT_VAL=0,C_PROBE_OUT127_INIT_VAL=0,C_PROBE_OUT128_INIT_VAL=0,C_PROBE_OUT129_INIT_VAL=0,C_PROBE_OUT130_INIT_VAL=0,C_PROBE_OUT131_INIT_VAL=0,C_PROBE_OUT132_INIT_VAL=0,C_PROBE_OUT133_INIT_VAL=0,C_PROBE_OUT134_INIT_VAL=0,C_PROBE_OUT135_INIT_VAL=0,C_PROBE_OUT136_INIT_VAL=0,C_PROBE_OUT137_INIT_VAL=0,C_PROBE_OUT138_INIT_VAL=0,C_PROBE_OUT139_INIT_VAL=0,C_PROBE_OUT140_INIT_VAL=0,C_PROBE_OUT141_INIT_VAL=0,C_PROBE_OUT142_INIT_VAL=0,C_PROBE_OUT143_INIT_VAL=0,C_PROBE_OUT144_INIT_VAL=0,C_PROBE_OUT145_INIT_VAL=0,C_PROBE_OUT146_INIT_VAL=0,C_PROBE_OUT147_INIT_VAL=0,C_PROBE_OUT148_INIT_VAL=0,C_PROBE_OUT149_INIT_VAL=0,C_PROBE_OUT150_INIT_VAL=0,C_PROBE_OUT151_INIT_VAL=0,C_PROBE_OUT152_INIT_VAL=0,C_PROBE_OUT153_INIT_VAL=0,C_PROBE_OUT154_INIT_VAL=0,C_PROBE_OUT155_INIT_VAL=0,C_PROBE_OUT156_INIT_VAL=0,C_PROBE_OUT157_INIT_VAL=0,C_PROBE_OUT158_INIT_VAL=0,C_PROBE_OUT159_INIT_VAL=0,C_PROBE_OUT160_INIT_VAL=0,\
C_PROBE_OUT161_INIT_VAL=0,C_PROBE_OUT162_INIT_VAL=0,C_PROBE_OUT163_INIT_VAL=0,C_PROBE_OUT164_INIT_VAL=0,C_PROBE_OUT165_INIT_VAL=0,C_PROBE_OUT166_INIT_VAL=0,C_PROBE_OUT167_INIT_VAL=0,C_PROBE_OUT168_INIT_VAL=0,C_PROBE_OUT169_INIT_VAL=0,C_PROBE_OUT170_INIT_VAL=0,C_PROBE_OUT171_INIT_VAL=0,C_PROBE_OUT172_INIT_VAL=0,C_PROBE_OUT173_INIT_VAL=0,C_PROBE_OUT174_INIT_VAL=0,C_PROBE_OUT175_INIT_VAL=0,C_PROBE_OUT176_INIT_VAL=0,C_PROBE_OUT177_INIT_VAL=0,C_PROBE_OUT178_INIT_VAL=0,C_PROBE_OUT179_INIT_VAL=0,C_PROBE_OUT180_INIT_VAL=0,C_PROBE_OUT181_INIT_VAL=0,C_PROBE_OUT182_INIT_VAL=0,C_PROBE_OUT183_INIT_VAL=0,C_PROBE_OUT184_INIT_VAL=0,C_PROBE_OUT185_INIT_VAL=0,C_PROBE_OUT186_INIT_VAL=0,C_PROBE_OUT187_INIT_VAL=0,C_PROBE_OUT188_INIT_VAL=0,C_PROBE_OUT189_INIT_VAL=0,C_PROBE_OUT190_INIT_VAL=0,C_PROBE_OUT191_INIT_VAL=0,C_PROBE_OUT192_INIT_VAL=0,C_PROBE_OUT193_INIT_VAL=0,C_PROBE_OUT194_INIT_VAL=0,C_PROBE_OUT195_INIT_VAL=0,C_PROBE_OUT196_INIT_VAL=0,C_PROBE_OUT197_INIT_VAL=0,C_PROBE_OUT198_INIT_VAL=0,C_PROBE_OUT199_INIT_VAL=0,C_PROBE_OUT200_INIT_VAL=0,C_PROBE_OUT201_INIT_VAL=0,C_PROBE_OUT202_INIT_VAL=0,C_PROBE_OUT203_INIT_VAL=0,C_PROBE_OUT204_INIT_VAL=0,C_PROBE_OUT205_INIT_VAL=0,C_PROBE_OUT206_INIT_VAL=0,C_PROBE_OUT207_INIT_VAL=0,C_PROBE_OUT208_INIT_VAL=0,C_PROBE_OUT209_INIT_VAL=0,C_PROBE_OUT210_INIT_VAL=0,C_PROBE_OUT211_INIT_VAL=0,C_PROBE_OUT212_INIT_VAL=0,C_PROBE_OUT213_INIT_VAL=0,C_PROBE_OUT214_INIT_VAL=0,C_PROBE_OUT215_INIT_VAL=0,C_PROBE_OUT216_INIT_VAL=0,C_PROBE_OUT217_INIT_VAL=0,C_PROBE_OUT218_INIT_VAL=0,C_PROBE_OUT219_INIT_VAL=0,C_PROBE_OUT220_INIT_VAL=0,C_PROBE_OUT221_INIT_VAL=0,C_PROBE_OUT222_INIT_VAL=0,C_PROBE_OUT223_INIT_VAL=0,C_PROBE_OUT224_INIT_VAL=0,C_PROBE_OUT225_INIT_VAL=0,C_PROBE_OUT226_INIT_VAL=0,C_PROBE_OUT227_INIT_VAL=0,C_PROBE_OUT228_INIT_VAL=0,C_PROBE_OUT229_INIT_VAL=0,C_PROBE_OUT230_INIT_VAL=0,C_PROBE_OUT231_INIT_VAL=0,C_PROBE_OUT232_INIT_VAL=0,C_PROBE_OUT233_INIT_VAL=0,C_PROBE_OUT234_INIT_VAL=0,C_PROBE_OUT235_INIT_VAL=0,C_PROBE_OUT236_INIT_VAL=0,C_PROBE_OUT237_INIT_VAL=0,C_PROBE_OUT238_INIT_VAL=0,C_PROBE_OUT239_INIT_VAL=0,C_PROBE_OUT240_INIT_VAL=0,C_PROBE_OUT241_INIT_VAL=0,C_PROBE_OUT242_INIT_VAL=0,C_PROBE_OUT243_INIT_VAL=0,C_PROBE_OUT244_INIT_VAL=0,C_PROBE_OUT245_INIT_VAL=0,C_PROBE_OUT246_INIT_VAL=0,C_PROBE_OUT247_INIT_VAL=0,C_PROBE_OUT248_INIT_VAL=0,C_PROBE_OUT249_INIT_VAL=0,C_PROBE_OUT250_INIT_VAL=0,C_PROBE_OUT251_INIT_VAL=0,C_PROBE_OUT252_INIT_VAL=0,C_PROBE_OUT253_INIT_VAL=0,C_PROBE_OUT254_INIT_VAL=0,C_PROBE_OUT255_INIT_VAL=0}" *)
module vio_0 (
clk,
probe_in0,probe_in1,probe_in2,probe_in3,probe_in4,probe_in5,probe_in6,probe_in7

);

input clk;
input [11 : 0] probe_in0;
input [11 : 0] probe_in1;
input [11 : 0] probe_in2;
input [11 : 0] probe_in3;
input [0 : 0] probe_in4;
input [0 : 0] probe_in5;
input [0 : 0] probe_in6;
input [0 : 0] probe_in7;



wire [16:0] sl_oport0;
wire [36:0] sl_iport0;

vio_v3_0_25_vio #(
.C_XLNX_HW_PROBE_INFO("DEFAULT"),
.C_XDEVICEFAMILY("artix7"),
.C_CORE_TYPE(2),
.C_CORE_INFO1(0),
.C_CORE_INFO2(0),
.C_NUM_PROBE_IN(8),
.C_EN_PROBE_IN_ACTIVITY(1),
.C_NUM_PROBE_OUT(0),
.C_MAJOR_VERSION(2013),
.C_MINOR_VERSION(1),
.C_BUILD_REVISION(0),
.C_CORE_MAJOR_VER(2),
.C_CORE_MINOR_VER(0),
.C_CORE_MINOR_ALPHA_VER(97),
.C_XSDB_SLAVE_TYPE(33),
.C_NEXT_SLAVE(0),
.C_CSE_DRV_VER(1),
.C_USE_TEST_REG(1),
.C_PIPE_IFACE(0),
.C_PROBE_IN0_WIDTH(12),
.C_PROBE_IN1_WIDTH(12),
.C_PROBE_IN2_WIDTH(12),
.C_PROBE_IN3_WIDTH(12),
.C_PROBE_IN4_WIDTH(1),
.C_PROBE_IN5_WIDTH(1),
.C_PROBE_IN6_WIDTH(1),
.C_PROBE_IN7_WIDTH(1),
.C_PROBE_IN8_WIDTH(1),
.C_PROBE_IN9_WIDTH(1),
.C_PROBE_IN10_WIDTH(1),
.C_PROBE_IN11_WIDTH(1),
.C_PROBE_IN12_WIDTH(1),
.C_PROBE_IN13_WIDTH(1),
.C_PROBE_IN14_WIDTH(1),
.C_PROBE_IN15_WIDTH(1),
.C_PROBE_IN16_WIDTH(1),
.C_PROBE_IN17_WIDTH(1),
.C_PROBE_IN18_WIDTH(1),
.C_PROBE_IN19_WIDTH(1),
.C_PROBE_IN20_WIDTH(1),
.C_PROBE_IN21_WIDTH(1),
.C_PROBE_IN22_WIDTH(1),
.C_PROBE_IN23_WIDTH(1),
.C_PROBE_IN24_WIDTH(1),
.C_PROBE_IN25_WIDTH(1),
.C_PROBE_IN26_WIDTH(1),
.C_PROBE_IN27_WIDTH(1),
.C_PROBE_IN28_WIDTH(1),
.C_PROBE_IN29_WIDTH(1),
.C_PROBE_IN30_WIDTH(1),
.C_PROBE_IN31_WIDTH(1),
.C_PROBE_IN32_WIDTH(1),
.C_PROBE_IN33_WIDTH(1),
.C_PROBE_IN34_WIDTH(1),
.C_PROBE_IN35_WIDTH(1),
.C_PROBE_IN36_WIDTH(1),
.C_PROBE_IN37_WIDTH(1),
.C_PROBE_IN38_WIDTH(1),
.C_PROBE_IN39_WIDTH(1),
.C_PROBE_IN40_WIDTH(1),
.C_PROBE_IN41_WIDTH(1),
.C_PROBE_IN42_WIDTH(1),
.C_PROBE_IN43_WIDTH(1),
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
.probe_out241(),
.probe_out242(),
.probe_out243(),
.probe_out244(),
.probe_out245(),
.probe_out246(),
.probe_out247(),
.probe_out248(),
.probe_out249(),
.probe_out250(),
.probe_out251(),
.probe_out252(),
.probe_out253(),
.probe_out254(),
.probe_out255()
)/* synthesis syn_noprune=1 */;
endmodule
