AndreiBertescu/FPGA_Cosmic_Radiation_Sensor/Verilog source code - V7.10/Detector_unit_V5_Simplified.ip_user_files/ipstatic/hdl/ecc_v2_0_vl_rfs.v

`pragma protect begin_protected
`pragma protect version = 1
`pragma protect encrypt_agent = "XILINX"
`pragma protect encrypt_agent_info = "Xilinx Encryption Tool 2024.1"
`pragma protect key_keyowner = "Synopsys", key_keyname = "SNPS-VCS-RSA-2", key_method = "rsa"
`pragma protect encoding = (enctype = "BASE64", line_length = 76, bytes = 128)
`pragma protect key_block
hsZx6PE0FStzS2rs767ultBdwZlTnTJQLLGTs1J3eZ0+YFK3CGiPDqGBeoHN+8AwnGQ6Ku8z1RGS
fJQdizsWWrGxciIFRK2RdZTsv722ki/C99ht5UGo4sDU7d1O1B17unW21KsN86k5U/9FmErZ1KQC
ZZfNAOuAaOMgmL9D09M=

`pragma protect key_keyowner = "Aldec", key_keyname = "ALDEC15_001", key_method = "rsa"
`pragma protect encoding = (enctype = "BASE64", line_length = 76, bytes = 256)
`pragma protect key_block
wTMCy/rJZqy1tAf2RHbANxKCQmF4yvXq1WLcBhH3Kck4zpqz7ffzD5FC8A/CBkFYgQbniQzzYG0h
qzAKGCSf3ASzpbv5ch91wQp+8Vj06N/eTsGCSmJBXszYKQRiPilSbKb2ra9jTAN4lC50I5rv+Wed
vKxSF86aSwXt96zbgs7rU0K5fieIFSqTlkQZf55Zry6yQToT0Icng677Cxlj8YtFoIoPbVkSB/vS
J49YEB7LhAdJxZ7mVef6jTQxtFk5zlyLvcYXIl5JNhv6XQbCheFltedxfLxq3C/LPj3l38Z0qnZ6
Yub+tTfu36FZ3QMrL8gslV08DSa7/I13TNBwzg==

`pragma protect key_keyowner = "Mentor Graphics Corporation", key_keyname = "MGC-VELOCE-RSA", key_method = "rsa"
`pragma protect encoding = (enctype = "BASE64", line_length = 76, bytes = 128)
`pragma protect key_block
FTbyo3MpsPhbl506IC+3kb/1hKSijQ+mHCLdgl0SP8q+7Gm+vNFLeI/1CAEkT8AltR3uwQppZGas
yItmvPhWu+gVAZrfSUuSSf10XtU5oSzkGzSLSW1SW8zhy/5X8/+lZPMl14Qrhrci9ETz/f1RVjQS
gfzD4/B8CuUTt09uTL8=

`pragma protect key_keyowner = "Mentor Graphics Corporation", key_keyname = "MGC-VERIF-SIM-RSA-2", key_method = "rsa"
`pragma protect encoding = (enctype = "BASE64", line_length = 76, bytes = 256)
`pragma protect key_block
JxcqSHHdWTVEMW0DbMyyDb//O3lg/FdK7MtqtiAGhOt4qC7nxuFvhHn/2UiRHp90ELsEUPjeQR31
WkRENQIWHogTijUhcEv+0enHOYsdg2HpzcgZ8Pc7Jrrd5ixmdVkB/+qcABHtgcSBLIGJjC/WTTGe
YAgdlDssnkFf9J1PEh9yJoAxqvLHTIgRqFJFLQeL1fRJAdyBxdlclcw/dBhrmLBxG+lgeFkrAD1r
Ly+WKRPMt+P9t9EE/SXgyKW5+AEzde+bcx0IxdeN2GtDpsWrfI1SAiO4JrNeEEqXLz26NEiyGc2j
nkGr72i5kroRkSESYameUv3uxgjHL5/qwcp56w==

`pragma protect key_keyowner = "Real Intent", key_keyname = "RI-RSA-KEY-1", key_method = "rsa"
`pragma protect encoding = (enctype = "BASE64", line_length = 76, bytes = 256)
`pragma protect key_block
KfKptzu3Tvg1PS0AgnTS7y1it8/FtWXmFjxFQrPXXFdie6m7bUPJUhO8uAbmb151/edUbVPWNxTi
FFD8q7M+zZyEHmgQBylHutUxIrGkNMwAsPLmfHmqwz1dIxtcYvKfptr0ou2E5pNM4WcbbIyvnie7
9/27+hKEhbGUb7OjeTs6dcI+W5/rS5EZ2qAR5bs7Ty9glyAa/e3ILw6484+8MuijPqRqhNvyDimH
IWib/NcjACR2J1gGP02tcWyplRe0HKIM/aconVJGXc2CjZWmOPejcu5+CXSCpwR13+Nw5EvGyz37
Em4JYDy8Ucfn49nSe+4u0VF+jsNRwuQJSILCvA==

`pragma protect key_keyowner = "Metrics Technologies Inc.", key_keyname = "DSim", key_method = "rsa"
`pragma protect encoding = (enctype = "BASE64", line_length = 76, bytes = 256)
`pragma protect key_block
eixqOWZoLjqEzWMAKn/OMFkFDU1Uip47pajHazAkGJSuDJ3H996JSc0c82IyTRCzSzp7oIj/9akK
//E1ps0gO9OkY4Ft4/hgsdrNg8S75skQBUSlFhSxZO8VolsAPI2Ez4JI5ghqcUVNZ5q5vOR5fTBY
yn5oT8lDmiHwJAecWLEsHo0TEdwlhufg+DwO2Crkvxw4i4RnyIR/6H/5v9WY6ZRBz7bNw1y5pu9W
cqEETqbKBjgJ7+GaWSWG3Z2oT3pS6Mdj4Gs9P8vwUOY5+JefnMqXmyGmQaRqaQJ3mNMFp8ggw48b
S1JXno71N10pFKwhrxtJ9pd8Na6tHF2nhHskLQ==

`pragma protect key_keyowner = "Xilinx", key_keyname = "xilinxt_2023_11", key_method = "rsa"
`pragma protect encoding = (enctype = "BASE64", line_length = 76, bytes = 256)
`pragma protect key_block
t4HCltIWFZ3AI1SqSInyaMYOw2RUQzeQYq3bOiU0o4xKtmLwir1Bfrw4D5o+KiGCyDmi2k7J0Xsb
/rK8U58pjA4PM59emO12ictAuDD5uzoh7fAL8fY0j5E0pmVOaS8qNr99gPsUece8Lbvr5yyRAT9O
WwWAKGINYwFciaI2e1lRqma14CoXJg2VT7t0Up/ZzAW/kpm0t2Pd+2X8YUSrv0ERXh9mzJQFdsKh
CaHCiGV+td5vL/+7Zrr8ICkVgSg2LyCiwycFUkWGbQXBTmfKs1dcULOkUQfFmNi99Av+pdNVZpMT
Pyuuexu7B76Z2eIlvSa4bjVVnFZVhiitboyKnA==

`pragma protect key_keyowner = "Atrenta", key_keyname = "ATR-SG-RSA-1", key_method = "rsa"
`pragma protect encoding = (enctype = "BASE64", line_length = 76, bytes = 384)
`pragma protect key_block
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

`pragma protect key_keyowner = "Cadence Design Systems.", key_keyname = "CDS_RSA_KEY_VER_1", key_method = "rsa"
`pragma protect encoding = (enctype = "BASE64", line_length = 76, bytes = 256)
`pragma protect key_block
jd7pB0vC7gshrzsrm8/6zSc4EEVFEococ6Wm47H9WJ+yt3xGXlsfQvWCCBTKmofxJXsYyWvOL15K
Sx5a+Tl5ZBRCYNlhszaTqL1o/HsCLR/DrWRhmQDEYc7iXOd4XrAaExp8cT05vXfk8wDwd2XXJ8DA
URtv7WG8XmlPoUNdrCsnvPHFeAq2Aw+HTl2IChBlf+RJFq7AJmKMjTdd+jXUdJEDGF+rYoiOqVAa
wxgqp3YT2HuTCWhdDpEASgD78c4AQr2BovQqpHfyk0sOLYJzPfF/BncSsvwGKAh0/C7DEp5Gu88Z
VR54fpXryNpXhdb4TeFqC0fF1Vk70MGC6EbEeg==

`pragma protect data_method = "AES128-CBC"
`pragma protect encoding = (enctype = "BASE64", line_length = 76, bytes = 114880)
`pragma protect data_block
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
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
