AndreiBertescu/FPGA_Cosmic_Radiation_Sensor/Verilog source code - V7.10/Detector_unit_V5_Simplified.ip_user_files/ipstatic/hdl/sem_v4_1_vl_rfs.v

`pragma protect begin_protected
`pragma protect version = 1
`pragma protect encrypt_agent = "XILINX"
`pragma protect encrypt_agent_info = "Xilinx Encryption Tool 2024.1"
`pragma protect key_keyowner = "Synopsys", key_keyname = "SNPS-VCS-RSA-2", key_method = "rsa"
`pragma protect encoding = (enctype = "BASE64", line_length = 76, bytes = 128)
`pragma protect key_block
c8rluOV4+lWm6sK7NatO2fjlQiysWLzs5fPsR9K/bdgkve2lFlqoKqQWRF7p4yqjdtNBjozKk2QV
mmoeVgwMXYQRu8GLb9qNnIqanswaLRJ1A14xEeIZc/S1P2HLuxB9zOIJd0AS2PXZ9Yl0FLHC0uIc
idL7AbWN+aBulc5/q/4=

`pragma protect key_keyowner = "Aldec", key_keyname = "ALDEC15_001", key_method = "rsa"
`pragma protect encoding = (enctype = "BASE64", line_length = 76, bytes = 256)
`pragma protect key_block
JeM7957vauz/UsuWa+irVIGce4VEcO8o+y+tgN9M4NxQQ0URXl0fAszaSX3zgXWIpPDmlC1Fe8nA
NylVpMOUPhHONvFRi5EzQkeIjqUK0og7Y6zq/DkUK45i0GYM+FK8ZnpX/nO6mH0ZyZikHs7QmhxS
kejAb9uymX/EA0bb6AubHfvt5rw55XGZNUMs0LHQdR+hTX3a2Lwoxc4qzv95SPAIjqunBccVlJua
0pBIaWMe07p9XfwqVGEfJVJeBtIHi1VzlA1IuKB3af0RfHnxZj9Ucp3HulsvJjlS0ar4NfVaPkul
4PrgVWpjDsjGwyFlCVjqEPxkILRMppg6xM2F1Q==

`pragma protect key_keyowner = "Mentor Graphics Corporation", key_keyname = "MGC-VELOCE-RSA", key_method = "rsa"
`pragma protect encoding = (enctype = "BASE64", line_length = 76, bytes = 128)
`pragma protect key_block
E9hf4shMoiwERIfNDS/o7YliaAbU6aMyQt2akTERryWja1CsbK9F6dfntwFo+ZTL7viOrzYjhWqh
DQwUAE5c/gWG8I5C8pLY4HEWfvJfr0WNB7Kiw6EtHAamAI85lVQxjOylfhoTDea+QDDlGRgJ3UME
xF8zB3XyIZau/3zRPSI=

`pragma protect key_keyowner = "Mentor Graphics Corporation", key_keyname = "MGC-VERIF-SIM-RSA-2", key_method = "rsa"
`pragma protect encoding = (enctype = "BASE64", line_length = 76, bytes = 256)
`pragma protect key_block
sAyHF+ImOVUCnCFog0M2so6au1YwsriqEBHgipku/oD8y7Hxli/ZNC8uJxYLgwfTN/VM9czvnUAW
TrJo/ggA+NLzRSJpXcPH7+9tzL/9na3vuiO/21k4ShUCi5lS10S5VDYyieH73t/UWJgVXDrAr41F
SNzKqCk6TmiHZgklbECT7OVRJMuYOUSB+YZPvrPW8zEfgMzc5RsuO81qXgRPSidCVAeULbVBSt0/
+yvFJKgXrDX1pcNByhhzxkoDTiDYHOXRFpQnA8BNEjwqjuHeVYcr+YCzpyFf9JmAfiGO5NVVrMWP
sOh4Lcr64wlNXKyG0fYZg5blm47Qf8bgVeJqPA==

`pragma protect key_keyowner = "Real Intent", key_keyname = "RI-RSA-KEY-1", key_method = "rsa"
`pragma protect encoding = (enctype = "BASE64", line_length = 76, bytes = 256)
`pragma protect key_block
R9rdduOcCvDktZIEA3po3fYRnOKTkRIknfPapT24uSlaB0R2woELSUX9/j03GObHU3ly2CUTvcRT
UhLTXf3gmaHmNcCsCqDPS//zcSdE9XJg5F7uBEiiLbG1yDRoPhj6LoOeeqsXcicCXnJJVRsmTpMo
zQCpQJS25jAtu1/W2jKm9OKu6GZO3o2gr8SvFGuARpZLZzAhivCeD0Vf4u4Tb/9WcB+LA/pZsPX4
efTapDZR5n5L3tl9pAR9KfH2tKjpKDyMnsS0lEpgJbaVlW7DTlV//vzPuAH5mriWNQL55QT5d6Yt
EdGT0GWVs2ufyeWsH9R5De2TkhVzE1JMnh0aeA==

`pragma protect key_keyowner = "Metrics Technologies Inc.", key_keyname = "DSim", key_method = "rsa"
`pragma protect encoding = (enctype = "BASE64", line_length = 76, bytes = 256)
`pragma protect key_block
YT8iAiS+NB2rSbKCWiP40q3A1NTPX61vnYY335avzUvWW8jCBYiaFe8tKHI5WTTlIvsT3oRBa3Qu
bqxUA3GWYMPLklnK2jSjf8Z+MluJy0JkjjkoC3dzMCohj2O3/H1qk0n5NvDvmzaQmK5QRzh6Q8CN
awgA9yyb/qxfO9+0fXIxbgunvDcpoAQG+lumS30q8e6FEb6yOf74Xop4yOpSXGVLLUFMQS7XhbEU
32iGRAmvRqtW4w07Hpl2Pe/IZ2BGQCSPE1Xwxf9zHyHNb1lnt2aid6qmd0Ykl8IkIhX+im2FmayR
ypOt/RCGA5r7hBEjbJ0feHn7LxZxUv0geLHE3g==

`pragma protect key_keyowner = "Xilinx", key_keyname = "xilinxt_2023_11", key_method = "rsa"
`pragma protect encoding = (enctype = "BASE64", line_length = 76, bytes = 256)
`pragma protect key_block
CC/1/ho5lkW9iLPXQ1Br/EbWTCa8Y5GBLCmltdDjs1eHEuCY9fp7l0/7AhJydgmG2hZqNpU8t1h3
Jvy9edUcy8sc0Q5/fIeIzu+PuKI/dobeeZfSCK4qnXjtDFufHSGzUbWC8L6bKnNuEarFRv6NbGrL
d3e18Nkqi67oUO6MaNq1h0lzLBo+9chuBv6J2JKZIkNVO37kazbF6iflH11w8x5hK9xgklGa6iYn
oEtHg8/5pNgTtfv1r2imHzTsMuWsWqf48xqLfCCrKH9pN4cXFvKKPyP6K6Zoifgs64V7B/MdY2z/
11WmYRNS42rXDgFakul5XyL2X2bQJgzC7TDj5g==

`pragma protect key_keyowner = "Atrenta", key_keyname = "ATR-SG-RSA-1", key_method = "rsa"
`pragma protect encoding = (enctype = "BASE64", line_length = 76, bytes = 384)
`pragma protect key_block
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

`pragma protect key_keyowner = "Cadence Design Systems.", key_keyname = "CDS_RSA_KEY_VER_1", key_method = "rsa"
`pragma protect encoding = (enctype = "BASE64", line_length = 76, bytes = 256)
`pragma protect key_block
NGx5jVyqyqLBHadhnApAdP327GeOg2oyvIHAuWGd5J+rtbAF+NC0N0rK9390BIZ5HOTTP7nH8JmI
8N+dewqqOs9TlfJ8COiUfHMAcosJOzj3bn6tZOt5763JbI6SlKibpMPEPk0jyR4gMXgS6NNvzMbE
mOzS+6Qo3Tz0DyENV4mkjj4snpUArii18UjsVBv4O50Utm3EwWJbquLUJHUQH9NniwfiLIkYGoRg
By2S6KZXlPWsxHZtmSX807/vzKnEXPnmS/UMr4BbtZcjC+P1rG4YpEXJdpoFeLDFMKgA3eraLGXT
bQ25RYJnxah6Jz0rJyfroubUrw5aVdjk63EQiw==

`pragma protect data_method = "AES128-CBC"
`pragma protect encoding = (enctype = "BASE64", line_length = 76, bytes = 309904)
`pragma protect data_block
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
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
